fukukawa89/PoseDollLab_Design/Hardware/PoseDoll44/bench/revO15/PROCUREMENT_MANNY.zh-CN.md

# Manny 采购数量

现有小样能复用的标准金属件可扣除。塑料件按整机编号，不混用旧底座。

| 规格 | 净数量 | 可选备件 | 建议总数 |
|---|---:|---:|---:|
| A8不锈钢碟簧：8×4.2×0.4，自由高0.6 mm，弹力待测 | 104 | 11 | 115 |
| Rev C mini传感PCBA：12×10×1 mm，按配套电路文件加工 | 46 | 2 | 48 |
| O15 C1中央采集PCBA：70×60×1.2 mm，四层板，按配套电路文件加工 | 1 | 0 | 1 |
| 6P 0.5mm FFC短尾线，宽3.5、厚0.2、长15 mm；每端补强≥3.5 mm，按图加六根32AWG短引线 | 46 | 4 | 50 |
| 1×7、2.54 mm排针；XIAO与载板间距4.0 mm定位焊接 | 2 | 0 | 2 |
| JST GHR-06V-S壳+SSHL-002T-P0.2端子；26AWG短引线转24AWG，绝缘外径0.76–1.0 mm，6P、1.25 mm；让线束厂压接 | 6 | 0 | 6 |
| JST PHR-2壳+SPH-002T-P0.5S端子，2P、2.0 mm；5V输入 | 1 | 0 | 1 |
| JST PHR-3壳+SPH-002T-P0.5S端子，3P、2.0 mm；降压模块连接 | 1 | 0 | 1 |
| 径向两极磁铁 Φ6×2.5 mm；直径方向充磁，不能买轴向充磁 | 46 | 5 | 51 |
| Nitecore Carbon Battery 6K，5V输出，包络Φ22.8×90.4 mm | 1 | 0 | 1 |
| M1.6普通六角螺母（不要锁紧螺母替代外形） | 36 | 4 | 40 |
| M2普通六角螺母（不要锁紧螺母替代外形） | 182 | 19 | 201 |
| M3普通六角螺母（不要锁紧螺母替代外形） | 130 | 13 | 143 |
| Pololu D24V22F3 固定3.3V降压模块；禁止买F5版本 | 1 | 0 | 1 |
| M1.6×6 内六角圆柱头螺钉；按CAD头径/头高核对 | 36 | 4 | 40 |
| M2×16 内六角圆柱头螺钉；按CAD头径/头高核对 | 4 | 2 | 6 |
| M2×20 内六角圆柱头螺钉；按CAD头径/头高核对 | 48 | 5 | 53 |
| M2×4 内六角圆柱头螺钉；按CAD头径/头高核对 | 24 | 3 | 27 |
| M2×5 内六角圆柱头螺钉；按CAD头径/头高核对 | 68 | 7 | 75 |
| M2×6 内六角圆柱头螺钉；按CAD头径/头高核对 | 6 | 2 | 8 |
| M2×8 内六角圆柱头螺钉；按CAD头径/头高核对 | 32 | 4 | 36 |
| M3×20 内六角圆柱头螺钉；按CAD头径/头高核对 | 32 | 4 | 36 |
| M3×8 内六角圆柱头螺钉；按CAD头径/头高核对 | 46 | 5 | 51 |
| XIAO配套A-02 2.4GHz FPC天线，37.4×17.5 mm，65 mm同轴线 | 2 | 0 | 2 |
| 轴肩螺钉 Φ4×8 / M3×0.5，螺纹长6 mm；头Φ7×3，内六角3 mm | 52 | 6 | 58 |
| 5V USB-C弯头电源线；电池端伸出≤16 mm、外包络8×8 mm，进盒PH2 | 1 | 0 | 1 |
| M3大平垫圈：外径9、厚0.8 mm，实物通孔验证 | 52 | 6 | 58 |
| M4大平垫圈：外径12、厚1 mm，实物能自由套过Φ4光杆 | 104 | 11 | 115 |
| M4普通平垫圈：外径9、厚0.8 mm，实物通孔验证 | 52 | 6 | 58 |
| Seeed XIAO ESP32S3 普通版；人偶BODY和桌面G0各一块 | 2 | 0 | 2 |

另外准备：24AWG电源主线、26AWG的GH插头短线、30AWG信号、32AWG局部引线；长度见harness。工具、绑线带、绝缘、标签、USB数据线和PCBA/线束加工服务见guide.html。没有定制金属加工件。
GH端子必须SSHL-002T-P0.2，不能用SHL系列端子替代；压接端使用26–30AWG、绝缘外径0.76–1.0mm，24AWG只能在插头外转接。
