fukukawa89/PoseDollLab_Design/Hardware/PoseDoll44/cad/revO15/WORK.md

# O15 完整数字样机与统一实物验证包 — 2026-09-30

当前状态：DIGITAL_PROTOTYPE_BATCH_READY_FOR_PHYSICAL_VALIDATION。以下历史段落保留开发过程，不再代表当前待办。用户授权按小样正常可用的条件推进全机；没有把假设改写为实物验收。

本轮已完成全身关节、连接架、头手足、背部控制器/电池盒、46块传感板的布置、6条逻辑链、中央C1与外置G0、固件和UE桥接、采购/打印/线束/装配/集中测试资料。480mm参考、910mm备用、静态采集、允许手托和取消1.2kg硬门槛保持不变；没有定制机加工金属件。

最终入口：tutorials/full-doll-o15/index.html 和 guide.html；bench/revO15 的 Quinn/Manny Prototype.zip 各是一套完整备选，不能相加采购。每套214种打印文件、273件打印件；两型合计242种几何。242个实际通用切片通过；文件给出贴床方向与支撑要求，仍由服务商按实际机器重新切片。

数字证据：两型各416步原始角度路径、最终设备和刚性尾线各689工况检查；自身FFC与端部包封的重叠单独保留见证，未发现未解释的结构干涉。两块板原生ERC/DRC和连通性通过；BODY/G0最终编译通过；桥接64项测试通过；真实UE接收合成PDG15经生产BridgeCore的正常/缺失/CRC/重启反例通过。不是连续运动、强度、完整手工装配或柔性线缆仿真证明。

条件质量预算：Quinn 1.67318kg、Manny 1.65311kg；最大采样重力矩约0.384/0.379Nm。46轴实测标定仍为空，默认设备未配对，禁止将未标定读数作为正式姿势。强度、摩擦保持/起动力、蠕变磨损、带线运动、供电瞬态和电子实测归入同一批实物验证。

最后交付QA：FINAL_EVIDENCE_INDEX的23个报告与114个Python源码哈希全部匹配；两个ZIP各512个文件，510项内容哈希及ZIP CRC通过，214种/273件数量一致。查看器、中文指南、两个ZIP的本地HTTP入口均返回200；中文HTML明确UTF-8。浏览器加载最终Quinn实体完成，控制台0错误/0警告；此前已验证Manny、部位过滤、单件显示、分解动画、中文检索与记录表保存/恢复，不留下模拟实测记录。

Quinn ZIP SHA256: 83981bd77a43e3ca6ae00cf691d2a072229715fc54f09c2cc00b507f0e017b36
Manny ZIP SHA256: e80579b8bd3ac2b2960c1bd5a562b0e81753d15b79569c7e625a4b0cf09d9ebc

本轮未提交commit或push（用户本轮未要求）；先前工作树和历史失败见证保留。服务8769保持运行。

---

以下为开发历史（已被上面的最终状态取代）：

# O15 whole doll design in progress — 2026-09-30
User requests one consolidated full-doll print/purchase/test batch, with conditional O12 usability. No intermediate physical test pauses. No commit requested. No subagents.
Libraries and nominal sampled assembly paths repaired: open washer cups/removable magnet seat, removable keyed PCB cradle, wide ring insertion lead-in, captured hinge nuts/M3x20, twist M3x8 adjuster. Six families assembly paths clear. Raw46 -> semantic41+fixed3 fault checks pass; production acquisition integration not done.
Current source: protract mount [-40,18,0] phase45, elevate[36,11,7]phase175. Torso109 associated checks running session56035. New forearm search found L delta[-4,-4,0] phase60; R[-4,4,-4]phase90, not yet adopted. Axial-only search failed. Current full connected Quinn109 had78 hard findings inherited from endpoint solids; solve layout then regenerate carriers and endforms. No hiding adjacent collisions as pose contacts.
Current carriers_swept both characters generated positively connected; obsolete after protract source edit. Full109 audit required. Endforms Quinn7 generated on old geometry, regenerate. Common.solid_count correctly counts positive material shells; enclosed negative cavity shells are not disconnected parts, independent controls passed.
Active sessions:56035 torso associated audit. Other search processes done. Server8769 running; tutorial stale/in-progress. Preserve prior outputs and sealed O14. No final printpack/slicing, mass/loads, harness/controller/raw46transport, final viewer/testguide or seal yet.
Mechanical assumptions: 480mm reference, qualitative proportion changes permitted but no numeric tolerance approved. Manual support allowed. Masscap and realtime timing not gates. Nonadjacent pose contacts retained, neutral has contacts, assembly arms30/hips8 is clear in old candidate.

Update: latest adopted forearm mounts L[-6,-4,0]phase30, R[-4,4,-4]phase90. Protract[-40,18,0]. Associated attachment endpoint audit218 poses zero. Both new carriers and7 endforms generated. Full finished-body109 endpoint check Quinn0hard; Manny5hard (thigh route vs chest/P_case_minus carried on waist; clavicle routes vs head/P_case_minus carried on chest). Cause: router swept endpoint modules independently, missing inherited whole-frame associations. Fixed swept_obstacles endpoint_associations; rerouting both now sessions1534/6228. Prior candidate saved history_before_frame_association_fix.
Semantic linear interpolations have19 discontinuities up to332degrees; cannot serve as physical paths. raw_paths.py now linearly interpolates actual bounded raw axes,5deg/sample;514 samples/char,152 out-of-semantic-capture-range transits, no mapping error. Do not call those capture-valid. Associated raw path collision check session61962 running Quinn. audit_raw_paths.py exists but not run. Continuous_bank failed results preserved.
New scripts export_print_batch.py and load_budget.py prepared, syntax checked but not executed. No final print package or load report yet. Manufacturer Seeed XIAO files downloaded for exploration only, NOT adopted: references/revO15/seeed_xiao. Official design_v14 URL archive actually Sensev1.5; must not silently treat as matching plain3D model. No new electronics/firmware/wiring/controller architecture adopted or implemented. UE actual project E:/UnrealProjects/DollSimulation; legacy PDS1 accepts6/8boots and100ms scan.

Adopted shoulder F roll +120 degrees; local left Quinn endpoint/path trial passes, full bilateral/both-character audits rerunning. Routing association fix completed both characters before phase change; carriers/endforms now need regeneration. No controller architecture adopted.

2026-09-30 current: endpoint associated audit218 zerohard after shoulder roll120. Independent load finite-difference check92/92 passes after determinant sign correction and adding downstream modules internal bodies. Before-fix log retained. Raw path check switched to per-original-endpoint equivalent union test, Quinn active session43538; query progress active_query_quinn.json. Slow TBB/CSG; do not start multiple heavy processes yet. Manny needs run. Carriers not regenerated sincephase. Controller STEP inspection37validsolids extent22.482x4.46x17.78 includingUSB; manufacturer modelv2 vsdesignarchivev1.5 mismatch retained.

Electronics exploration proposal, NOT BUILT/ADOPTED: one XIAO ESP32-S3 central MCU + external G0 XIAO via ESP-NOW; six daisy regions raw counts6(waist/chest),4(head),10eacharm(clav2+shoulder4+elbow1+forearm1+wrist2),8eachleg(hip4+knee1+ankle2+toe1)=46. 100kHz six register bursts nominal44.16ms. Six logical regions share one physical failure domain/boot; don't claim six physical nodes. PDG15 newraw46 protocol needed; PDS1output44semantic mapped through inverse DeviceProfile calibration, not sent as bare sensor angles. Default diagnostic, real commissioning/calibration required. Existing O5/PD41 unchanged.
Power candidate PololuD24V22F3 fixed3.3 from5V USB; Chinese XIAO+protectedNitecoreCarbonBattery6K5V2A(official90x22.8 or90.4length; mustresolve beforeCAD). Independent central customcarrierPCB, perregionTPS2553-1DBV switchRlim88.7k1%(catalog262.1..342.3mA), buffersperbranch not sharedrail topreventbackfeed whenbranch off: oneSN74LVC125Apoweredbranch3.3 forSCK/MOSI/CS, OEeachbranchpulledtoitsownrail47k and2N7002drain(gatescommonMCUGPIOenable,pulldown100k), oneSN74LVC1G125poweredMCU3.3 forreturnMISO, OEfromthatbranchCS, inputpulldown100kGND(noMCUrailpullupintooff AS). CandidateGPIOCS[2,4,5,6,43,44],SCK7,MISO8,MOSI9,enable1;GPIO3unusedstrap. SensorconnectorGH6pinsGND,VCC,SCK,MOSIforward,MISOreturn,CS. Needrealboard+ERC/DRC+powerderating+cabledesign+firmwarecompile+hostfaulttestsbeforeanyclaim. Mainpower26/24AWG,sensorFFCtailshort15mAtap;6conductorsperdaisylink includingreturnbypass. PrototypefactoryPCBA acceptable; no custom metal. PCBspatial target52x54withXIAOtop/Pololubottom is ONLYtarget untilbuilt. Don't present as tested or finalized.

2026-09-30 continuation: Quinn associated raw paths COMPLETE zero hard (441938 exact queries); no tubes, discrete proof only. Manny running session24569. BODY initial IDF build failed only array-parameter declaration mismatch; fixed plus physical bodyMAC identity binding and BODY_SCAN mask/word validation. Rebuild needed. New protocol files Firmware/PoseDollFullBody/revO15/{raw46.c,h,test_raw46.c,main/main.c,build.ps1}; native1536packet bit flips,192truncations,4400sensor flips first pass, rerun after fixes. Tools/PoseDollHardwareBridge/{pdg15.py,o15_bridge.py} candidate core created, no CLI/tests yet. raw_wiring.py generated46one-to-one logical chains. No actual controller PCB/power layout/harness/case/qualification yet.

Manny associated raw paths COMPLETE, zero hard; both416samples, original attachments only. BothBODY/G0compilefirstpassed; BODYneedsrebuildafteraddederrorclearing. Pythonnewbridge64tests passed, nativebitfaulttestsagainpassed. RealUEtest rerun82335 afterabsolute-scriptfix (firstattemptdidnotrun). ActualPCBnewbuild_controller.py generates150components82nets70x60mmcentralC1 with6branchlatch-offs, 4SN74LVC1G125DBVRperbranch. TIquad125hasnoIoffguarantee inreviewedspec, replacedwith1G125. KiCadERC0 andplacementDRC0,343airwires before routing. route_controller.py creates2innerplanes+explicitDSNpowerclasses. Freerouterfirstprocess21144maybestuckstartup;needs--gui.enabled=false -da --user_data_path localdir. DownloadedverifiedportableJRE25in.local/tools/temurin25,hash4c95451cea98556def2c54f7782933f52a26d4a36bd85e1d59f0364464828b07. No productionrelease. Carrierrouter nowexpanded15degrawtransits, regenabouttostart. Final5degauditmandatory.

Latest03:17: initial C1autoroute completed0unrouted inrouter butKiCad137minwidth+4GNDunconnected; actual projectSaveBoard resetdesiredrules. Manualmidpointgroundviasfailedandhavebeenoverwrittenbyfreshsourcebuild, don'tuse refine_controller.py blindly. Currentbuild162components+82nets, ERC0placementDRC0; added2extradecapsperbranch(each1Gbufferhasassigned0.1u). AllR/Cbackcourtyardpacking, headerXIAOfrontcenter;70x60board4M2holes(11,3),(59,3),(3,57),(67,57). route_controller marksIn1/In2 typepower (signalsouteronly) andexplicitDSNclasses; autoroute session51584 r2currently61unroutedpass3, notdone. finishrestores800/400powerviapadstackanddesired min0.15track0.15clear0.30edge0.15annular afterSaveBoard;needsactualDRC. raw pathreportsboth416,0hard. Quinncarrierwithadded15degtransits session11093active21frames (upperarm_l last), manyrootsfinishedzeroissues, nextlongroute. audit_raw_paths rewrittenefficientreuseoflockedpriororiginal-attachmentreport whiletestingallnewframes+same-bodypairs, NOTRUN. endformsnotregenerated. RealUEraw46bridge integration actualsuccesssavedue_bridge_result.json normal1capture/missingCRCboot0. FirmwareBODY/G0bothfinalcompilespass reportfirmware_builds.json. raw_wiring regeneratedadditionalerrorclearbursts worst58.88ms(notphysicaltime). Nohousing,harness,fulltools,actualprint/slicing/BOMfinalyet. No final/commit.
