fukukawa89/PoseDollLab_Design/Hardware/PoseDoll44/docs/REVIEW_REQUEST_REVO15.zh-CN.md

# O15 完整数字样机与统一实物批次审查

用户要求：按现有试用件正常可用的条件继续整机设计；不在每个硬件测试点停下；最后一次交付全部采购/打印资料。仍不把条件假设记成实测通过。480mm参考，910mm备用不变；静态采集；无1.2kg硬门槛；允许手托；优先家用FDM+现成金属小件。

入口：cad/revO15/WORK.md、generated/revO15/runs/o15_20260929_r1/FINAL_BATCH_SUMMARY.json、bench/revO15/guide.html、tutorials/full-doll-o15/。本轮尚未额外提交commit；请以随后提交的工作树内容审查。

本轮包括全身关节/实体连接架/头手足/背部控制盒和电池盒、46个编码器、6条静态采集链、一块中央BODY载板+外置G0、固件与生产桥接器、打印与电子加工资料。每个体型273件打印件，214种文件；两型合计242种几何。

实际检查：局部装配/PCB保持几何；原始关联附件与最终连接架416步原始角度路径；新增设备和全部刚性FFC尾线各689个离散工况；原生KiCad ERC/DRC及连通性；BODY/G0构建；64项桥接测试；真实UE接收合成PDG15经生产桥接的正常/缺失/CRC/boot反例；242个STL真实通用切片、支撑底层凸包与逐层挤出重心检查。范围和哈希在对应报告中，不能据此宣称连续扫掠/强度/疲劳已证明。

请重点审查：
1. 多轴与全身手工装配路径、工具可达性、打印层方向和最薄受力截面。局部几何连通不能代替完整结构强度；最终控制盒盖加大螺母柱上段、GH插头按原厂8.75mm宽度修正。
2. 原因明确的FFC让位槽：Quinn最大切除约0.58%；Manny前臂的两个亚层厚度碎屑移除并记录，不是删掉受力零件。尾线与自身绝缘转换包封的2.45mm³重叠是同一实物两个包络，所有31694条原始见证保留并明确归类，没有忽略两个独立硬件的碰撞。
3. 柔性导线仍无力学/疲劳/连续碰撞证明。长度由689个端点跨度+服务环余量计算；24AWG电源连续分支、26AWG短引线转GH，30AWG信号，32AWG局部尾线。实际绕法、夹线和手感留同批实测。
4. 中央C1原生ERC/DRC为0，但尚无供电瞬态、热、SPI、ESD/RF实测。最远端条件预算仅约42mV余量；电阻和电流是假设边界，实际不能越过3.0V最低供电。
5. 保持力/回差/材料蠕变/疲劳均未测。质量约1.65–1.67kg是逐件+线束预算，用户允许手托；不得靠加大预紧掩盖承压问题。
6. 46原始量合成41测量语义+3固定骨盆，6链同一个物理BODY失效域；静态窗口保留数据完整性与新鲜度，不是恢复旧60Hz指标。MAC默认未配对，标定表为空；缺失/故障不允许保存。
7. UE语义端点与真实外形不同。参考末端最大偏差约16mm，轴心最大偏差约53mm；没有用户批准的数值容差，不得宣称骨架位置完全一致。

制造验收和完整实物功能仍未放行。现在交付的是完整数字样机和统一试制/验证批次，不是已经做好的实体人偶。
