fukukawa89/PoseDollLab_Design/Hardware/PoseDoll44/bench/revO22/a1mini_supports/PACKAGE_README.zh-CN.md

# O22 A1 mini PLA 支撑工程包

请先阅读 [打印与拆除说明](README.zh-CN.md)，先试印 S00。主盘 A01–A10 共 186 件（185 件整机零件 + 1 件量规）；S00 七件试印件和 T01 两件可选小样单独计算。

| 打印盘 | 内容 | 件数 | 预计用时 | 切片估算耗材 | 工程 |
|---|---|---:|---:|---:|---|
| S00 | 先试印：支撑拆除与小孔配合 | 7 | 2时26分 | 33.7 g | [S00_support_trial_PLA_supports.3mf](projects/S00_support_trial_PLA_supports.3mf) |
| A01 | 头颈与背盒盖 | 20 | 4时23分 | 66.6 g | [A01_head_PLA_supports.3mf](projects/A01_head_PLA_supports.3mf) |
| A02 | 躯干 1/2 | 13 | 10时37分 | 206.3 g | [A02_torso_1_PLA_supports.3mf](projects/A02_torso_1_PLA_supports.3mf) |
| A03 | 躯干 2/2 | 15 | 3时11分 | 44.9 g | [A03_torso_2_PLA_supports.3mf](projects/A03_torso_2_PLA_supports.3mf) |
| A04 | 左臂 1/2 | 11 | 4时52分 | 74.2 g | [A04_left_arm_1_PLA_supports.3mf](projects/A04_left_arm_1_PLA_supports.3mf) |
| A05 | 左臂 2/2 | 26 | 5时15分 | 83.7 g | [A05_left_arm_2_PLA_supports.3mf](projects/A05_left_arm_2_PLA_supports.3mf) |
| A06 | 右臂 1/2 | 14 | 6时51分 | 112.9 g | [A06_right_arm_1_PLA_supports.3mf](projects/A06_right_arm_1_PLA_supports.3mf) |
| A07 | 右臂 2/2 | 23 | 2时46分 | 41.1 g | [A07_right_arm_2_PLA_supports.3mf](projects/A07_right_arm_2_PLA_supports.3mf) |
| A08 | 左大腿与左腿关节小件 | 27 | 4时41分 | 67.5 g | [A08_left_leg_PLA_supports.3mf](projects/A08_left_leg_PLA_supports.3mf) |
| A09 | 右大腿与右腿关节小件 | 27 | 4时35分 | 64.4 g | [A09_right_leg_PLA_supports.3mf](projects/A09_right_leg_PLA_supports.3mf) |
| A10 | 双侧小腿与脚掌骨架 | 10 | 7时44分 | 123.4 g | [A10_lower_legs_PLA_supports.3mf](projects/A10_lower_legs_PLA_supports.3mf) |
| T01 | 可选：O22 传感器安装小样 | 2 | 1时01分 | 7.1 g | [T01_sensor_coupon_PLA_supports.3mf](projects/T01_sensor_coupon_PLA_supports.3mf) |

时间和耗材为切片估算，未做实物打印。所有工程包含原生打印配置和实际切片，可直接在 Bambu Studio 中预览。

包内不附大体积的网页路径二进制。原工作区的本地交互预览入口：[http://127.0.0.1:8770/bench/revO22/a1mini_supports/index.html](http://127.0.0.1:8770/bench/revO22/a1mini_supports/index.html)。本地服务运行时可访问；这个地址不是公网网站。离线打开 .3mf 工程仍可在 Bambu Studio 内看全部支撑与路径。manifest.json 中 preview 字段供完整本地工作区使用。

verification/ 保存原生往返、实际路径与孔槽保护核心检查；design/ 包含保护区域定义。检查范围仅限声明的保护核心，不证明实物一定易拆。
