fukukawa89/PoseDollLab_Design/Hardware/PoseDoll44/bench/revO12/reference_images/A8_disc_spring.png

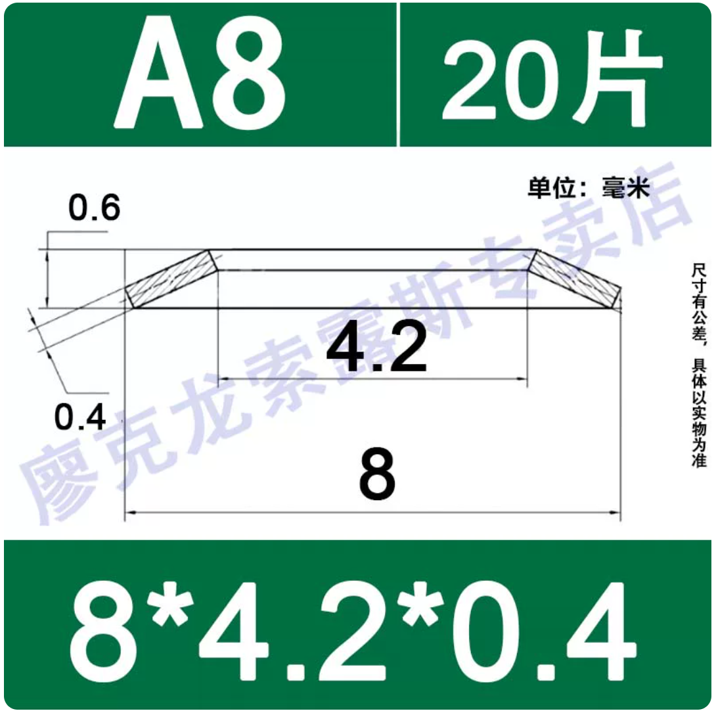
Hardware/PoseDoll44/bench/revO12/reference_images/A8_disc_spring.png
