fukukawa89/PoseDollLab_Design/Hardware/PoseDoll44/bench/revO12/reference_images/M3_hex_nut.png

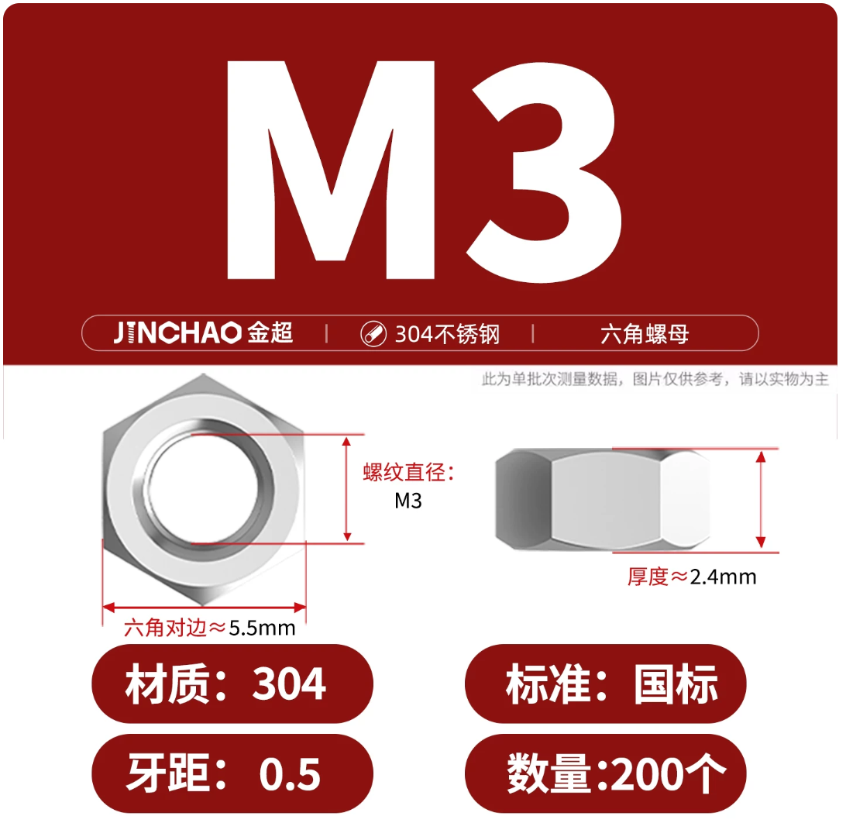
Hardware/PoseDoll44/bench/revO12/reference_images/M3_hex_nut.png
