fukukawa89/PoseDollLab_Design/Hardware/PoseDoll44/bench/revO12/reference_images/M3x35_socket_head_screw.png

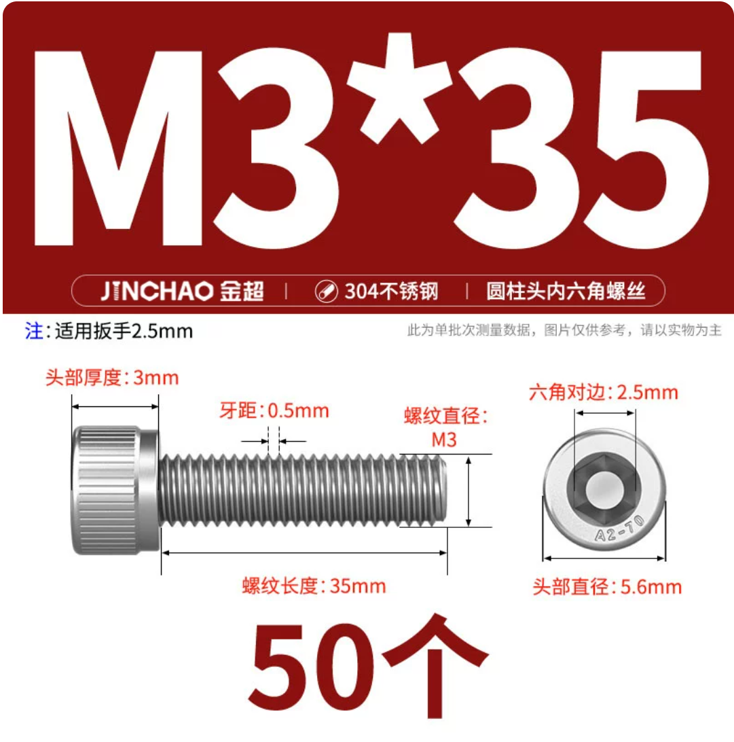
Hardware/PoseDoll44/bench/revO12/reference_images/M3x35_socket_head_screw.png
