fukukawa89/PoseDollLab_Design/Hardware/PoseDoll44/bench/revO12/reference_images/M4_wide_washer.png

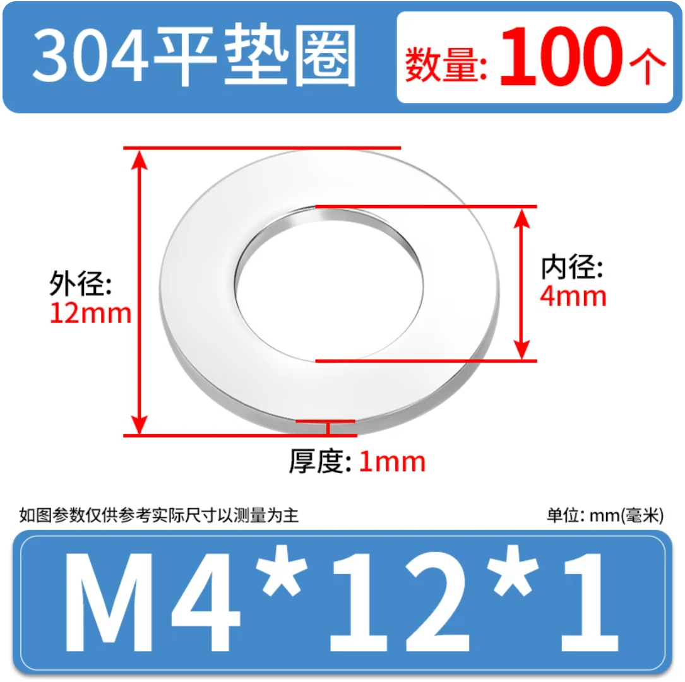
Hardware/PoseDoll44/bench/revO12/reference_images/M4_wide_washer.png
