fukukawa89/PoseDollLab_Design/Hardware/PoseDoll44/bench/revO12/reference_images/shoulder_screw.png

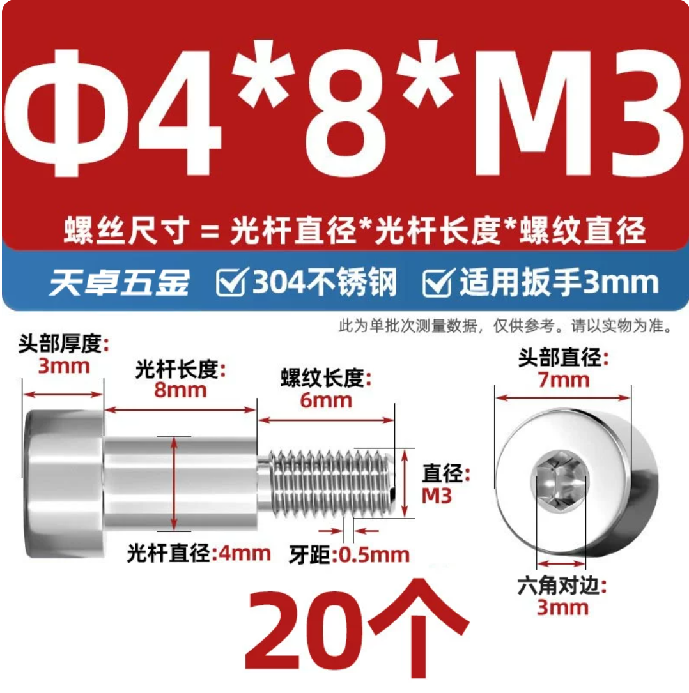
Hardware/PoseDoll44/bench/revO12/reference_images/shoulder_screw.png
