fukukawa89/PoseDollLab_Design/Hardware/PoseDoll44/bench/revO21/mechanical_reference_O20.png

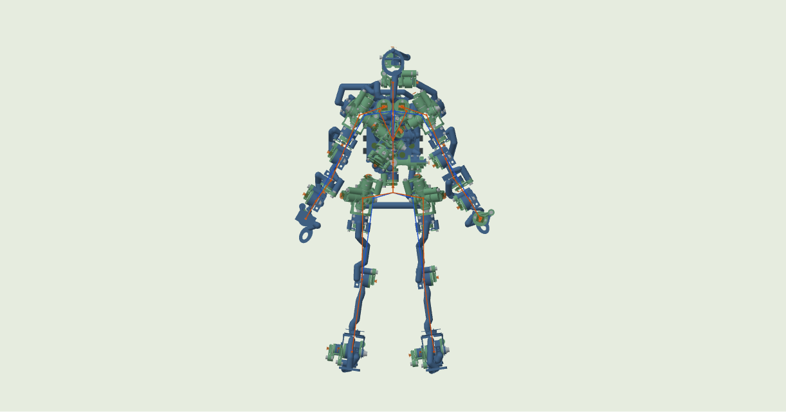
Hardware/PoseDoll44/bench/revO21/mechanical_reference_O20.png
