fukukawa89/PoseDollLab_Design/Hardware/PoseDoll44/bench/revO22/a1mini/previews/A10.png

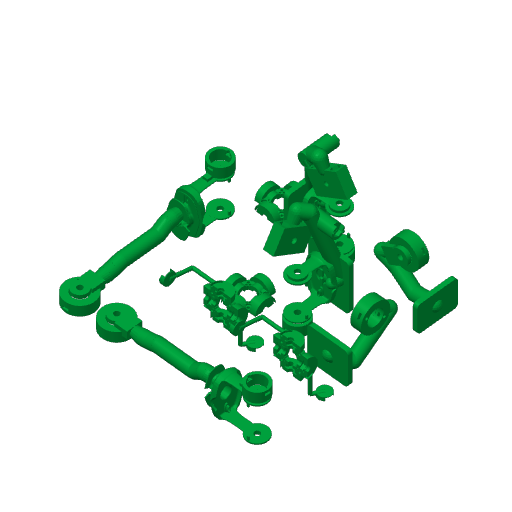
Hardware/PoseDoll44/bench/revO22/a1mini/previews/A10.png
