fukukawa89/PoseDollLab_Design/Hardware/PoseDoll44/electronics/sensor_revO5CN/preview/back.png

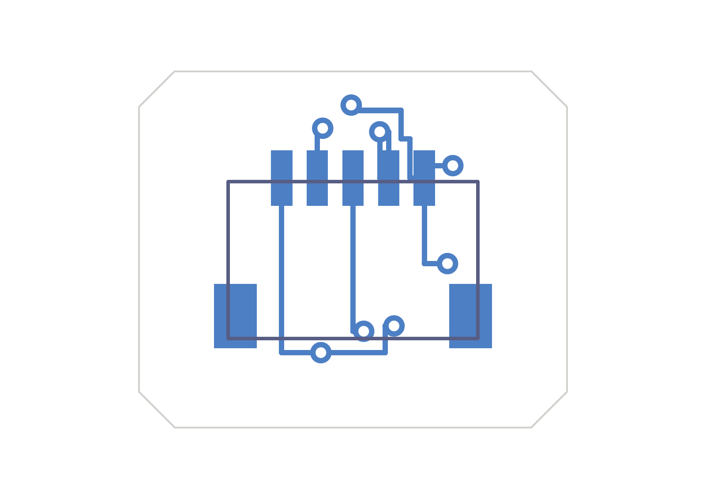
Hardware/PoseDoll44/electronics/sensor_revO5CN/preview/back.png
