fukukawa89/PoseDollLab_Design/Hardware/PoseDoll44/generated/revO8/runs/o8_20260925_r1/core_preview.png

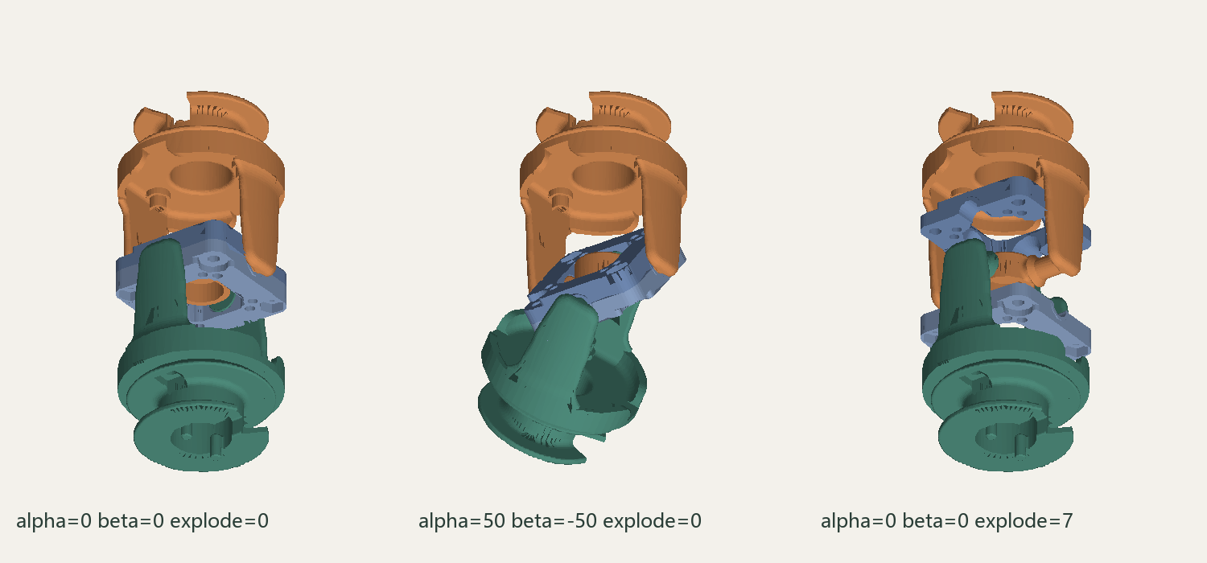
Hardware/PoseDoll44/generated/revO8/runs/o8_20260925_r1/core_preview.png
