fukukawa89/PoseDollLab_Design/Hardware/PoseDoll44/references/revO15/pololu_d24v22fx_dimensions.png

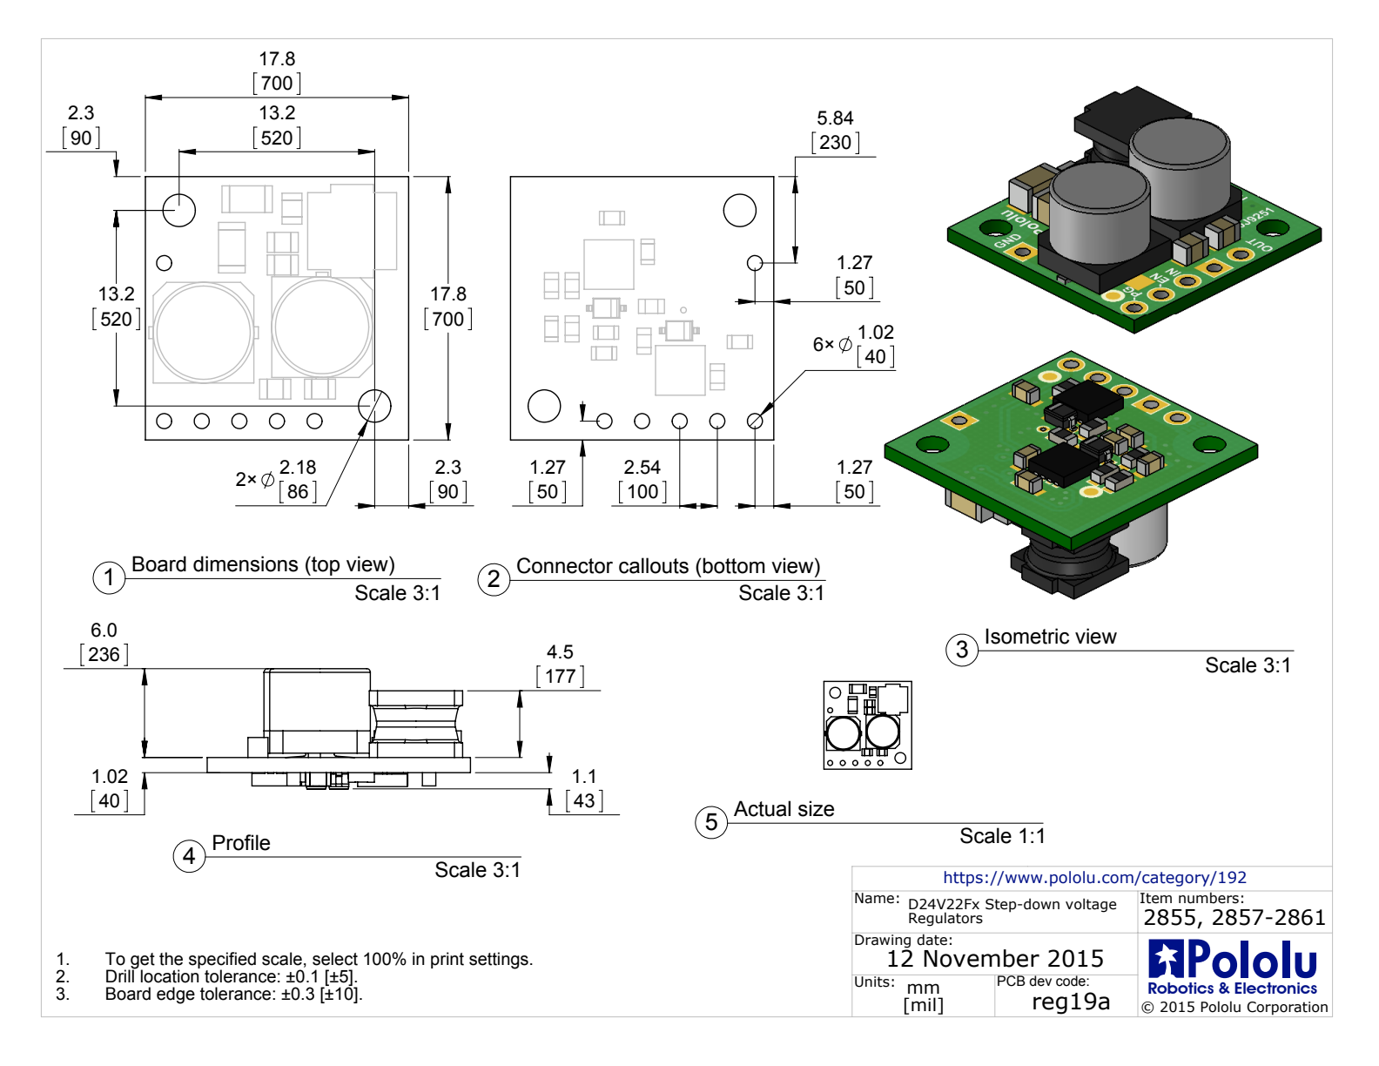
Hardware/PoseDoll44/references/revO15/pololu_d24v22fx_dimensions.png
