fukukawa89/PoseDollLab_Design/Hardware/PoseDoll44/references/revO15/seeed_fpc_antenna_A02.png

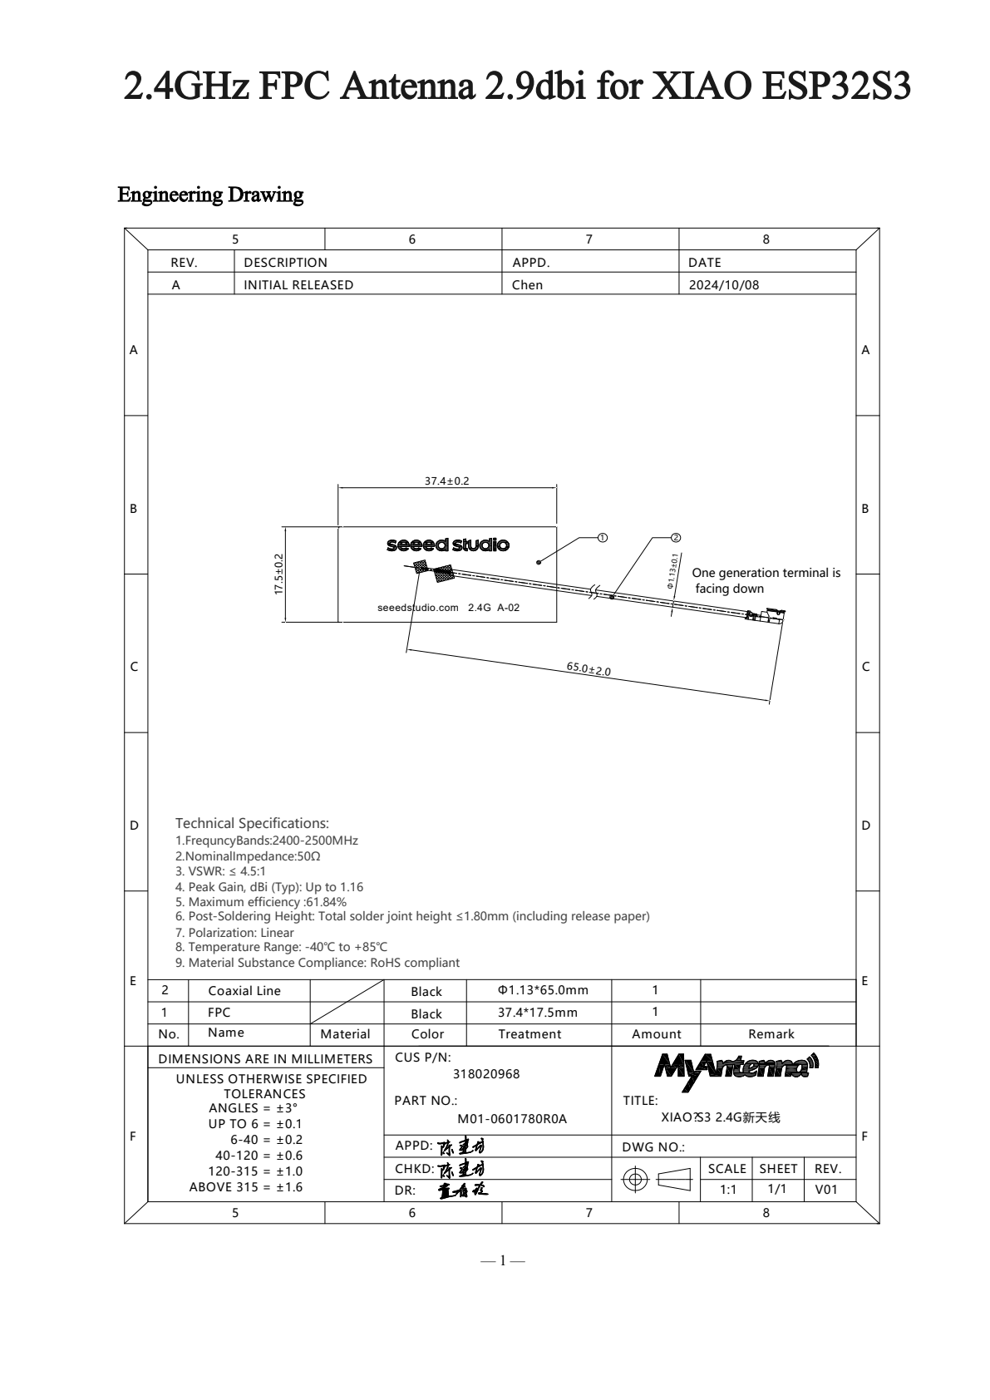
Hardware/PoseDoll44/references/revO15/seeed_fpc_antenna_A02.png
