fukukawa89/PoseDollLab_Design/Hardware/PoseDoll44/tutorials/tut-prototype/verification/mobile-design.png

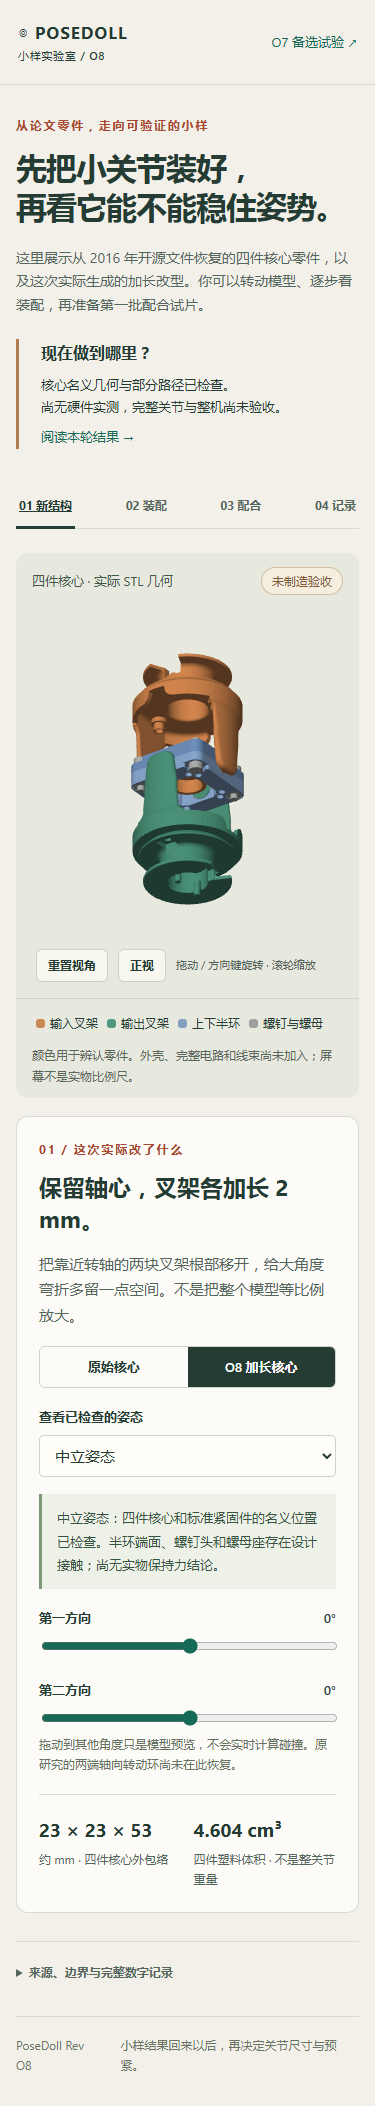
Hardware/PoseDoll44/tutorials/tut-prototype/verification/mobile-design.png
