fukukawa89/PoseDollLab_Design/Hardware/PoseDoll44/bench/revO10/GETTING_PARTS.zh-CN.md

# O10 零件获取指南（补充修订）

更新：2026-09-26。适用于独立摩擦小样。本页纠正旧指南中“有 STL 就要打印”的歧义，并补充零件来源；下面的尺寸仍是 O10 名义设计值，不是已确认可下单的完整采购清单。

**以下说明当前金属基准小样的获取方式，不代表底座必须用金属。** 底座主体可以研究改为打印件，详见[打印材料替代评估](MATERIAL_OPTIONS.zh-CN.md)。在尚未完成替代设计之前，原方案的铝底座仍按铝料机加工，钢片和垫圈仍按金属件准备；不能仅更换 STL 的打印耗材就沿用原方案结论。 旧指南“打印排版时需要落到平台”的说明只应适用于塑料长臂。STL 表示外形网格，不指定材料；STEP 也只是几何文件，材料、公差和表面要求需要另行说明。

## 各零件怎样获得

尺寸统一按“外径 × 内径 × 厚度”列出，单位 mm。

| 零件 | 数量参考 | 制作或购买方式 | 当前落实程度 |
|---|---:|---|---|
| 铝底座 | 1 | 交给 CNC 机加工服务商，用 6061 铝料铣削、钻孔。可向嘉立创 CNC 评估 6061-T6 方案；不是铝粉打印 | 已有 STEP；30×30×8、3 个 Ø4.4 通孔。表面、公差及夹具方案仍需补齐后确认加工 |
| PA12 长臂 | 3 | 外包 PA12 打印，当前候选是嘉立创 MJF PA12；材料、方向和后处理须与之后关节的试验方案一致 | 已有 STEP/STL；不能用 PLA、PETG、光敏树脂或 PA12-CF 的测量结果代替这一材料组合 |
| 钢接触片 | 2，可备重复件 | 先匹配成品精密垫片；没有匹配件时，交给精密金属薄片厂按图切割、去毛刺，并控制平整度和表面 | 12×4.24×0.5 是自定义设计尺寸。目前未落实成品型号，也未冻结钢材牌号、粗糙度和加工图 |
| 前承压垫圈 | 1 | 购买符合要求的钢制精密薄垫片；无匹配型号时定制。不能用塑料打印件代替 | 9×4.3×0.3 是名义尺寸，尚无已核实商品。0.3 厚不能当作普通 M4 平垫圈厚度 |
| 后承压垫圈 | 1 | 优先买钢制 M4 标准平垫圈，再核对尺寸和材质 | 9×4.3×0.8 在嘉立创 FA 标准平垫圈目录中有对应尺寸；具体材质、完整型号、硬度及供货仍待核对 |
| A8 碟簧 | 6 | 购买锐尔立等弹簧厂的成品碟簧，不能用普通平垫片或塑料件替代 | O10 候选为 8×4.2×0.4，两片反向一组；以厂家供货规格为准，目录力不是实测力 |
| M4×20 螺钉、M4 螺母 | 各 1 | 从紧固件供应商购买标准成品 | 需核对头型、强度等级和实际尺寸；改变垫片厚度时，先重新核对螺钉长度和堆叠 |
| 固定支架、底座安装螺栓、挂线与测量工具 | 按夹具配置 | 优先使用或购买合适的现成夹具、紧固件和测量工具 | 固定支架的具体实现尚未形成完整采购项；不能让底座自由晃动，也不能夹住移动长臂 |

钢接触片是夹着塑料长臂、参与摩擦的圆环；承压垫圈则分布在螺钉头和螺母附近，传递夹紧力。它们外观相似，用途和尺寸不同。外径 9 mm 的普通垫圈不能直接取代外径 12 mm 的摩擦接触片。

## 文件具体交给谁

- [铝底座 STEP](aluminium_base.step)：给机加工方核对几何。现有 aluminium_base.stl 仅作外形参考；即使用塑料打印出外形，也不等于得到了本试验所需的铝底座。
- [PA12 长臂 STL](PA12_lever.stl) / [STEP](PA12_lever.step)：给 PA12 打印服务商。零件当前位于装配坐标，打印时应单独安排方向、落到打印平台；方向与表面处理要记录。
- 钢接触片和前薄垫圈：目前没有完整采购型号或带材料、公差、表面要求的加工图。不能只拿动画截图去下单，也不能把商家自行挑选的钢片视为同一种试验材料。
- [旧版装配与测量步骤](README.zh-CN.md)：继续用于理解装配及加载；其中材料获取、STL 用途以本页的修订说明为准。

## 为什么不在家打印铝

普通家用 FDM 打印机通过喷嘴挤出热塑性材料，常见光固化打印机处理树脂。工业金属增材设备可以打印铝合金，但它使用专门设备和工艺，不是给普通家用机换一卷“铝耗材”。本底座是简单的带孔铝块，当前选择机加工。[工艺说明](https://jlc3dp.com/hk/capabilities/3d-printing-service)、[EOS 铝合金金属打印](https://www.eos.info/metal-solutions/metal-materials/aluminium)

常见带金属粉的装饰性 PLA/PETG 仍是复合塑料，不能按铝件或钢件的机械性能使用。特殊需脱脂、烧结的金属料体系也不属于本次家用打印方案。[Prusa 材料说明](https://help.prusa3d.com/article/composite-materials-with-metal-or-wood-particles_166863)

## 已核对的中国供应渠道

这些链接证明服务或目录存在，不代表本零件已经询价、可制造性确认或验收通过；本轮未联系供应商、未上传模型、未下单。

- [嘉立创 CNC](https://www.jlc-cnc.com/home)：列有 6061-T6、铣削与车削服务，作为铝底座机加工渠道。
- [嘉立创 MJF PA12](https://www.jlc-3dp.cn/materialDetail/efe4966ee81f4ddb92039f46689e7596.html)：当前塑料小样的候选打印渠道；不是所有名为“尼龙”的商品都可互换。
- [嘉立创精密金属薄片](https://cut.jlc-gw.com/)：列有 304 薄片、按图激光切割及去毛刺服务。可以作为钢接触片的候选定制渠道，但 0.5 mm 厚度、钢材、平整度及摩擦表面仍须确认；本页没有将钢材自动改定为 304。
- [嘉立创 FA 平垫圈目录](https://static.jlcfa.com/Serial/E06/EPDA/542502462063341570.pdf)：第 1 页标准型 M4 行为内径 4.3、外径 9、厚 0.8。该行只对应后垫圈的名义几何，不证明前方 0.3 mm 薄垫圈也可买到。
- [锐尔立碟簧](https://www.raleigh-spring.cn/discspring/list_84_2/)：成品弹簧渠道。具体交货等级、批次和尺寸需跟供货规格对应。

**上一版完成了数字模型和试验方法，但交付给新手的采购准备仍不完整。** 钢片的牌号和表面、前薄垫圈的可购型号或定制图、以及夹具的具体配置，是设计侧需要继续补齐的事项，不应让使用者自行猜测。确认真实供货尺寸后，还须核对堆叠与弹簧工作位置；本页没有悄悄改变 O10 几何，也没有新增实物合格结论。
