fukukawa89/PoseDollLab_Design/Hardware/PoseDoll44/bench/revO10/MATERIAL_OPTIONS.zh-CN.md

# O10 材料选择澄清：哪些可以改成打印件

2026-09-26。结论：金属是当前基准小样的选材，不是人偶所有相关零件的硬性要求。尤其是铝底座，尚未证明它必须用铝。本页为替代路线评估，没有改动已验证的 O10 几何，也没有将材料候选判为实物合格。

## 为什么上一版用了金属

铝底座用于提供较稳定的试验支撑；薄钢片用于形成可记录的摩擦接触面、承接局部压力；垫圈、螺钉和碟簧分别负责传力、紧固和提供弹力。它们解决的问题不同，不能统一成“金属才够强”。

对打印材料要分别看：

- 强度：会不会断裂或压坏。
- 刚度：受力后会弯曲、压缩多少，是否改变测量位置。
- 蠕变与松弛：持续夹紧时，尺寸和夹紧力是否随时间改变。
- 摩擦与磨损：摆动阻力、起动阻力、停留漂移是否稳定。

拉伸强度或耐热温度较高，并不证明薄垫片能长期保持夹紧力。厂家也将刚度和蠕变作为不同的选材指标。[Formlabs 机械性能说明](https://formlabs.com/blog/choosing-prototyping-material-mechanical-properties/)

静态采集放宽了通信时序，却没有消除关节承重与夹紧要求。姿势需要保持一段时间，反而必须检查随时间发生的变化。保留金属片也不会消除现有 PA12 长臂或叉架自身的蠕变。

## 当前载荷的量级

从 plan.json 取目录点 210 N，约相当于 21.4 kg 重物的重力。它是局部夹紧力的参考值，不是人偶重量，也不是实测预紧力；两片相同碟簧反向串联不会将它翻倍。

小样 PA12 接触环外半径 6 mm、孔半径 2.15 mm，面积约 98.58 mm²。仅按均布载荷计算，210 N / 面积约为 2.13 MPa。9×4.3 垫圈的完整环面积约 49.10 mm²，类似平均值约为 4.28 MPa。真实弹簧边缘和螺钉头的接触面积更小，不能把这些平均值当作峰值应力，也不能直接与材料拉伸强度比较后宣布通过。

这些数值不证明“塑料承受不了”；它们说明需要确认局部支承、实际打印方向、变形及长期夹紧表现。

## 各零件的替代判断

| 对象 | 能否研究打印替代 | 合理的下一步 |
|---|---|---|
| 试验底座主体、固定夹具 | 可以，优先研究 | 改为加厚、带加强筋的打印结构，用标准金属承压件分散局部载荷；必要时重新安排夹紧力传递路径。尚未完成新几何与变形检查，不是原 STL 任意换料即合格 |
| 人偶外壳、线夹、板架 | 可以优先使用打印件 | 按实际紧固、刚度及电子器件空间设计；材料不需要一律升级到最高等级 |
| 关节叉架、承力环等主体 | 可以研究，但比台架底座更受空间限制 | 叉架已经以 PA12 为候选。将金属环改成塑料时，要增加截面或改变螺纹/轴的支承；必须重查动作避让，不能把台架可放大的结论直接套到肩部 |
| 0.5 mm 钢接触片 | 塑料摩擦副在原理上可行，但不宜原厚度直接代换 | 重新设计厚度、承压和材料配对，再测保持力、起动阻力、磨损与漂移。这是另一种摩擦方案，不能继承 PA12—钢的试验结果 |
| 0.3 / 0.8 mm 承压垫圈 | 当前优先保留成品金属件 | 若希望避免定制 0.3 mm 薄片，更合理的优先项是为可购标准钢垫圈调整堆叠，不是打印同厚度的塑料垫圈 |
| A8 碟簧、M4 螺钉和螺母 | 当前保留金属标准件 | 打印柔性弹簧或螺纹需要重新设计尺寸、力—位移和长期可靠性；没有理由将现有金属件的额定值转给同形塑料件 |

打印底座后，仍需单独记录其挠曲或松动，不能把夹具变化全记成关节摩擦面滑移。如果打印主体需要金属承压嵌件，它仍然是混合结构；目标是减少定制加工，不是声称全塑料已经可行。

## 可打印材料候选

| 候选 | 拟研究的用途 | 主要限制 |
|---|---|---|
| MJF PA12 | 现有长臂、叉架，以及加厚后的夹具主体 | 已有中国打印服务渠道；局部承压、刚度和蠕变仍要检查。不能与别的尼龙工艺混为同一批试验 |
| Polymaker Fiberon PET-CF17 | FDM 打印的底座主体、支架和刚性夹具 | 碳纤维增强 PET，厂家列出打印试样性能及夹具用途；需要耐磨喷嘴、适合的打印温度，并处理退火/尺寸变化。不是 PETG-CF；试样数据不等于本零件的验收 |
| 拓竹 PAHT-CF | FDM 打印的承力支架、夹具候选 | 碳纤维增强尼龙，厂家要求封闭打印机、干燥和合适喷嘴；层间方向与吸湿状态不能忽略。未确认用户打印机兼容性 |
| SLS 玻璃填充 PA12，例如 EOS PA 3200 GF | 外包打印的刚性主体候选 | 厂家列出较高刚度及耐磨用途；仍不能仅凭“填充增强”就批准代替薄钢垫圈 |

资料：[嘉立创 MJF PA12](https://www.jlc-3dp.cn/materialDetail/efe4966ee81f4ddb92039f46689e7596.html)、[Polymaker PET-CF17](https://fiberon.polymaker.com/product/pet-cf17/)、[拓竹 PAHT-CF](https://uk.store.bambulab.com/collections/carbon-fiber/products/paht-cf)、[EOS PA 3200 GF](https://www.eos.info/polymer-solutions/polymer-materials/data-sheets/mds-pa-3200-gf)。本轮没有采购或实物测量。

PLA、PETG 可用于不承受该夹紧载荷的外形样件、走线辅助件等；本轮没有证明它们能直接替代原底座。更高等级的树脂或 PEEK 也不因名称或价格自动合格。

“耐磨”也不等于“能保持姿势”。例如 igus 打印材料有针对低摩擦、自润滑滑动件的产品，它们值得用于轴套等位置，但不应直接当作高保持力摩擦片。[igus 官方材料说明](https://www.igus.com/3d-printing/fdm-filament)

## 设计取向

优先评估“打印主体＋可购金属紧固件/承压件”，减少铝底座和特殊薄片的定制需求。为了沿用材料试验，第一步可保留原摩擦接触材料，只改夹具主体；若连摩擦材料也更换，必须另立试验组合并标识结果。打印夹具本身的变形仍需分辨。

目前能确认的是这些材料具有值得评估的用途，不能确认它们已经满足本项目全部保持力、漂移和寿命要求。后续合格判断应基于具体几何、工艺和试验，而不是“金属一定要用”或“高级塑料一定能替代”。
