fukukawa89/PoseDollLab_Design/Hardware/PoseDoll44/bench/revO20/electronics/central_c1/ORDER_NOTES.zh-CN.md

# C1-U 装配变体

O17使用原C1裸板铜层，但D1不装。BOM与坐标表已删除D1。原ERC/DRC仅属于裸板历史证据，不构成双电源上电验收。

USB只供主控；J7独立5V只供传感器降压电路；正电源分开、GND共地。旧板先拆D1，禁止一边保留D1一边同时接电脑和外部5V。详细接线及检查见根目录POWER_AND_USB.zh-CN.md。

不得写传感器OTP。只做小样，待实物上电、反灌、温升、压降和通信测试通过再决定批量。
