fukukawa89/PoseDollLab_Design/Hardware/PoseDoll44/research/tangible_2014_2016/tbt2014_components.png

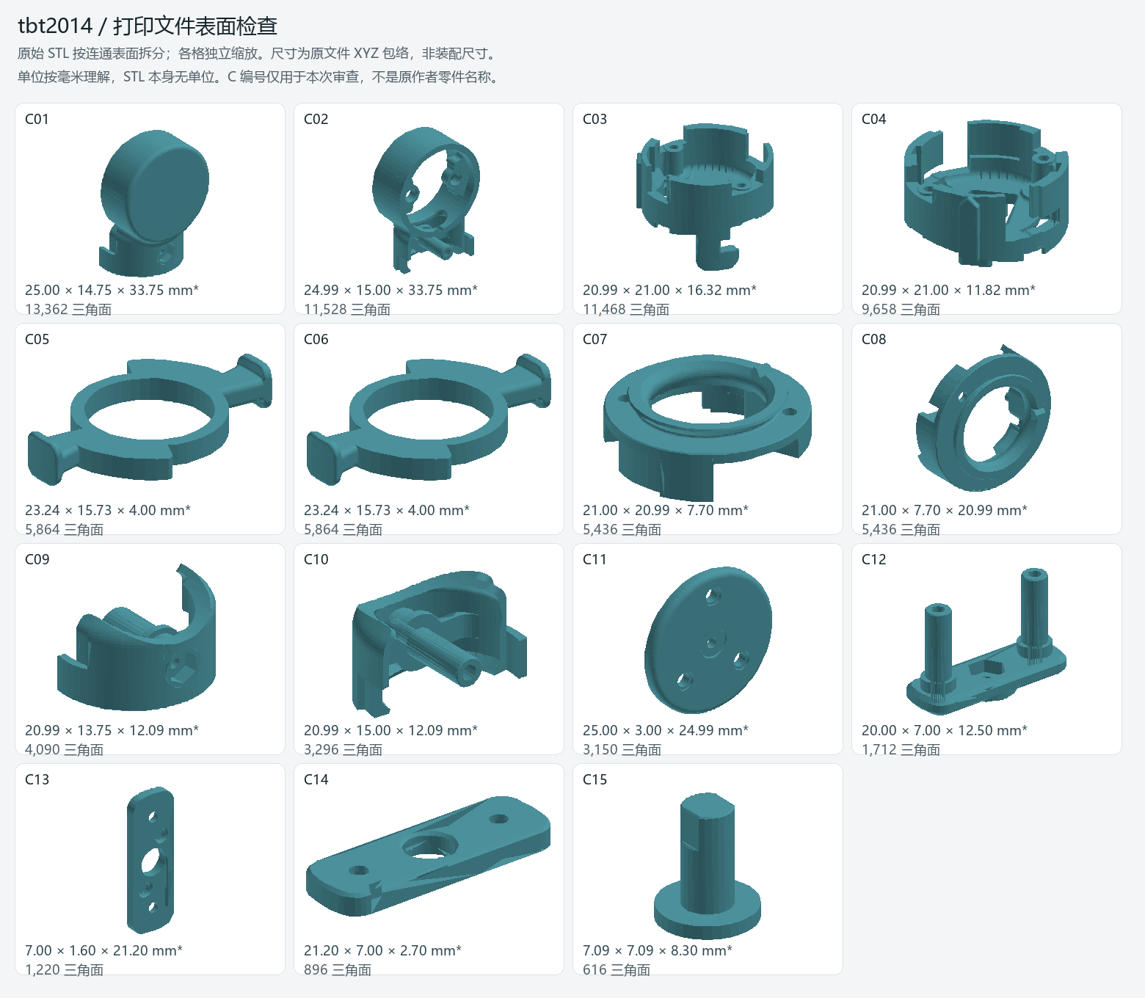
Hardware/PoseDoll44/research/tangible_2014_2016/tbt2014_components.png
