fukukawa89/PoseDollLab_Design/Hardware/PoseDoll44/tutorials/design-lab/parts-guide-desktop.png

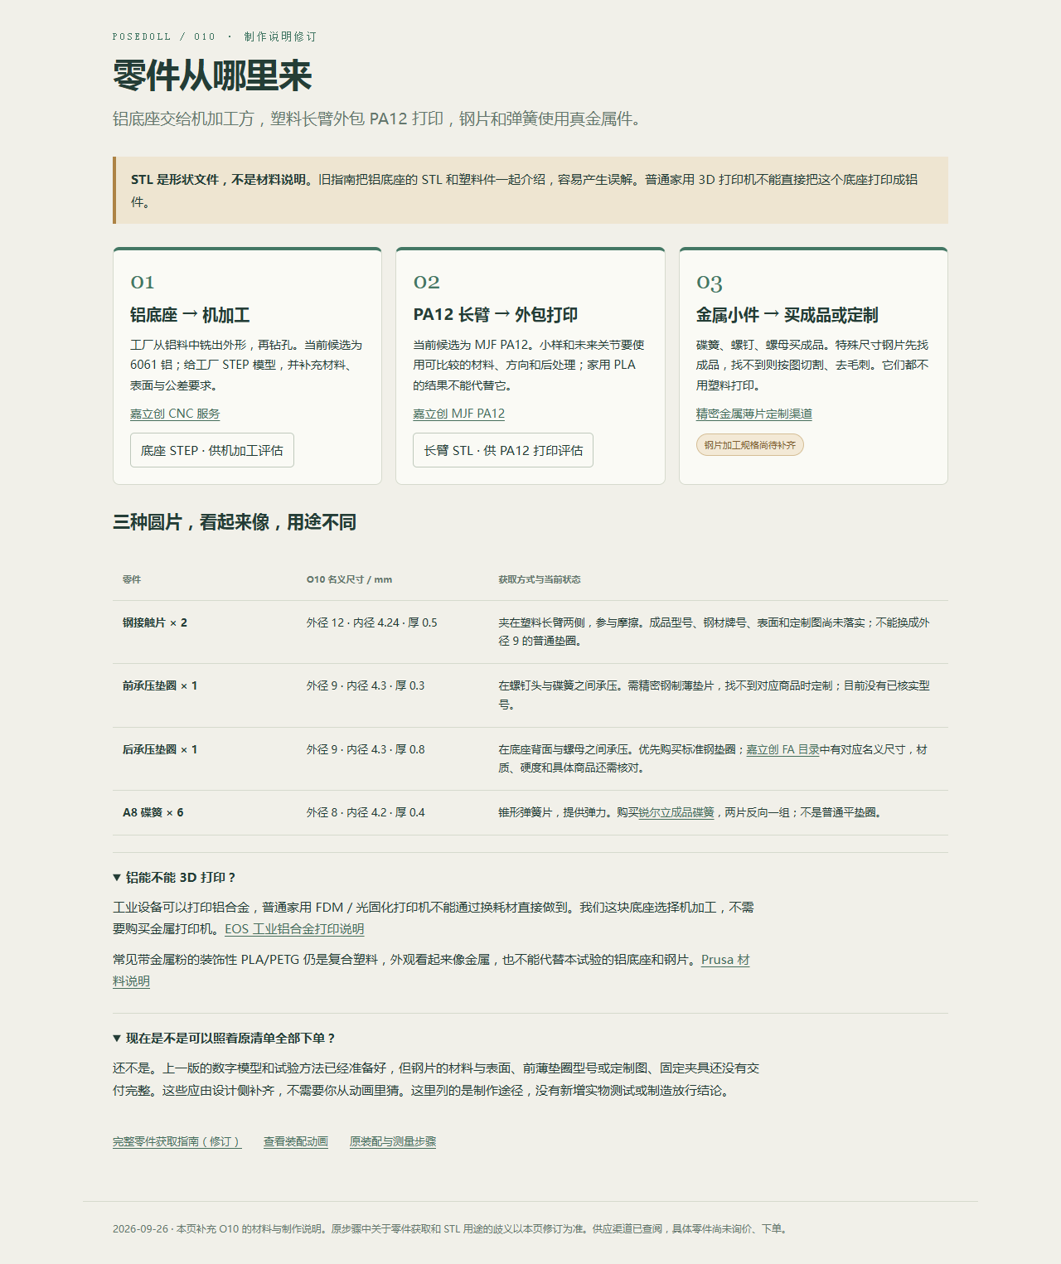
Hardware/PoseDoll44/tutorials/design-lab/parts-guide-desktop.png
