fukukawa89/PoseDollLab_Design/Hardware/PoseDoll44/tutorials/design-lab/parts-guide-mobile.png

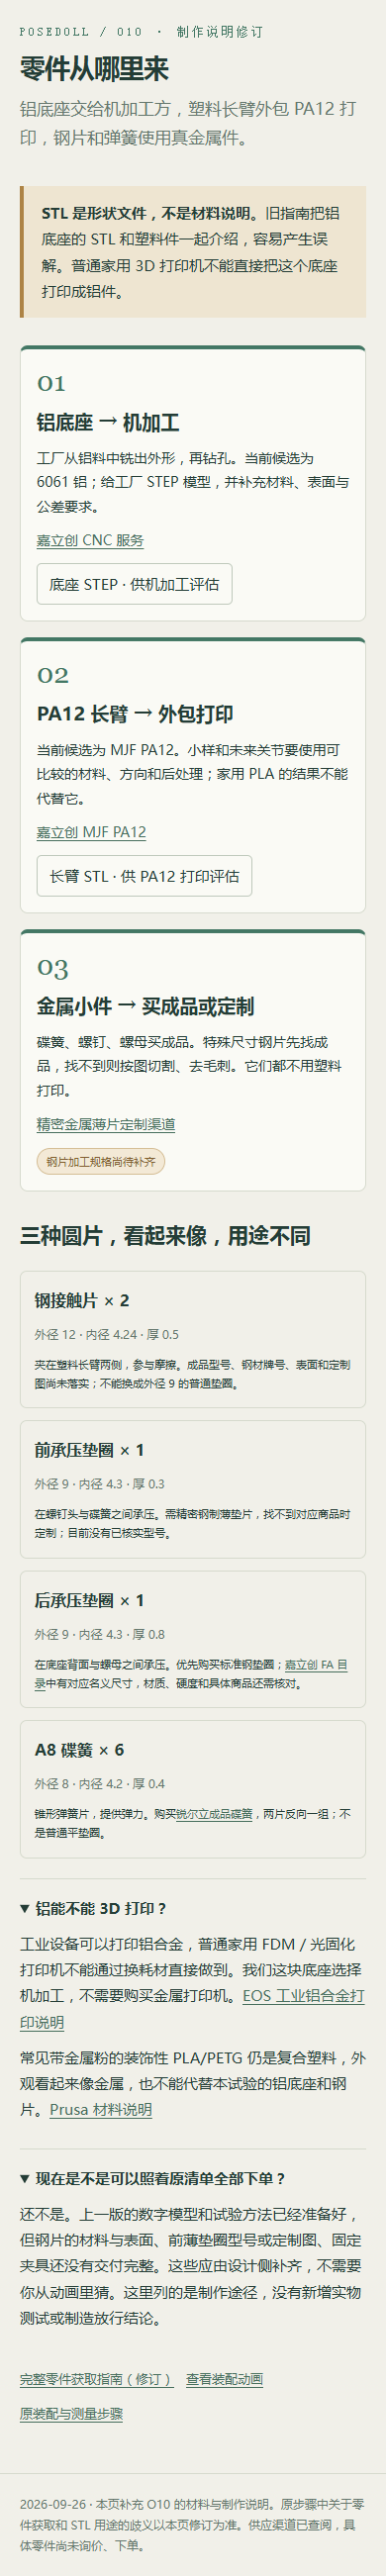
Hardware/PoseDoll44/tutorials/design-lab/parts-guide-mobile.png
