fukukawa89/PoseDollLab_Design/Hardware/PoseDoll44/tutorials/first-bench/verification/desktop-parts.png

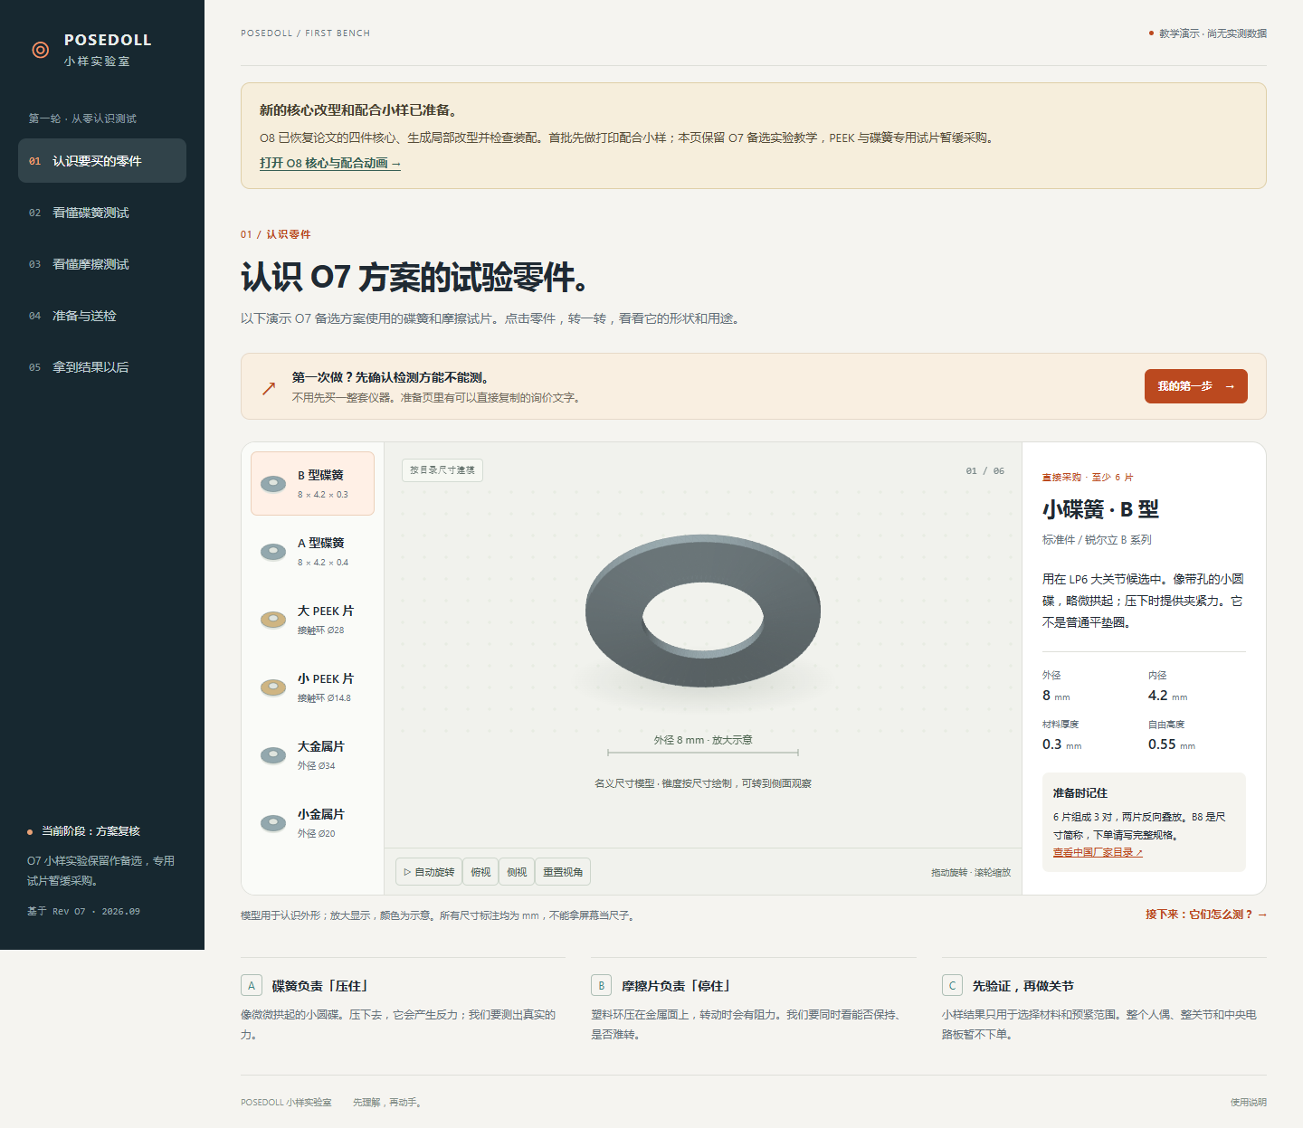
Hardware/PoseDoll44/tutorials/first-bench/verification/desktop-parts.png
