fukukawa89/PoseDollLab_Design/Hardware/PoseDoll44/bench/revO22/a1mini_supports/projects/S00_support_trial_PLA_supports.3mf

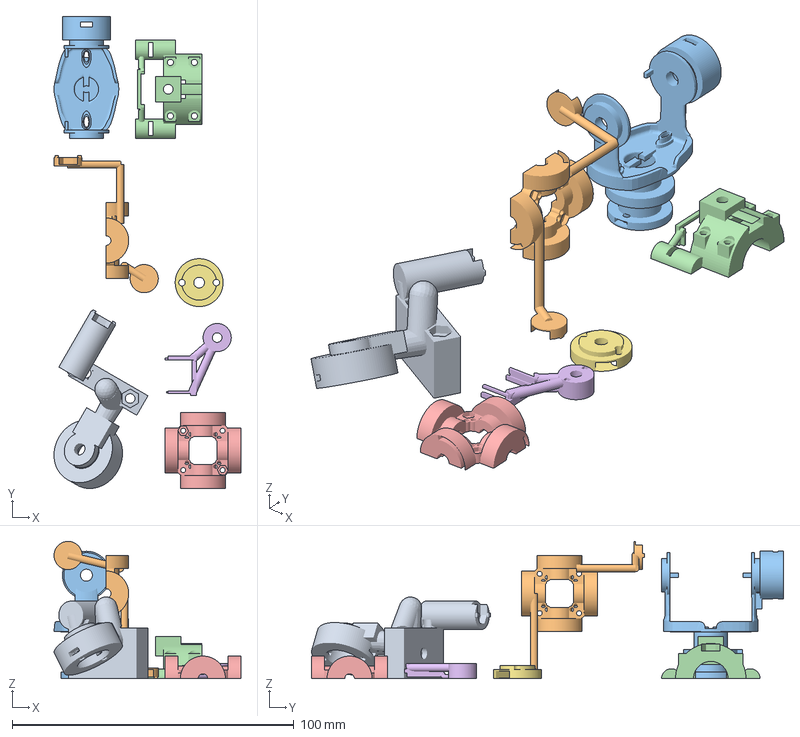
[picture p49: CAD file, 2026-10-04]
Hardware/PoseDoll44/bench/revO22/a1mini_supports/projects/S00_support_trial_PLA_supports.3mf
66.3 x 167.5 x 48.7 mm
S00-01 H004 frame/elbow_l
S00-02 P130 foot_l/C14
S00-03 P033 head/C01
S00-04 X045 head/P_case_plus
S00-05 P036 head/C15
S00-06 X005 head/C01_sensor_cassette
S00-07 N003 head/C01_magnet_cartridge
