fukukawa89/PoseDollLab_Design/Hardware/PoseDoll44/bench/revO22/mechanical/section/R2.stl

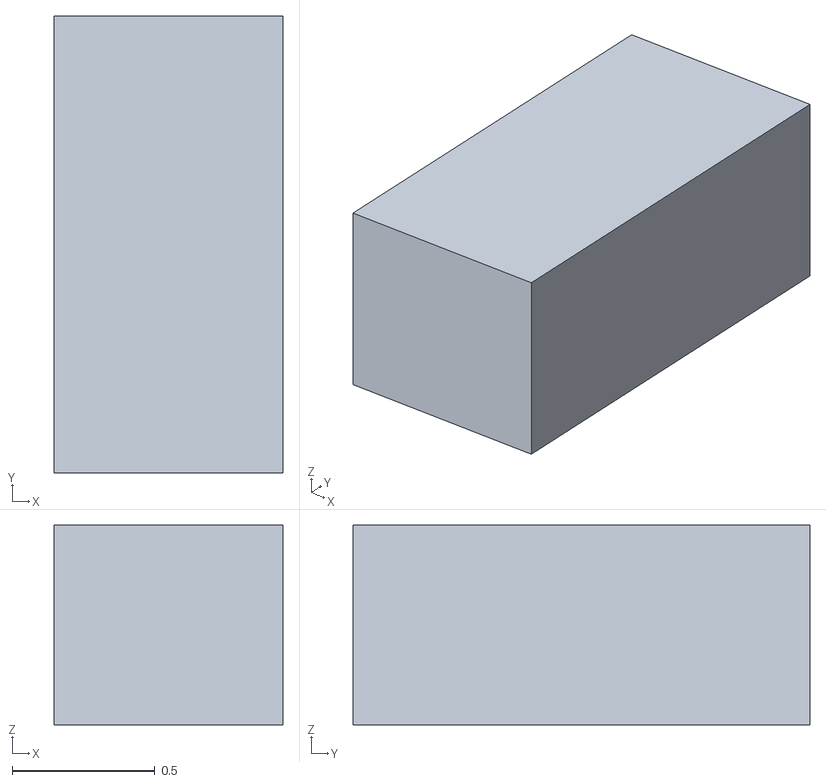
[picture p50: CAD file, 2026-10-01]
Hardware/PoseDoll44/bench/revO22/mechanical/section/R2.stl
0.8 x 1.60 x 0.7
