fukukawa89/PoseDollLab_Design/Hardware/PoseDoll44/bench/revO22/mechanical/stl/frame__head.stl

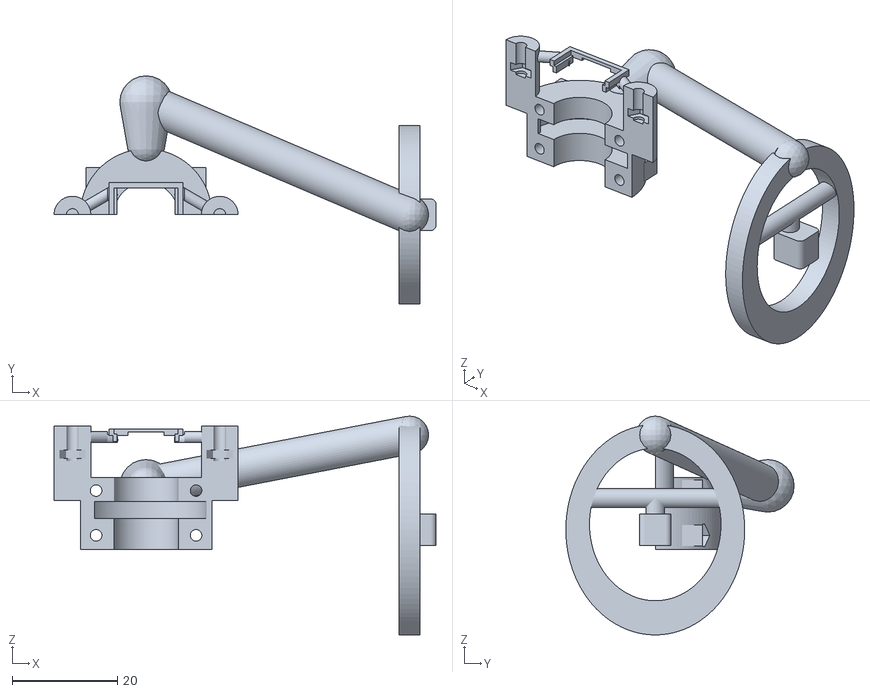
[picture p51: CAD file, 2026-10-01]
Hardware/PoseDoll44/bench/revO22/mechanical/stl/frame__head.stl
72.6 x 43.4 x 41.6
