fukukawa89/PoseDollLab_Design/Hardware/PoseDoll44/bench/revO22/physical_tests/sensor_coupon/sensor_bridge.3mf

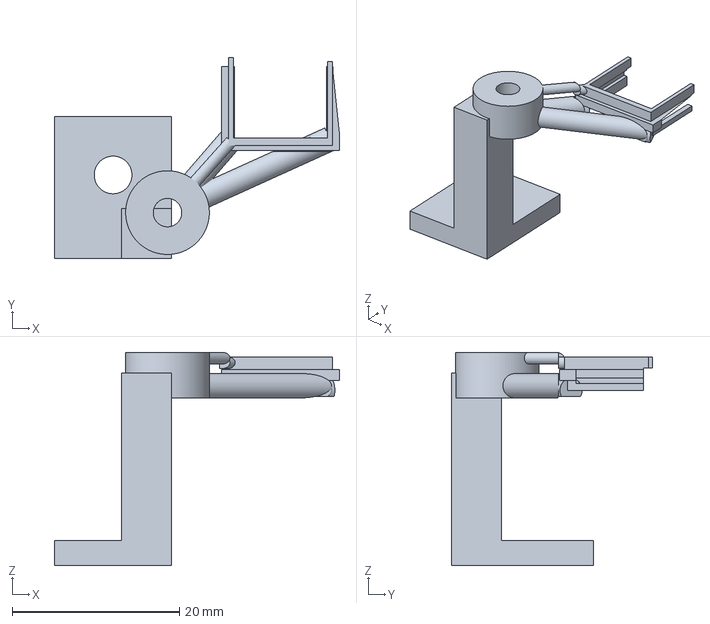
[picture p52: CAD file, 2026-10-01]
Hardware/PoseDoll44/bench/revO22/physical_tests/sensor_coupon/sensor_bridge.3mf
34.0 x 24.0 x 25.5 mm
