fukukawa89/PoseDollLab_Design/Hardware/PoseDoll44/bench/revO7/coupons/M4_PEEK_coupon.step

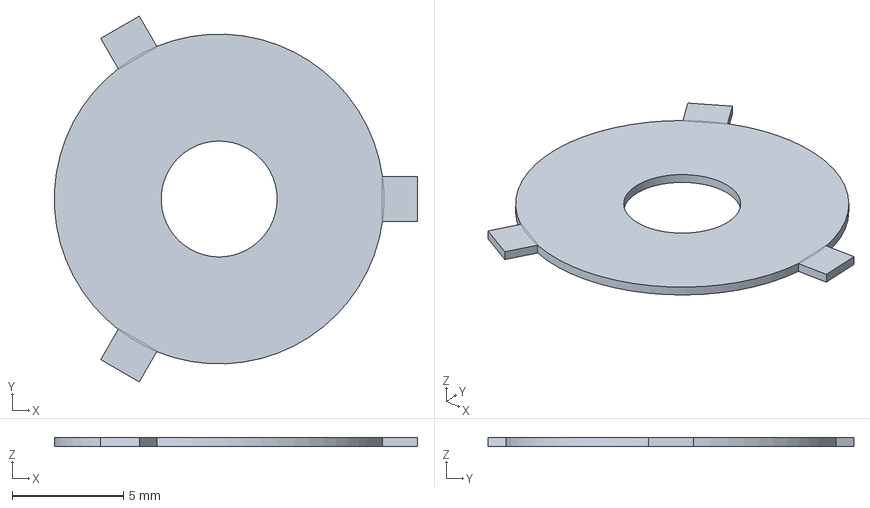
[picture p54: CAD file, 2026-09-30]
Hardware/PoseDoll44/bench/revO7/coupons/M4_PEEK_coupon.step
16.3 x 16.4 x 0.4 mm
