fukukawa89/PoseDollLab_Design/Hardware/PoseDoll44/bench/revO8/fit_gauges/hole_gauge_Y.step

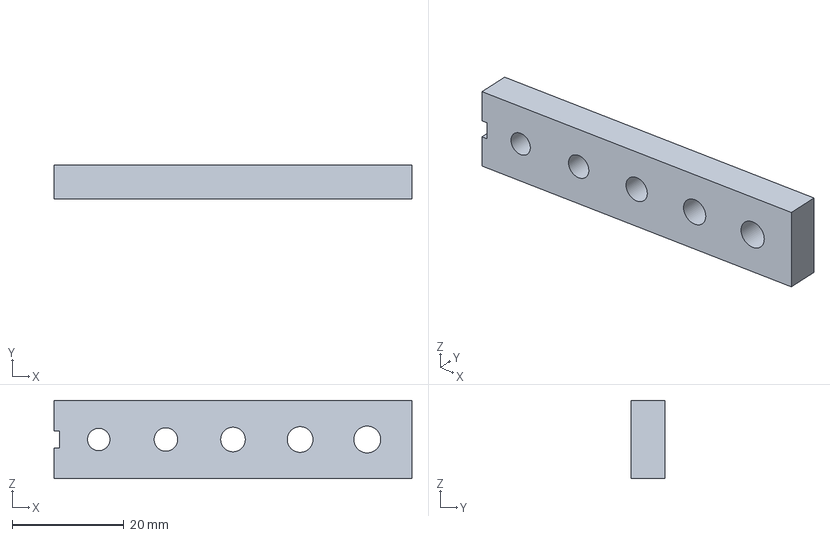
[picture p55: CAD file, 2026-09-30]
Hardware/PoseDoll44/bench/revO8/fit_gauges/hole_gauge_Y.step
64.0 x 6.00 x 14.0 mm
