fukukawa89/PoseDollLab_Design/Hardware/PoseDoll44/bench/service_requests/o12_20260926/models/O12_taobao_bench.3mf

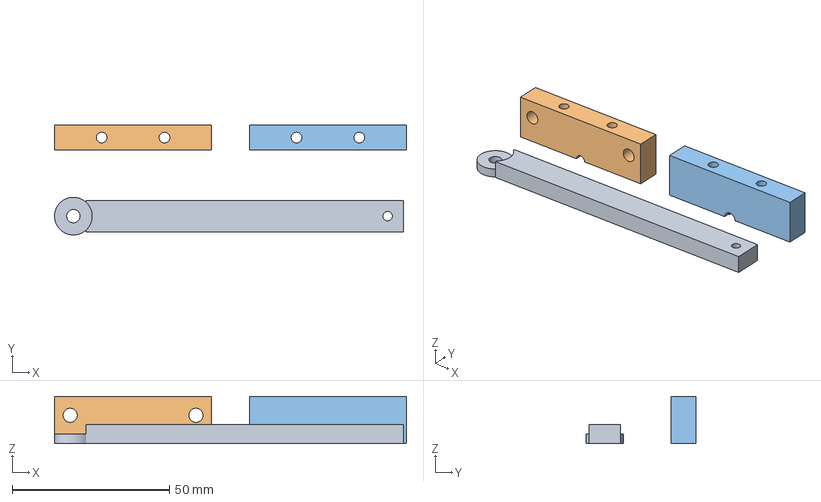
[picture p56: CAD file, 2026-09-30]
Hardware/PoseDoll44/bench/service_requests/o12_20260926/models/O12_taobao_bench.3mf
112.0 x 35.0 x 15.0 mm
printed_lever
printed_base_minus
printed_base_plus
