fukukawa89/PoseDollLab_Design/Hardware/PoseDoll44/generated/revO10/runs/o10_20260926_r1/face_brake/C14.stl

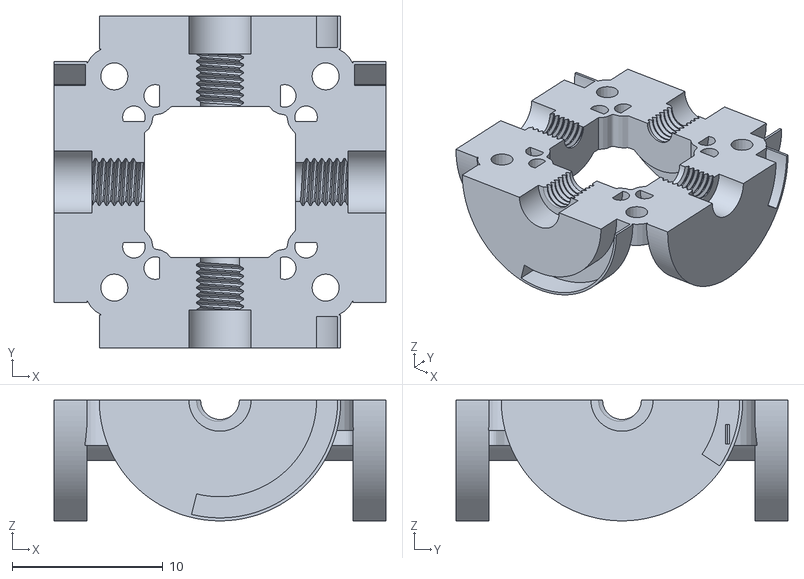
[picture p57: CAD file, 2026-09-30]
Hardware/PoseDoll44/generated/revO10/runs/o10_20260926_r1/face_brake/C14.stl
22.0 x 22.0 x 8.00
