fukukawa89/PoseDollLab_Design/Hardware/PoseDoll44/generated/revO10/runs/o10_20260926_r1/finite_twist/proximal_example_nut1.stl

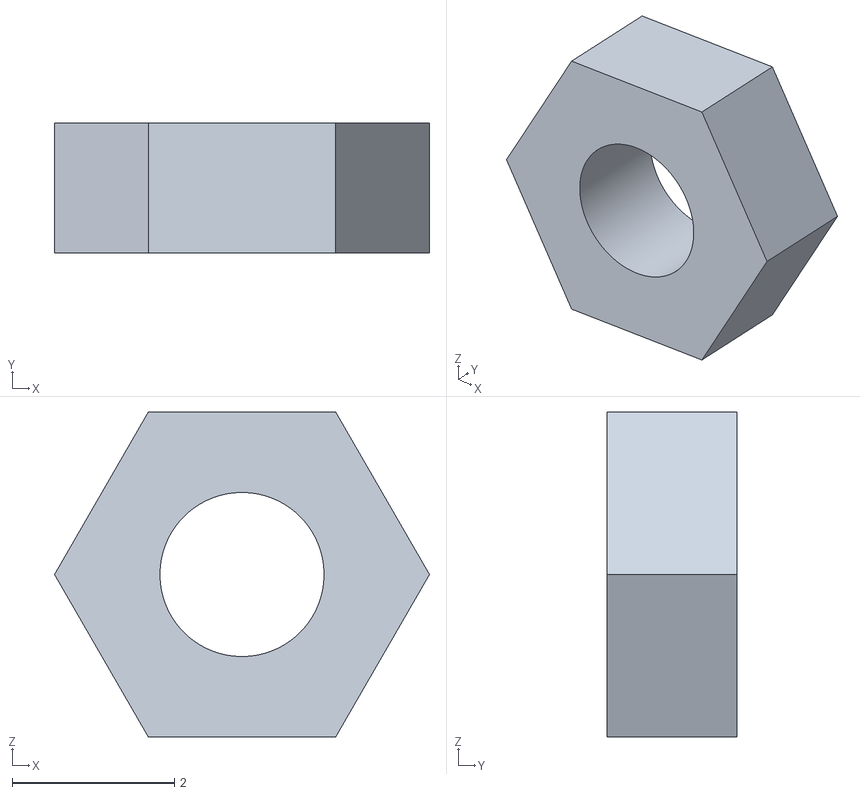
[picture p58: CAD file, 2026-09-30]
Hardware/PoseDoll44/generated/revO10/runs/o10_20260926_r1/finite_twist/proximal_example_nut1.stl
4.62 x 1.60 x 4.00
