fukukawa89/PoseDollLab_Design/Hardware/PoseDoll44/generated/revO10/runs/o10_20260926_r1/internal_stops/C02.stl

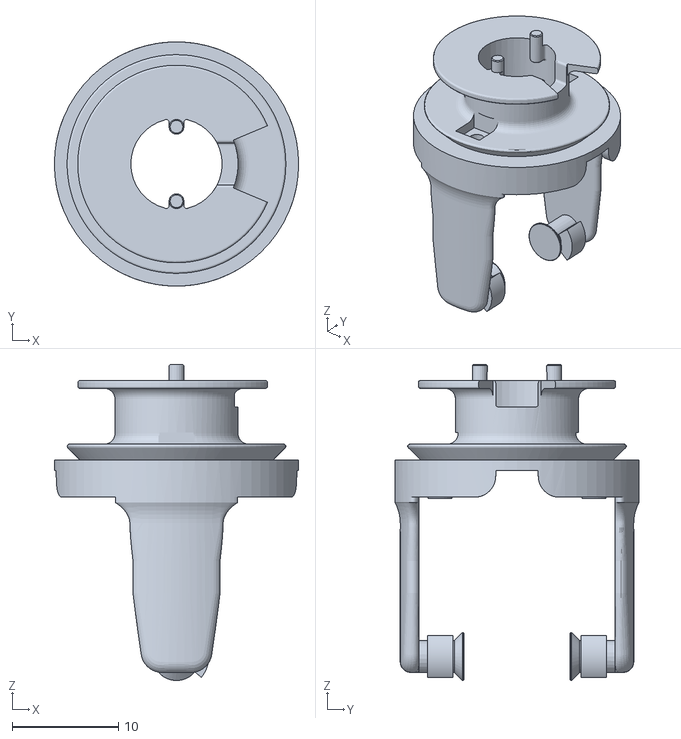
[picture p59: CAD file, 2026-09-30]
Hardware/PoseDoll44/generated/revO10/runs/o10_20260926_r1/internal_stops/C02.stl
23.0 x 23.0 x 29.8
