fukukawa89/PoseDollLab_Design/Hardware/PoseDoll44/generated/revO10/runs/o10_20260926_r1/slipring/catalogue_barrel.stl

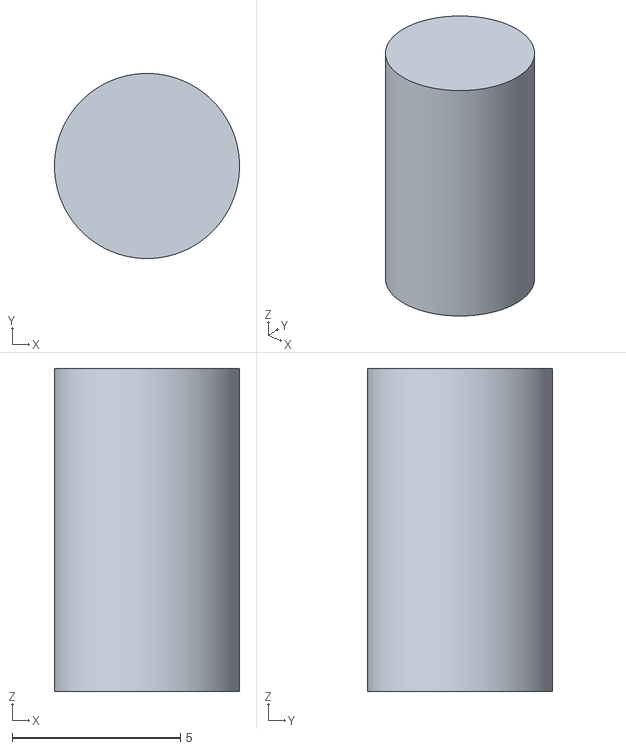
[picture p60: CAD file, 2026-09-30]
Hardware/PoseDoll44/generated/revO10/runs/o10_20260926_r1/slipring/catalogue_barrel.stl
5.50 x 5.50 x 9.60
