fukukawa89/PoseDollLab_Design/Hardware/PoseDoll44/generated/revO5CN/runs/cn_20260924_r1/sensor_installation_trial.step

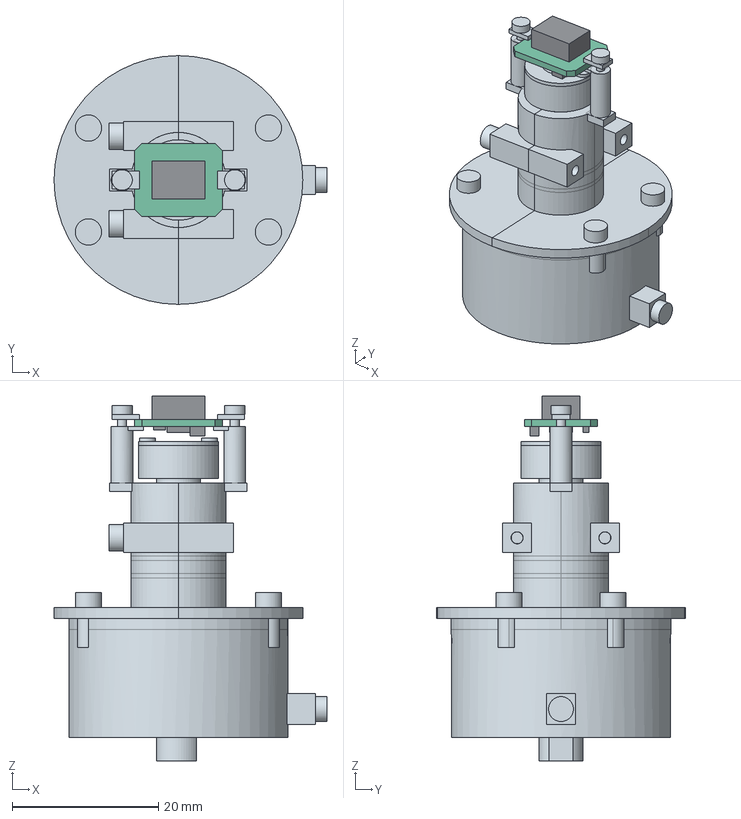
[picture p61: CAD file, 2026-09-30]
Hardware/PoseDoll44/generated/revO5CN/runs/cn_20260924_r1/sensor_installation_trial.step
37.3 x 34.0 x 49.9 mm
one_piece_brake_cup
housing_L
housing_R
cup_mount_0
cup_mount_1
cup_mount_2
cup_mount_3
rear_bush_L
rear_bush_R
front_bush_L
front_bush_R
thrust_rear_L
thrust_rear_R
thrust_front_L
thrust_front_R
measurement_shaft
floating_brake_disc
front_lining_backing
rear_lining_backing
front_friction_lining
rear_friction_lining
keyed_pressure_plate
spring_front_washer
disc_spring_1
disc_spring_2
disc_spring_3
disc_spring_4
spring_rear_washer
threaded_adjuster_cap
cap_lock_dog_screw
bearing_clamp_-6
bearing_clamp_6
diametric_magnet
magnet_keeper
keeper_screw_-4.25
keeper_screw_4.25
pcb_edge_clamp_-7.7
pcb_clamp_screw_-7.7
pcb_edge_clamp_7.7
pcb_clamp_screw_7.7
PCB_CN1_1mm
MT6701QT_max_body
CJT_header_max_body
C1_body
C2_body
R1_body
R2_body
