fukukawa89/PoseDollLab_Design/Hardware/PoseDoll44/generated/revO6/runs/o6_20260924_r1/joint_L6_validated/rear_friction_lining.step

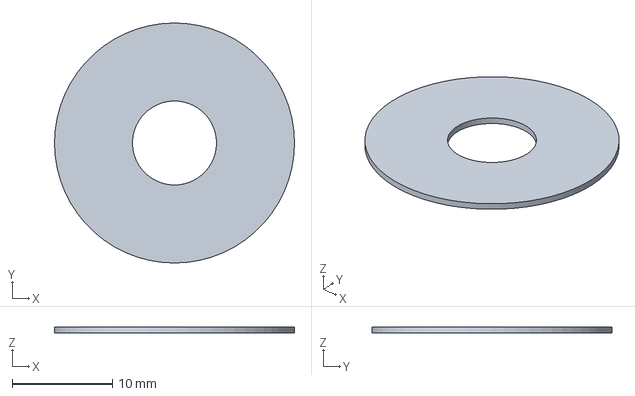
[picture p62: CAD file, 2026-09-30]
Hardware/PoseDoll44/generated/revO6/runs/o6_20260924_r1/joint_L6_validated/rear_friction_lining.step
24.0 x 24.0 x 0.6 mm
