fukukawa89/PoseDollLab_Design/Hardware/PoseDoll44/generated/revO7/runs/o7_20260924_r1/LP6_current/pcb_edge_clamp_-7.7.step

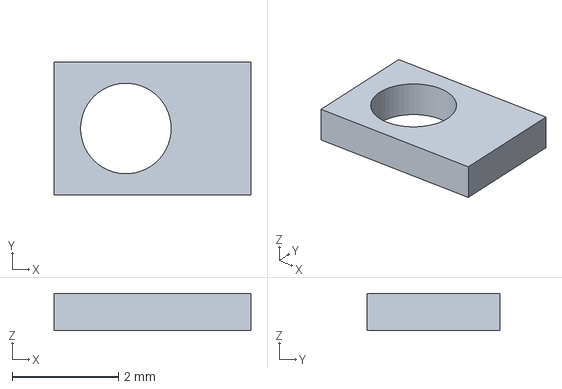
[picture p63: CAD file, 2026-09-30]
Hardware/PoseDoll44/generated/revO7/runs/o7_20260924_r1/LP6_current/pcb_edge_clamp_-7.7.step
3.70 x 2.50 x 0.7 mm
