fukukawa89/PoseDollLab_Design/Hardware/PoseDoll44/generated/revO8/runs/o8_20260925_r1/fork_extension_0mm/C14.stl

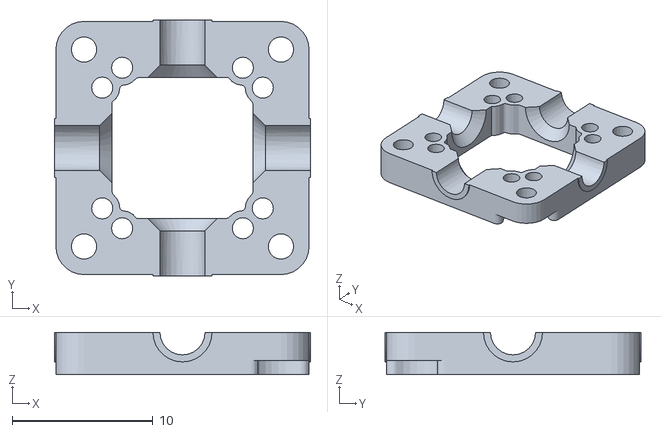
[picture p64: CAD file, 2026-09-30]
Hardware/PoseDoll44/generated/revO8/runs/o8_20260925_r1/fork_extension_0mm/C14.stl
18.2 x 18.2 x 3.00
