fukukawa89/PoseDollLab_Design/Hardware/PoseDoll44/generated/revO9/runs/o9_20260926_r1/cup_relief_L2_R0p35/C02.stl

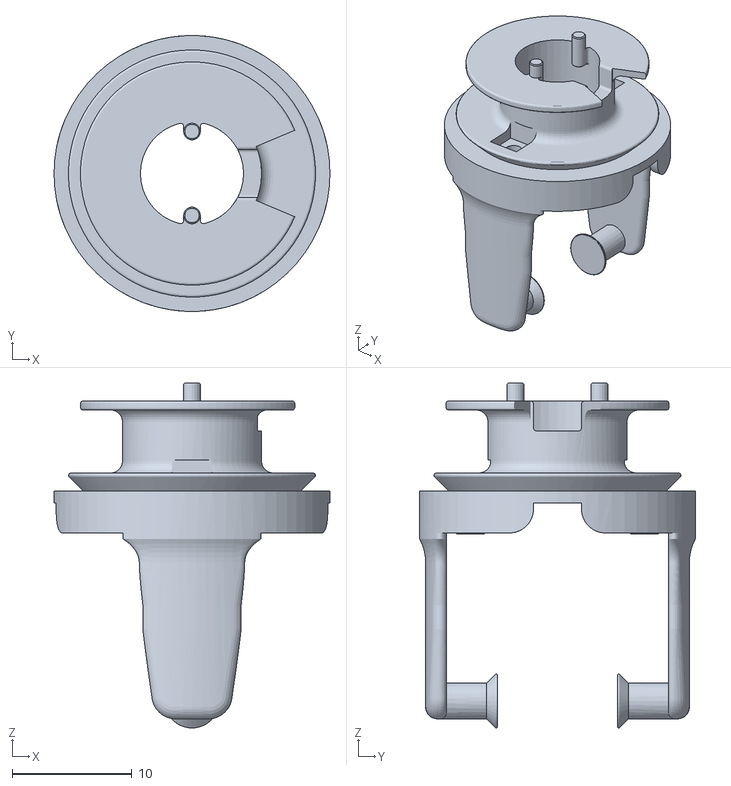
[picture p66: CAD file, 2026-09-30]
Hardware/PoseDoll44/generated/revO9/runs/o9_20260926_r1/cup_relief_L2_R0p35/C02.stl
23.0 x 23.0 x 28.8
