fukukawa89/PoseDollLab_Design/Hardware/PoseDoll44/references/revO15/seeed_xiao/dimensions_v11.dxf

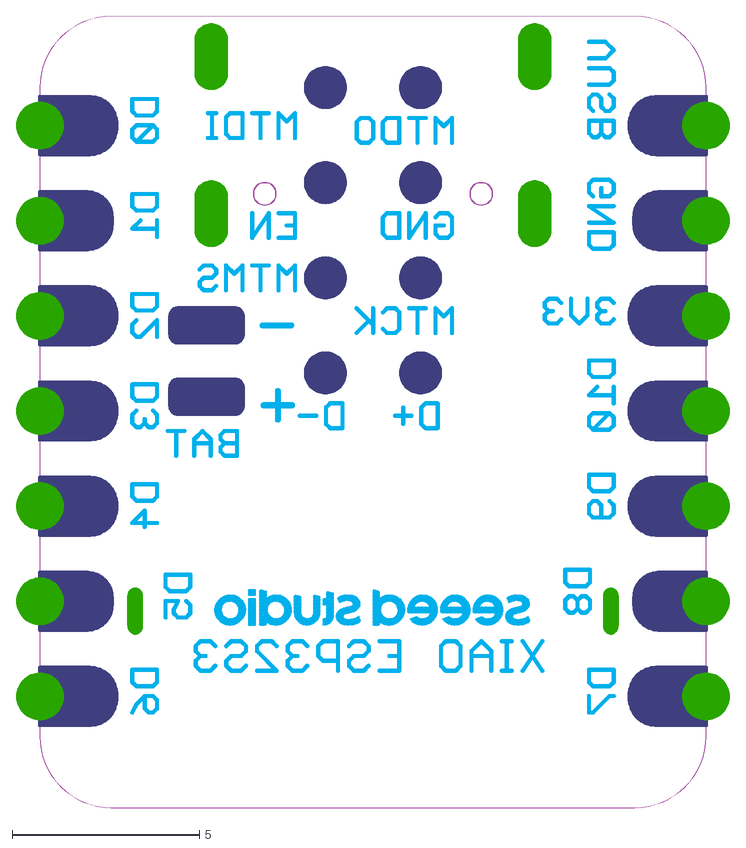
[picture p67: CAD file, 2026-09-30]
Hardware/PoseDoll44/references/revO15/seeed_xiao/dimensions_v11.dxf
19.0 x 21.1
