fukukawa89/PoseDollLab_Design/Hardware/PoseDoll44/tutorials/tut-prototype/assets/o8-fit-handoff/B_core_reference/C01.stl

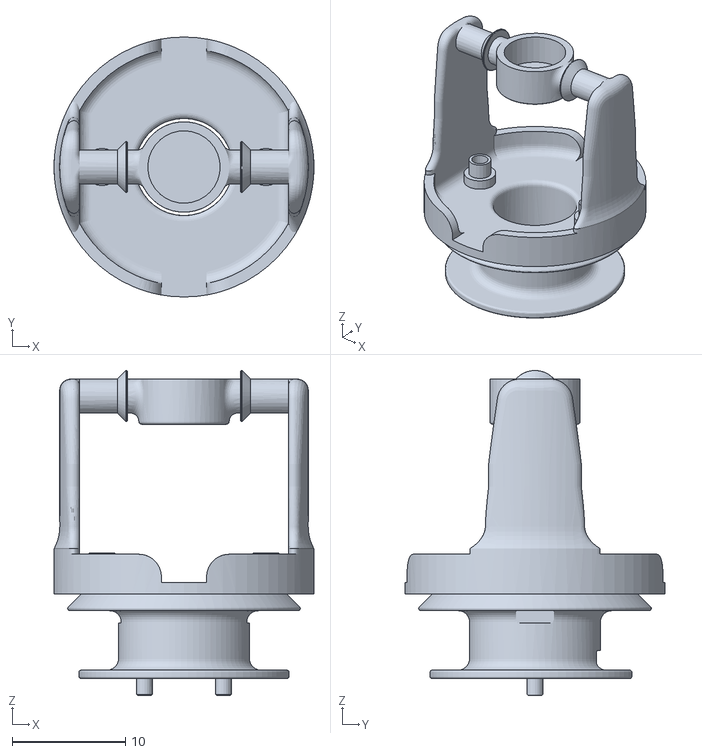
[picture p68: CAD file, 2026-09-30]
Hardware/PoseDoll44/tutorials/tut-prototype/assets/o8-fit-handoff/B_core_reference/C01.stl
23.0 x 23.0 x 28.8
