fukukawa89/PoseDollLab_Design/Hardware/PoseDoll44/verification/revO6/runs/o6_20260924_r1/arm_candidate/manny_left_nine_axis_positioned.step

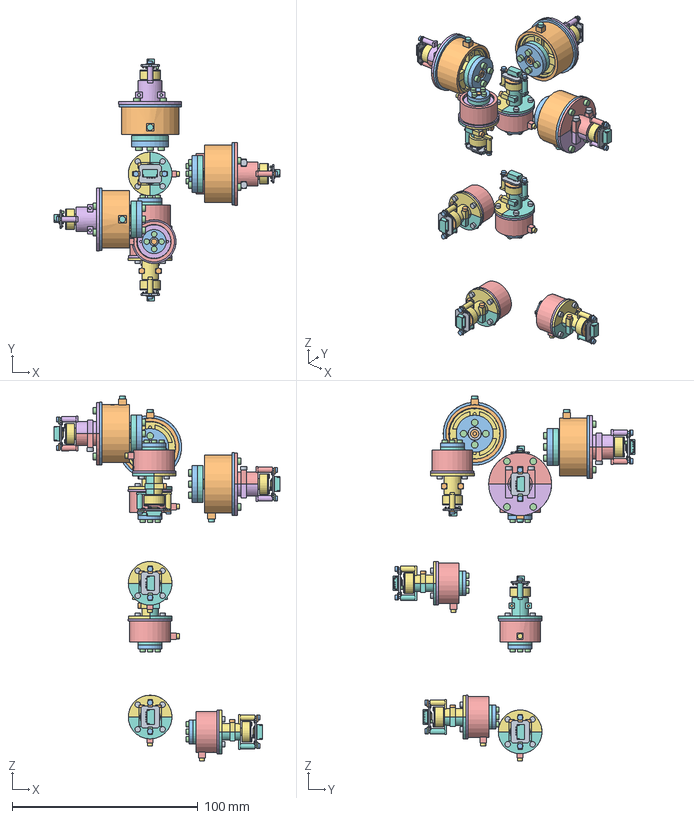
[picture p69: CAD file, 2026-09-30]
Hardware/PoseDoll44/verification/revO6/runs/o6_20260924_r1/arm_candidate/manny_left_nine_axis_positioned.step
121.5 x 130.3 x 196.6 mm
