fukukawa89/PoseDollLab_Design/Hardware/PoseDoll44/verification/revO6/runs/o6_20260924_r1/service/M4_hollow_pin_spanner.step

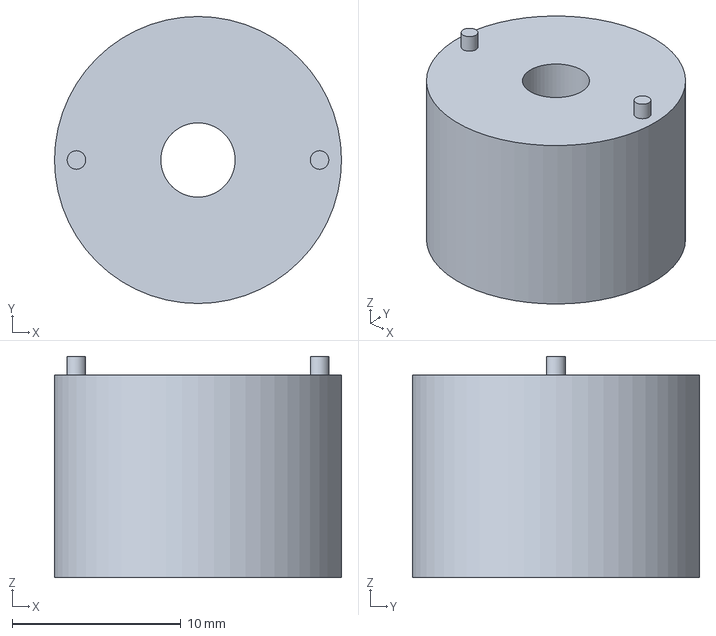
[picture p71: CAD file, 2026-09-30]
Hardware/PoseDoll44/verification/revO6/runs/o6_20260924_r1/service/M4_hollow_pin_spanner.step
17.0 x 17.0 x 13.1 mm
