fukukawa89/PoseDollLab_Design/Hardware/PoseDoll44/bench/revO11/printed_base_plus.stl

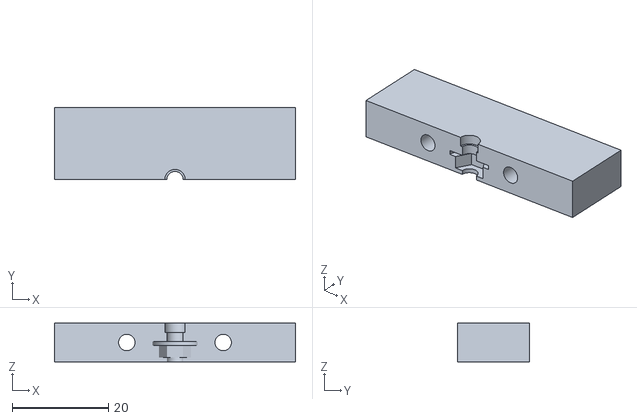
[picture p72: CAD file, 2026-09-30]
Hardware/PoseDoll44/bench/revO11/printed_base_plus.stl
50.0 x 15.0 x 8.00
