fukukawa89/PoseDollLab_Design/Hardware/PoseDoll44/bench/revO13/print_beds/C01_on_bed.stl

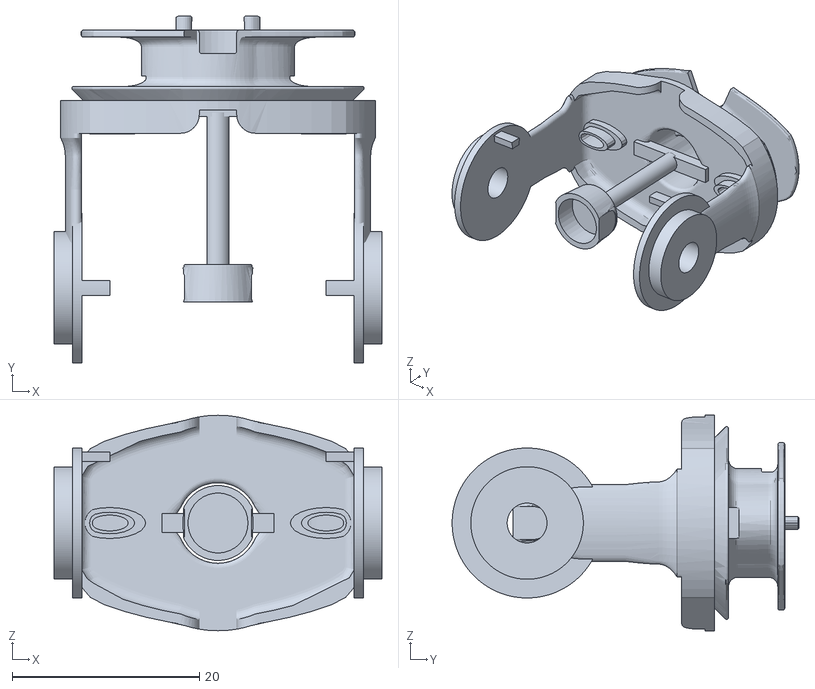
[picture p73: CAD file, 2026-09-30]
Hardware/PoseDoll44/bench/revO13/print_beds/C01_on_bed.stl
35.0 x 37.0 x 23.0
