fukukawa89/PoseDollLab_Design/Hardware/PoseDoll44/bench/revO14/print_beds/C02_flat_face.stl

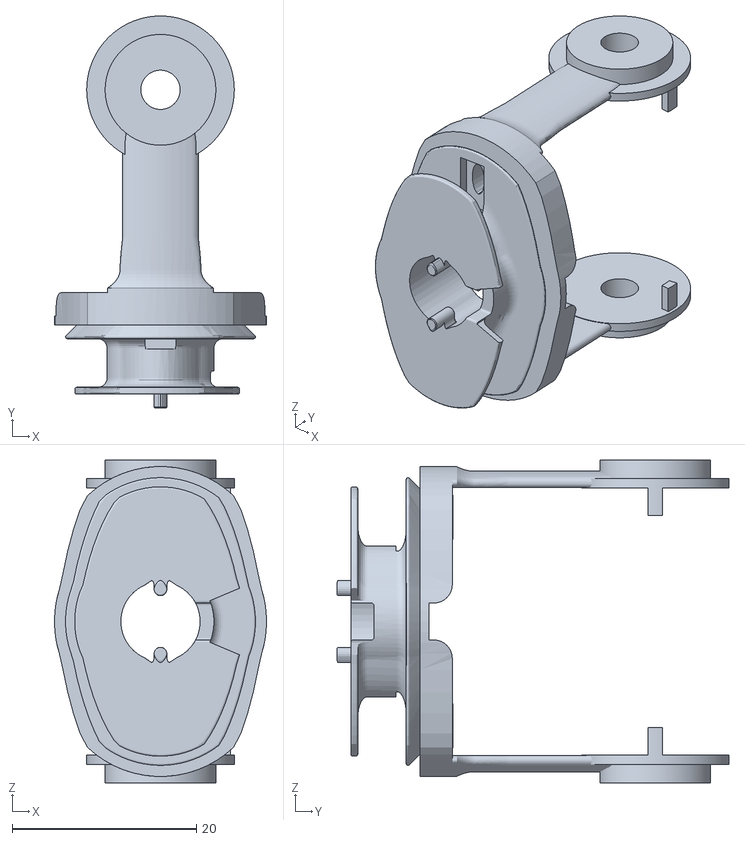
[picture p74: CAD file, 2026-09-30]
Hardware/PoseDoll44/bench/revO14/print_beds/C02_flat_face.stl
23.0 x 42.5 x 35.0
