fukukawa89/PoseDollLab_Design/Hardware/PoseDoll44/bench/revO15/print_batch/P219.3mf

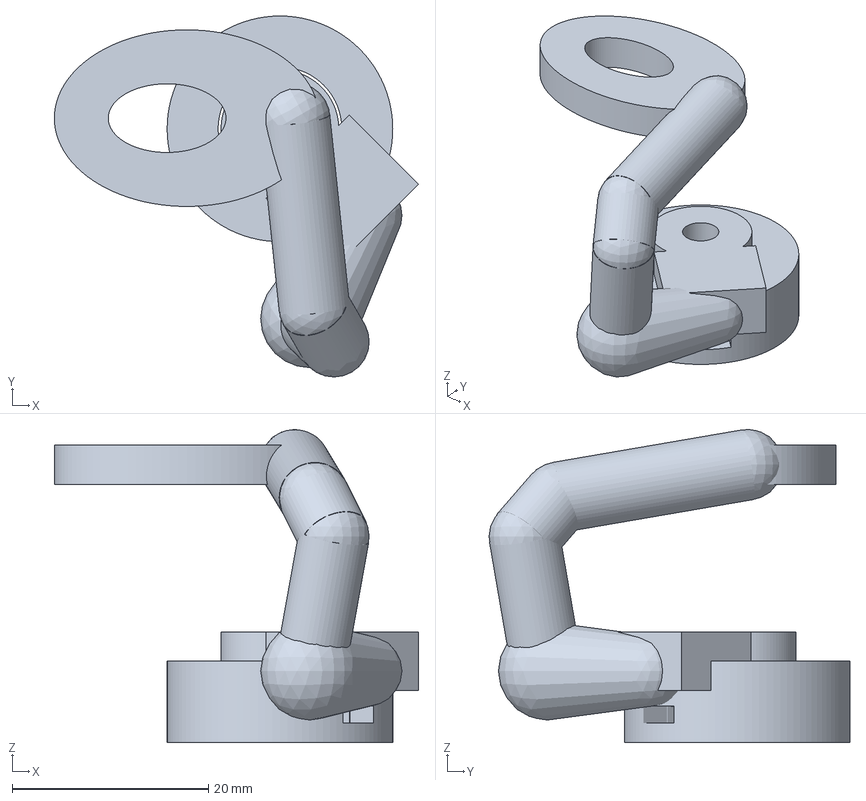
[picture p75: CAD file, 2026-09-30]
Hardware/PoseDoll44/bench/revO15/print_batch/P219.3mf
37.1 x 36.8 x 31.9 mm
