fukukawa89/PoseDollLab_Design/Hardware/PoseDoll44/bench/revO16/print_batch/P165.3mf

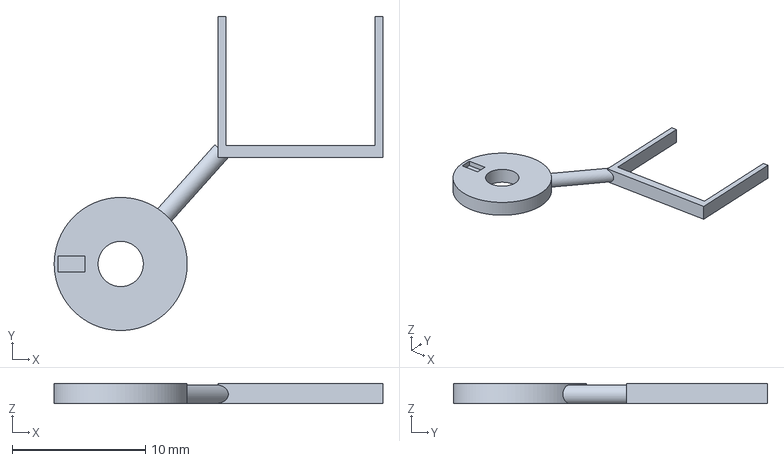
[picture p76: CAD file, 2026-09-30]
Hardware/PoseDoll44/bench/revO16/print_batch/P165.3mf
24.7 x 23.6 x 1.50 mm
