fukukawa89/PoseDollLab_Design/Hardware/PoseDoll44/bench/revO17/print_batch/P142.3mf

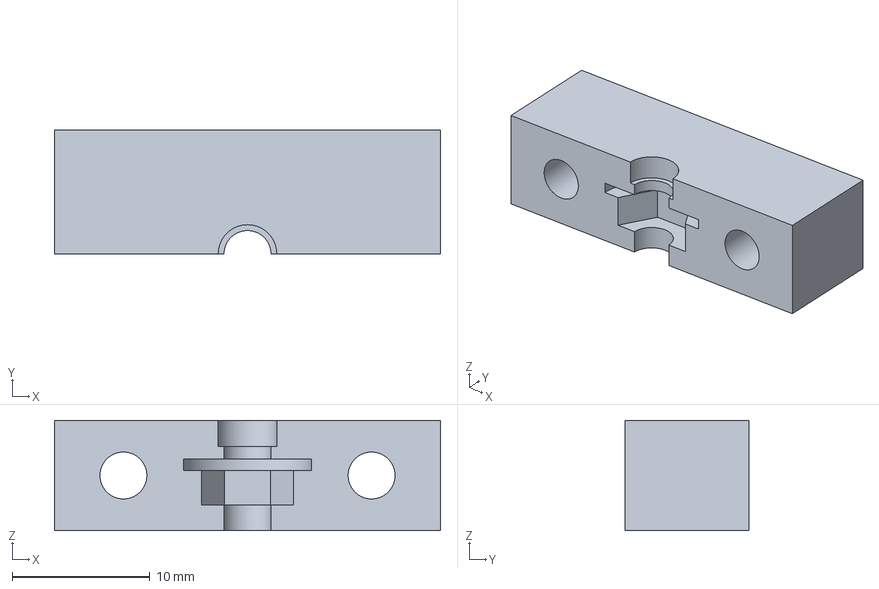
[picture p77: CAD file, 2026-09-30]
Hardware/PoseDoll44/bench/revO17/print_batch/P142.3mf
28.0 x 9.00 x 8.00 mm
