fukukawa89/PoseDollLab_Design/Hardware/PoseDoll44/bench/revO18/coupon/Q001.3mf

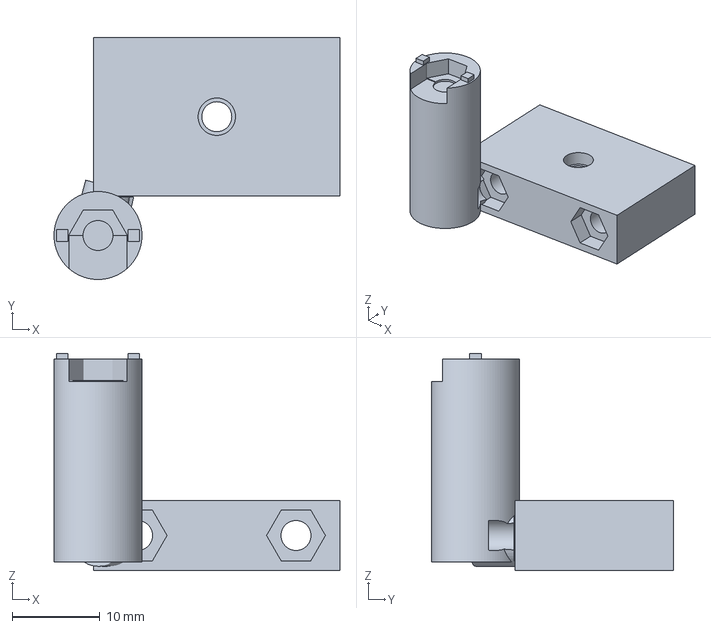
[picture p78: CAD file, 2026-09-30]
Hardware/PoseDoll44/bench/revO18/coupon/Q001.3mf
32.5 x 27.5 x 24.7 mm
