fukukawa89/PoseDollLab_Design/Hardware/PoseDoll44/bench/revO18/print_batch/H013.3mf

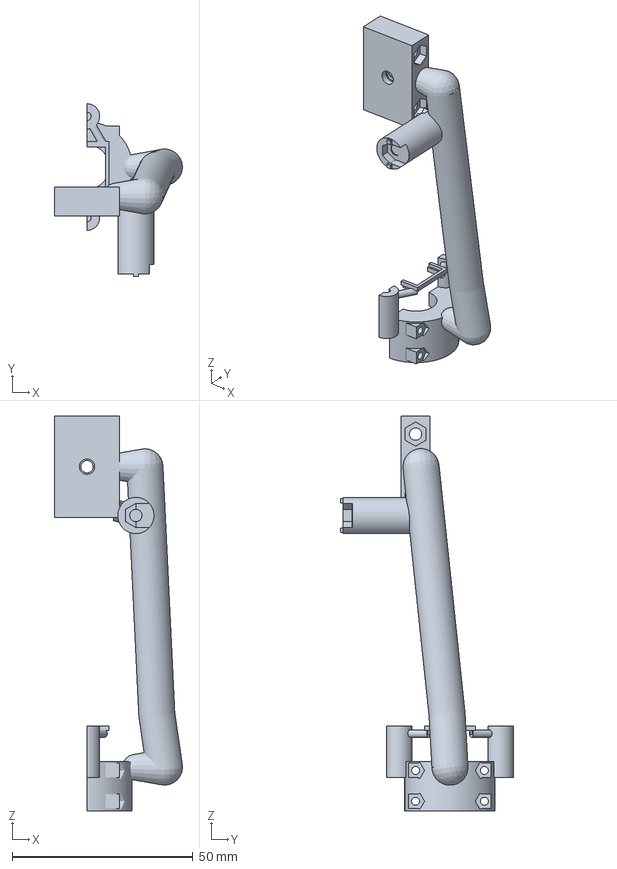
[picture p79: CAD file, 2026-09-30]
Hardware/PoseDoll44/bench/revO18/print_batch/H013.3mf
35.4 x 47.7 x 109.2 mm
