fukukawa89/PoseDollLab_Design/Hardware/PoseDoll44/bench/revO20/print_batch/W015.3mf

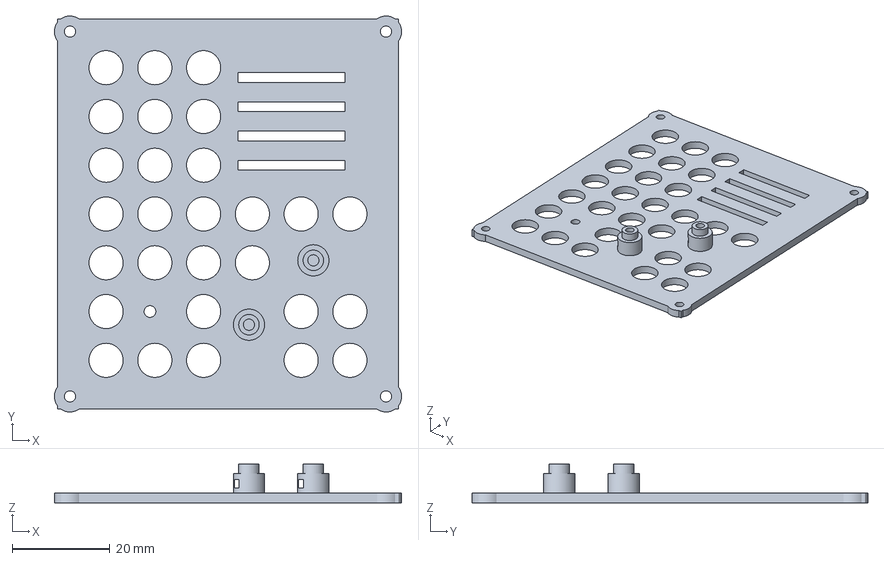
[picture p80: CAD file, 2026-09-30]
Hardware/PoseDoll44/bench/revO20/print_batch/W015.3mf
71.2 x 81.2 x 7.98 mm
