fukukawa89/PoseDollLab_Design/Hardware/PoseDoll44/bench/revO22/a1mini/plates/A09_right_leg.3mf

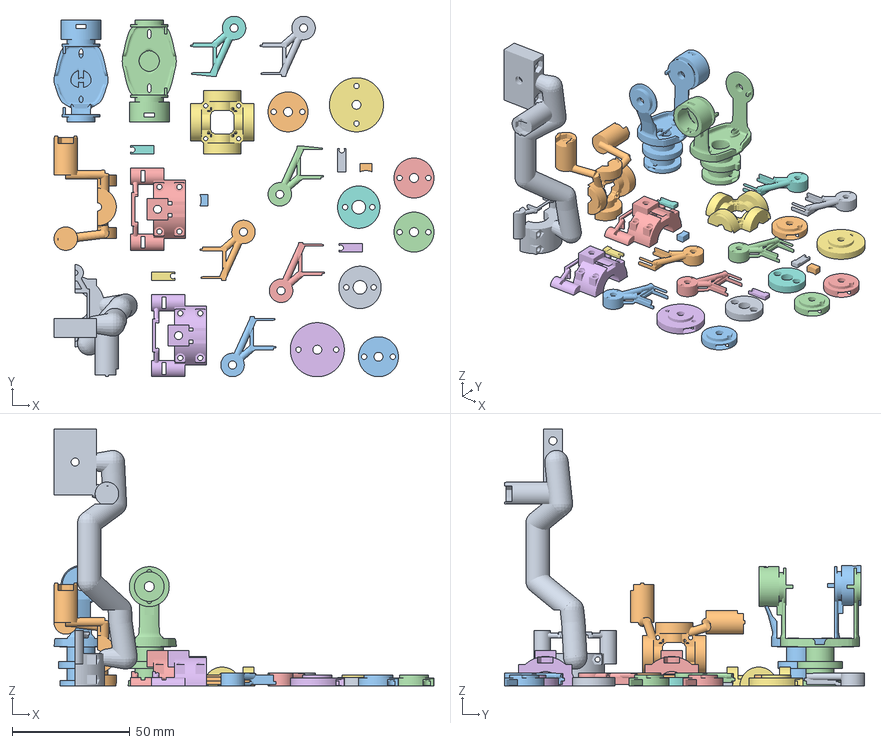
[picture p81: CAD file, 2026-10-01]
Hardware/PoseDoll44/bench/revO22/a1mini/plates/A09_right_leg.3mf
161.6 x 153.3 x 109.2 mm
A09-01 X080 frame/thigh_r
A09-02 P117 thigh_r/C14
A09-03 P115 thigh_r/C01
A09-04 P116 thigh_r/C02
A09-05 X076 thigh_r/P_case_plus
A09-06 X079 thigh_r/D_case_plus
A09-07 P118 thigh_r/C15
A09-08 X013 thigh_r/C01_sensor_cassette
A09-09 X014 thigh_r/C02_sensor_cassette
A09-10 X017 foot_r/C01_sensor_cassette
A09-11 X018 foot_r/C02_sensor_cassette
A09-12 X033 calf_r.flex/sensor_cassette
A09-13 X034 ball_r.flex/sensor_cassette
A09-14 N004 calf_r.flex/magnet_cartridge
A09-15 N004 ball_r.flex/magnet_cartridge
A09-16 P013 thigh_r/P_magnet_cap
A09-17 P126 thigh_r/D_magnet_cap
A09-18 N003 thigh_r/C01_magnet_cartridge
A09-19 N003 thigh_r/C02_magnet_cartridge
A09-20 N003 foot_r/C01_magnet_cartridge
A09-21 N003 foot_r/C02_magnet_cartridge
A09-22 X074 thigh_r/P_pcb_clip_-14
A09-23 X075 thigh_r/P_pcb_clip_+14
A09-24 X077 thigh_r/D_pcb_clip_-14
A09-25 X078 thigh_r/D_pcb_clip_+14
A09-26 P012 thigh_r/P_radial_pad
A09-27 P125 thigh_r/D_radial_pad
