fukukawa89/PoseDollLab_Design/Hardware/PoseDoll44/bench/revO22/mechanical/section/SOP8_max.stl

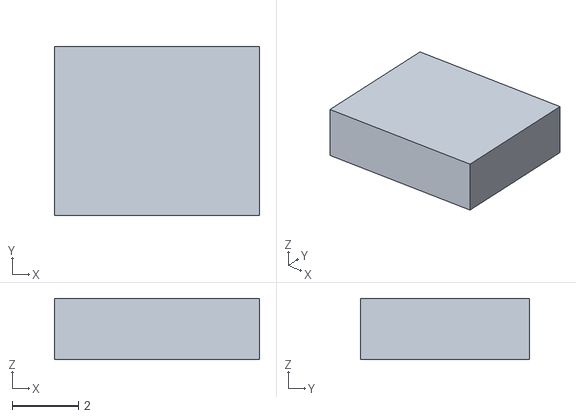
[picture p82: CAD file, 2026-10-01]
Hardware/PoseDoll44/bench/revO22/mechanical/section/SOP8_max.stl
6.20 x 5.10 x 1.85
