fukukawa89/PoseDollLab_Design/Hardware/PoseDoll44/bench/revO22/mechanical/stl/upperarm_r__D_case_plus.stl

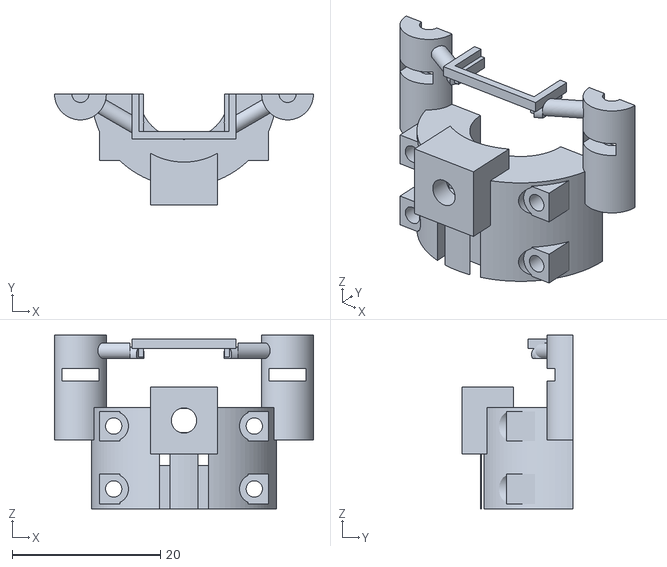
[picture p83: CAD file, 2026-10-01]
Hardware/PoseDoll44/bench/revO22/mechanical/stl/upperarm_r__D_case_plus.stl
35.0 x 15.0 x 23.5
