fukukawa89/PoseDollLab_Design/Hardware/PoseDoll44/bench/revO22/physical_tests/sensor_coupon/magnet_bridge.3mf

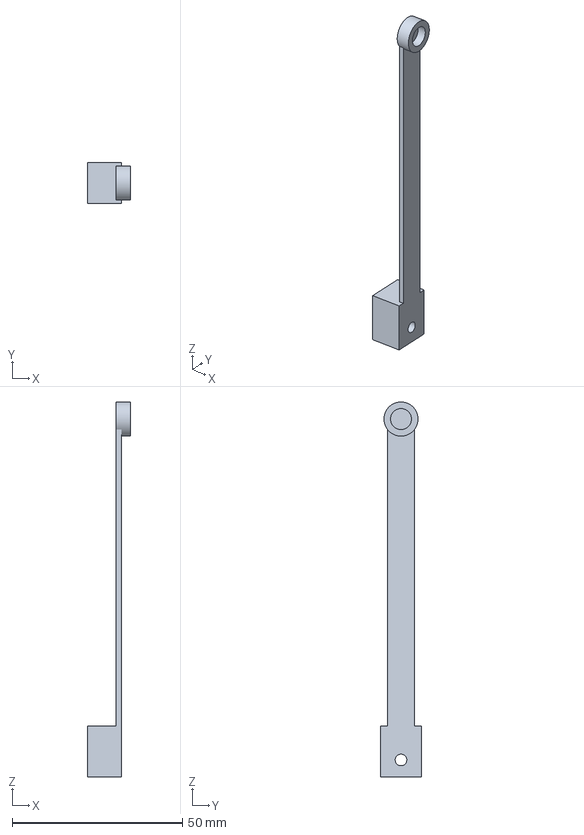
[picture p84: CAD file, 2026-10-01]
Hardware/PoseDoll44/bench/revO22/physical_tests/sensor_coupon/magnet_bridge.3mf
12.6 x 12.0 x 110.0 mm
