fukukawa89/PoseDollLab_Design/Hardware/PoseDoll44/bench/revO7/coupons/LP6_PEEK_coupon.step

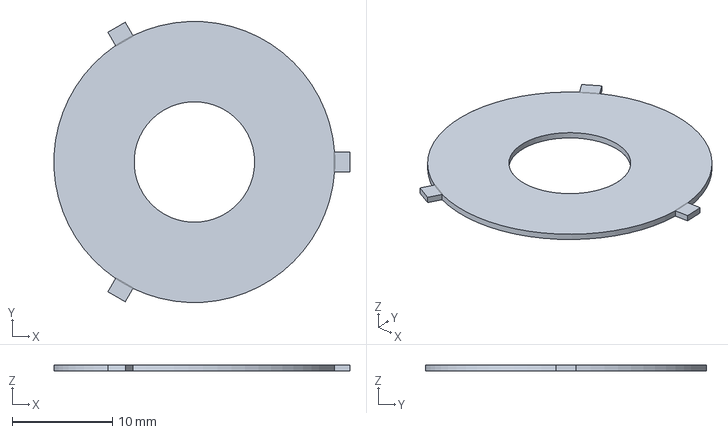
[picture p86: CAD file, 2026-09-30]
Hardware/PoseDoll44/bench/revO7/coupons/LP6_PEEK_coupon.step
29.5 x 28.0 x 0.6 mm
