fukukawa89/PoseDollLab_Design/Hardware/PoseDoll44/bench/revO8/fit_gauges/pin_D4.step

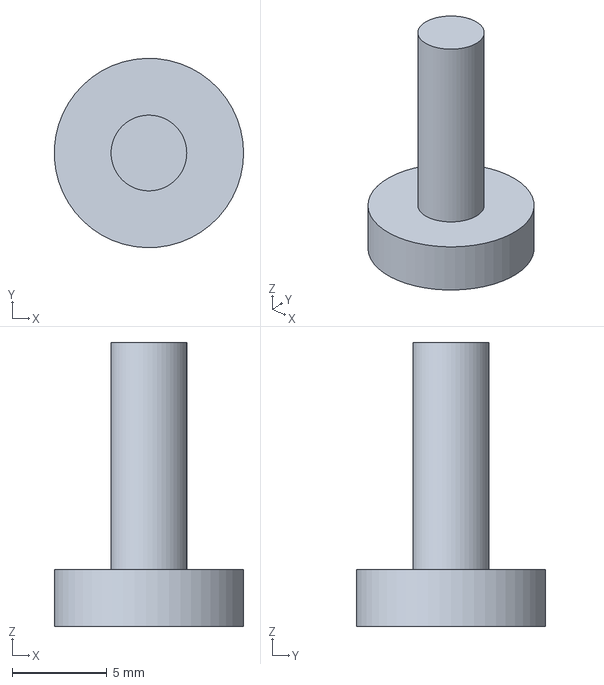
[picture p87: CAD file, 2026-09-30]
Hardware/PoseDoll44/bench/revO8/fit_gauges/pin_D4.step
9.99 x 10.00 x 15.0 mm
