fukukawa89/PoseDollLab_Design/Hardware/PoseDoll44/generated/revO10/runs/o10_20260926_r1/face_brake/C02_+1_shoulder_axle.stl

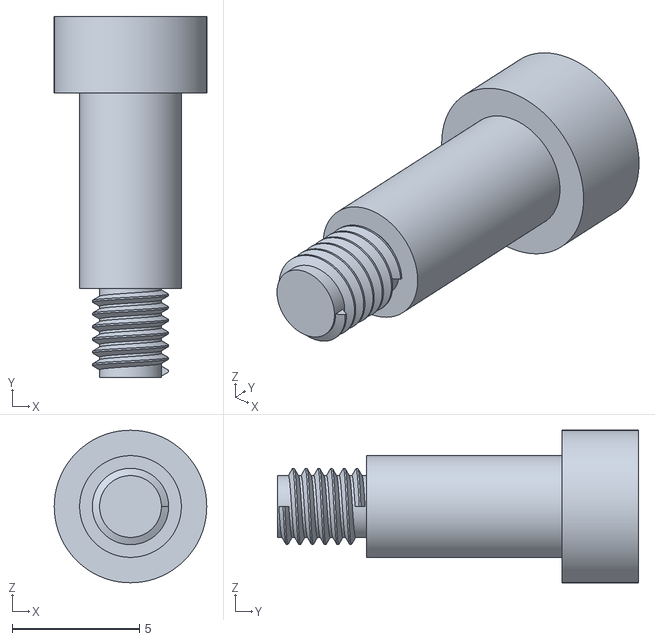
[picture p88: CAD file, 2026-09-30]
Hardware/PoseDoll44/generated/revO10/runs/o10_20260926_r1/face_brake/C02_+1_shoulder_axle.stl
6.00 x 14.2 x 6.00
