fukukawa89/PoseDollLab_Design/Hardware/PoseDoll44/generated/revO10/runs/o10_20260926_r1/internal_stops/C01.stl

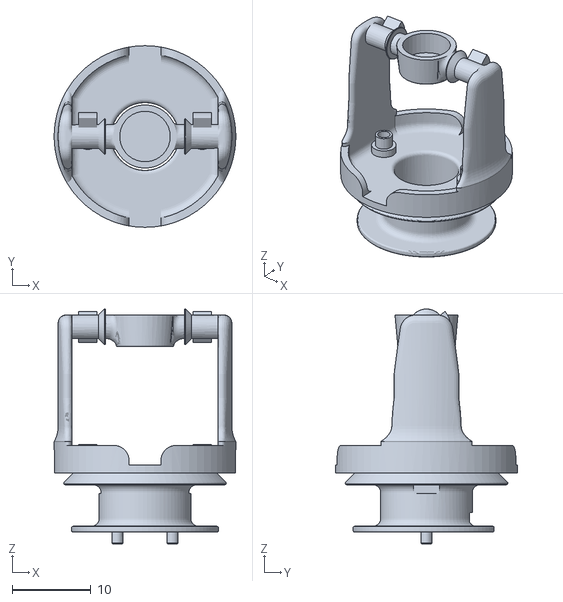
[picture p89: CAD file, 2026-09-30]
Hardware/PoseDoll44/generated/revO10/runs/o10_20260926_r1/internal_stops/C01.stl
23.0 x 23.0 x 29.8
