fukukawa89/PoseDollLab_Design/Hardware/PoseDoll44/generated/revO10/runs/o10_20260926_r1/slipring/existing_rotor.stl

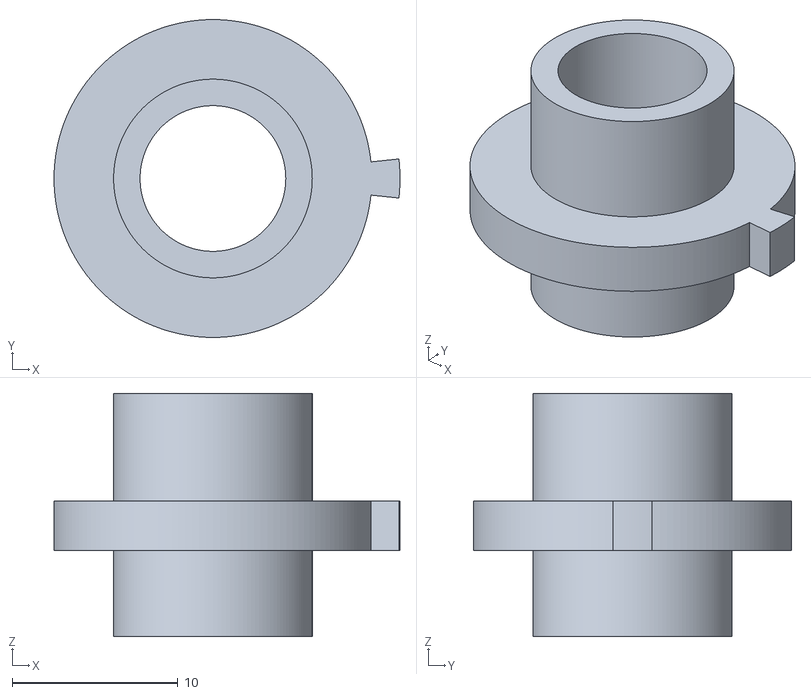
[picture p90: CAD file, 2026-09-30]
Hardware/PoseDoll44/generated/revO10/runs/o10_20260926_r1/slipring/existing_rotor.stl
20.9 x 19.2 x 14.7
