fukukawa89/PoseDollLab_Design/Hardware/PoseDoll44/generated/revO5CN/runs/cn_20260924_r1/C2_body.step

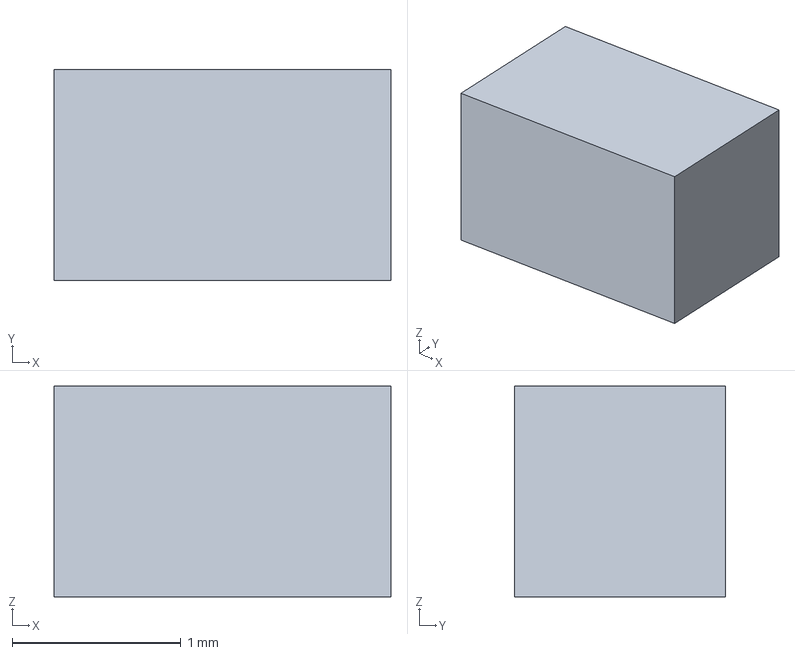
[picture p91: CAD file, 2026-09-30]
Hardware/PoseDoll44/generated/revO5CN/runs/cn_20260924_r1/C2_body.step
2.00 x 1.25 x 1.25 mm
