fukukawa89/PoseDollLab_Design/Hardware/PoseDoll44/generated/revO6/runs/o6_20260924_r1/joint_L6_validated/thrust_front_R.step

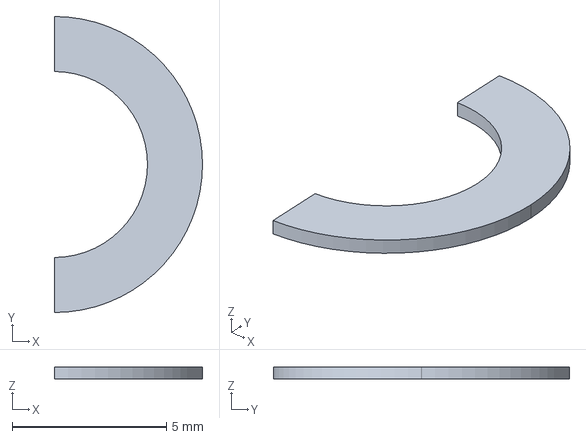
[picture p92: CAD file, 2026-09-30]
Hardware/PoseDoll44/generated/revO6/runs/o6_20260924_r1/joint_L6_validated/thrust_front_R.step
4.80 x 9.60 x 0.4 mm
