fukukawa89/PoseDollLab_Design/Hardware/PoseDoll44/generated/revO7/runs/o7_20260924_r1/LP6_current/guide_sleeve_1.step

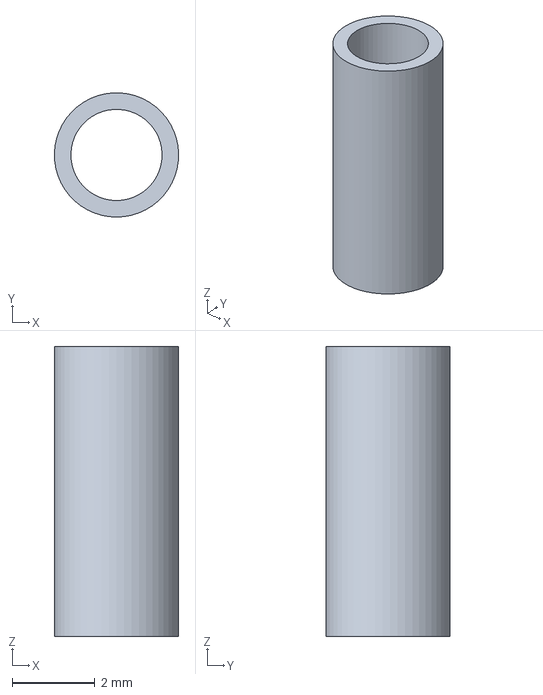
[picture p93: CAD file, 2026-09-30]
Hardware/PoseDoll44/generated/revO7/runs/o7_20260924_r1/LP6_current/guide_sleeve_1.step
3.00 x 3.00 x 7.00 mm
