fukukawa89/PoseDollLab_Design/Hardware/PoseDoll44/generated/revO8/runs/o8_20260925_r1/fork_extension_4mm/C02.stl

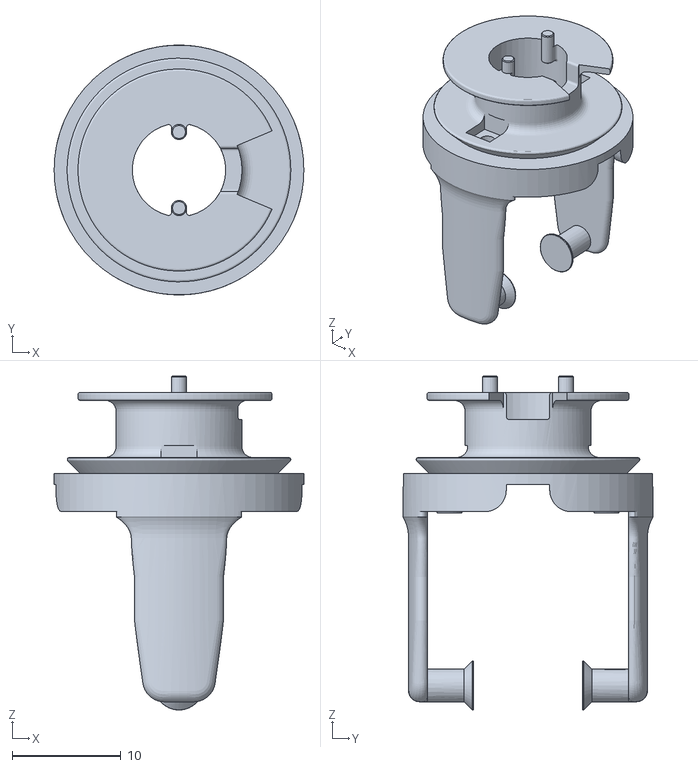
[picture p96: CAD file, 2026-09-30]
Hardware/PoseDoll44/generated/revO8/runs/o8_20260925_r1/fork_extension_4mm/C02.stl
23.0 x 23.0 x 30.8
