fukukawa89/PoseDollLab_Design/Hardware/PoseDoll44/verification/revO6/runs/o6_20260924_r1/service/L6_hollow_pin_spanner.step

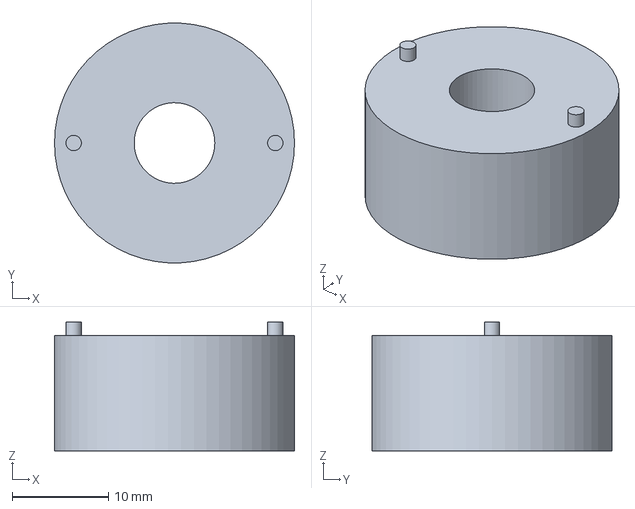
[picture p98: CAD file, 2026-09-30]
Hardware/PoseDoll44/verification/revO6/runs/o6_20260924_r1/service/L6_hollow_pin_spanner.step
25.0 x 25.0 x 13.4 mm
