fukukawa89/PoseDollLab_Design/Hardware/PoseDoll44/bench/revO15/print_batch/P214.3mf

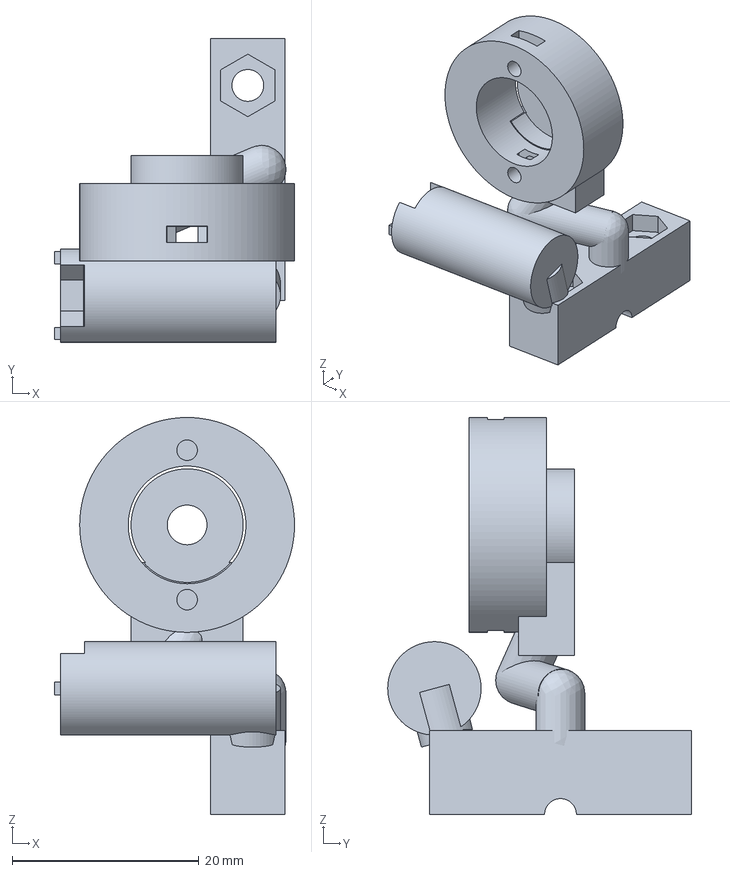
[picture p100: CAD file, 2026-09-30]
Hardware/PoseDoll44/bench/revO15/print_batch/P214.3mf
25.7 x 32.5 x 42.5 mm
