fukukawa89/PoseDollLab_Design/Hardware/PoseDoll44/bench/revO16/print_batch/P007.3mf

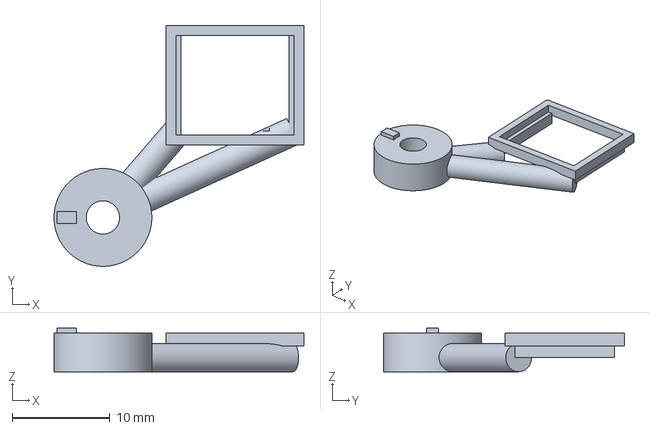
[picture p101: CAD file, 2026-09-30]
Hardware/PoseDoll44/bench/revO16/print_batch/P007.3mf
25.5 x 24.6 x 4.45 mm
