fukukawa89/PoseDollLab_Design/Hardware/PoseDoll44/bench/revO19/print_batch/L002.3mf

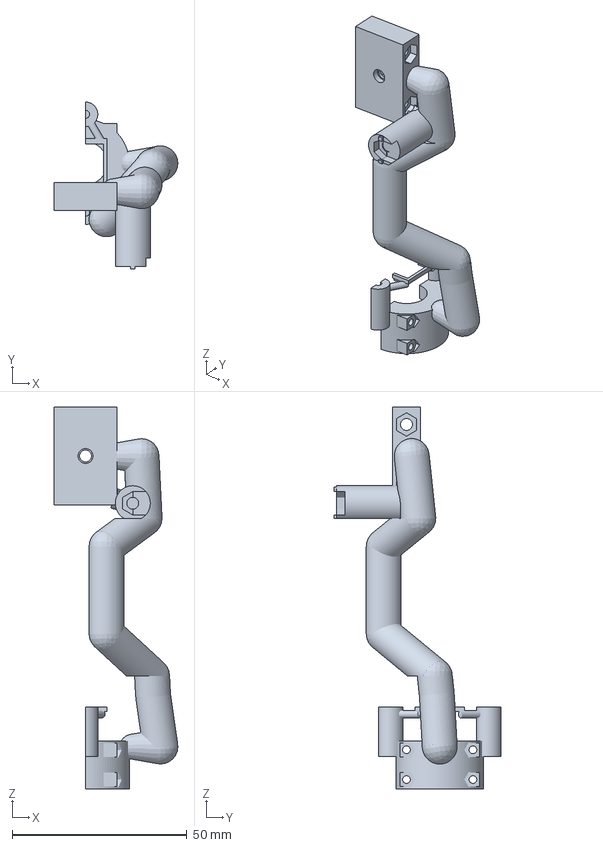
[picture p102: CAD file, 2026-09-30]
Hardware/PoseDoll44/bench/revO19/print_batch/L002.3mf
35.4 x 47.7 x 109.2 mm
