fukukawa89/PoseDollLab_Design/Hardware/PoseDoll44/bench/revO20/print_batch/W012.3mf

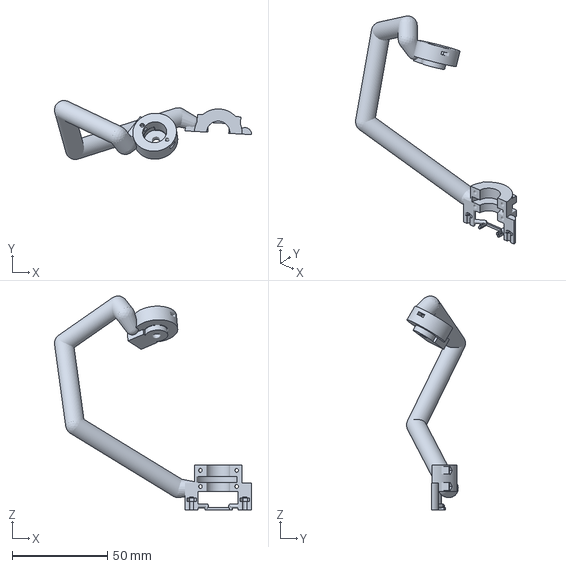
[picture p103: CAD file, 2026-09-30]
Hardware/PoseDoll44/bench/revO20/print_batch/W012.3mf
103.3 x 30.9 x 112.2 mm
