fukukawa89/PoseDollLab_Design/Hardware/PoseDoll44/bench/revO22/a1mini/plates/A04_left_arm_1.3mf

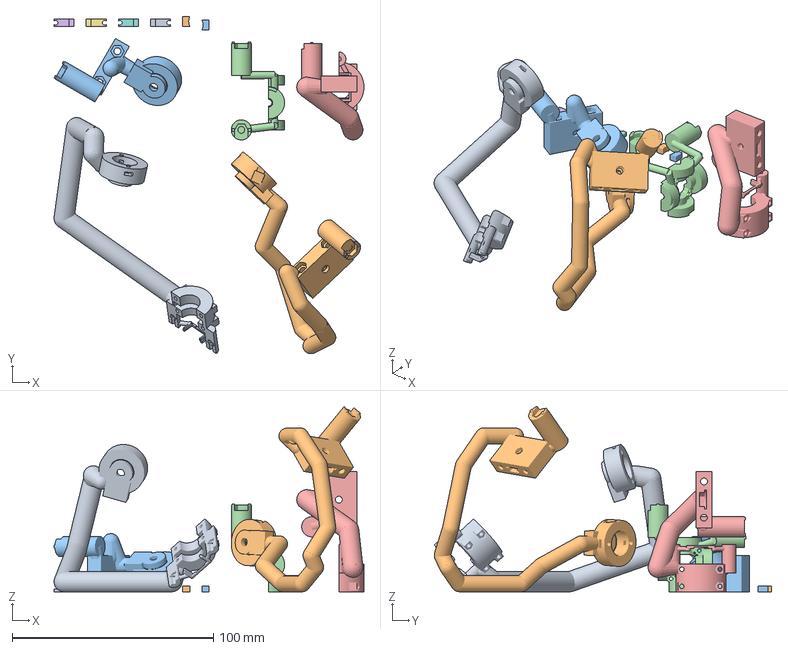
[picture p104: CAD file, 2026-10-01]
Hardware/PoseDoll44/bench/revO22/a1mini/plates/A04_left_arm_1.3mf
154.1 x 167.8 x 92.3 mm
A04-01 X054 frame/clavicle_l
A04-02 W005 frame/clavicle_l.protract_frame
A04-03 H004 frame/elbow_l
A04-04 P051 upperarm_l/C14
A04-05 X058 frame/upperarm_l
A04-06 X051 upperarm_l/P_pcb_clip_-14
A04-07 X056 upperarm_l/D_pcb_clip_+14
A04-08 X055 upperarm_l/D_pcb_clip_-14
A04-09 X052 upperarm_l/P_pcb_clip_+14
A04-10 P061 upperarm_l/P_radial_pad
A04-11 P066 upperarm_l/D_radial_pad
