fukukawa89/PoseDollLab_Design/Hardware/PoseDoll44/bench/revO22/a1mini_supports/projects/A10_lower_legs_PLA_supports.3mf

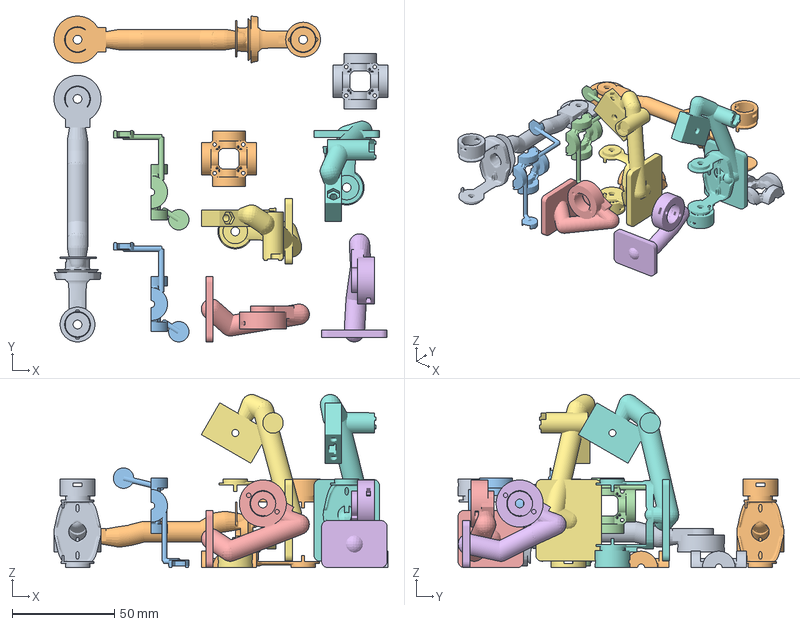
[picture p105: CAD file, 2026-10-04]
Hardware/PoseDoll44/bench/revO22/a1mini_supports/projects/A10_lower_legs_PLA_supports.3mf
163.3 x 159.3 x 84.6 mm
A10-01 W006 frame/calf_r
A10-02 W007 frame/calf_l
A10-03 P130 foot_l/C14
A10-04 P130 foot_r/C14
A10-05 W003 frame/ball_l
A10-06 W001 frame/ball_r
A10-07 W016 frame/foot_l
A10-08 W017 frame/foot_r
A10-09 P131 foot_l/C15
A10-10 P131 foot_r/C15
