fukukawa89/PoseDollLab_Design/Hardware/PoseDoll44/bench/revO22/mechanical/section/pcb.stl

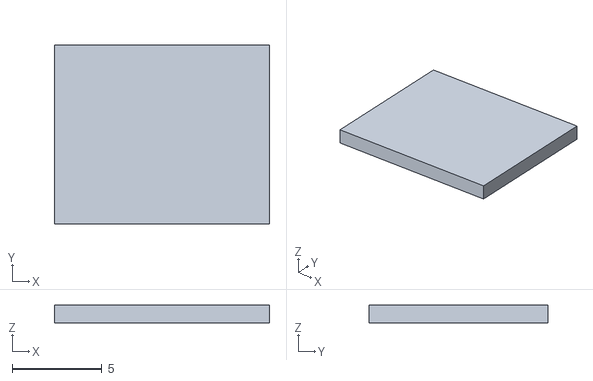
[picture p106: CAD file, 2026-10-01]
Hardware/PoseDoll44/bench/revO22/mechanical/section/pcb.stl
12.0 x 10.0 x 1.00
