fukukawa89/PoseDollLab_Design/Hardware/PoseDoll44/bench/revO22/print_batch/X021.3mf

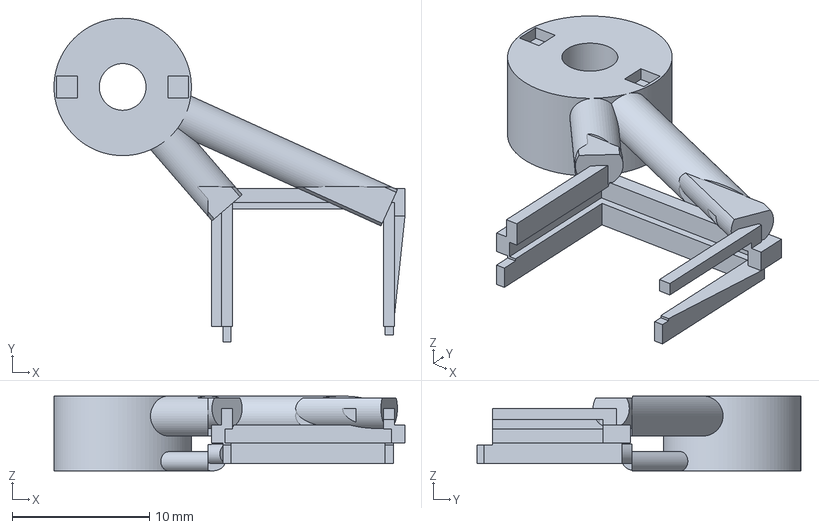
[picture p107: CAD file, 2026-10-01]
Hardware/PoseDoll44/bench/revO22/print_batch/X021.3mf
25.6 x 23.6 x 5.45 mm
