fukukawa89/PoseDollLab_Design/Hardware/PoseDoll44/bench/revO7/coupons/LP6_metal_counterface.step

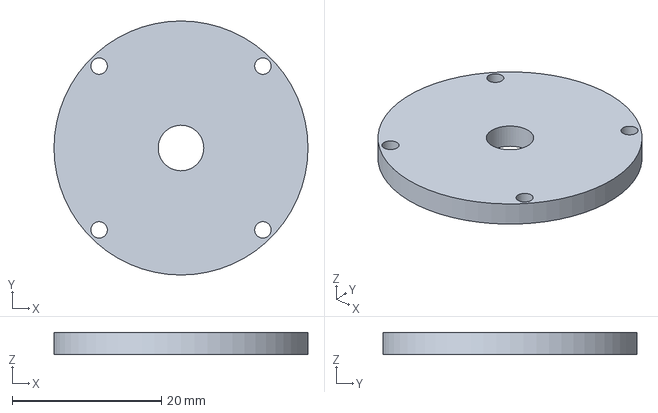
[picture p108: CAD file, 2026-09-30]
Hardware/PoseDoll44/bench/revO7/coupons/LP6_metal_counterface.step
34.0 x 34.0 x 3.00 mm
