fukukawa89/PoseDollLab_Design/Hardware/PoseDoll44/bench/revO8/fit_gauges/fastener_gauge.step

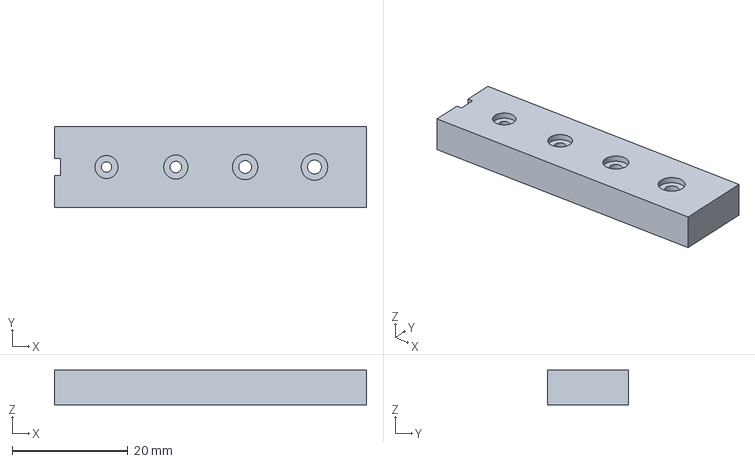
[picture p109: CAD file, 2026-09-30]
Hardware/PoseDoll44/bench/revO8/fit_gauges/fastener_gauge.step
54.0 x 14.0 x 6.00 mm
