fukukawa89/PoseDollLab_Design/Hardware/PoseDoll44/generated/revO10/runs/o10_20260926_r1/face_brake/C02_+1_spring1.stl

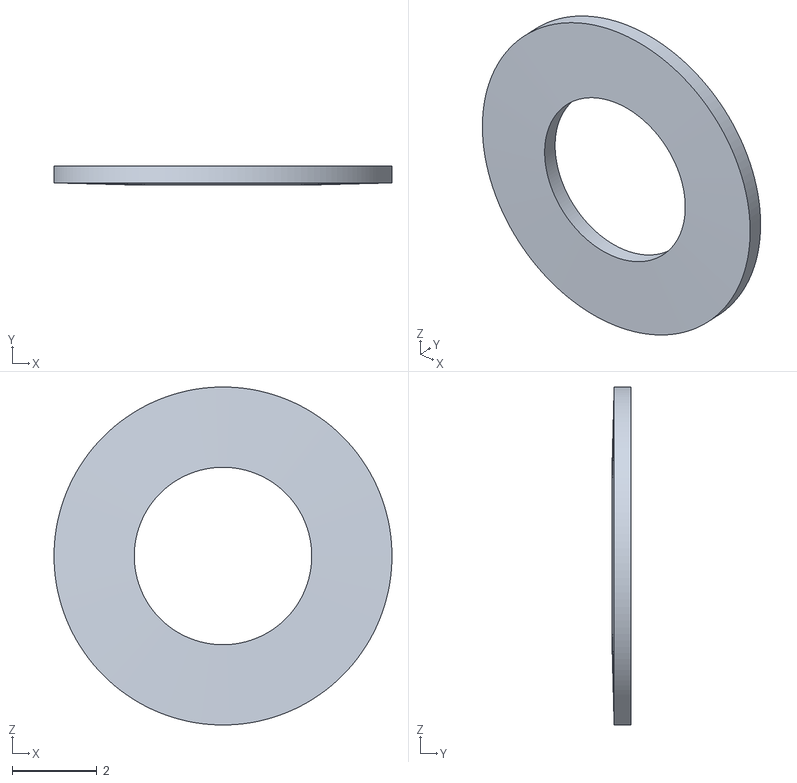
[picture p110: CAD file, 2026-09-30]
Hardware/PoseDoll44/generated/revO10/runs/o10_20260926_r1/face_brake/C02_+1_spring1.stl
8.00 x 0.45 x 8.00
