fukukawa89/PoseDollLab_Design/Hardware/PoseDoll44/generated/revO10/runs/o10_20260926_r1/internal_stops/C15.stl

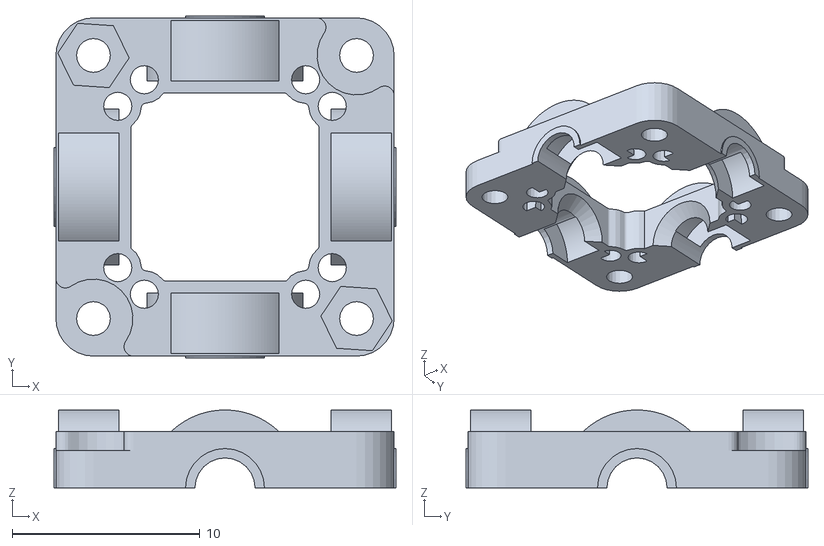
[picture p111: CAD file, 2026-09-30]
Hardware/PoseDoll44/generated/revO10/runs/o10_20260926_r1/internal_stops/C15.stl
18.2 x 18.2 x 4.15
