fukukawa89/PoseDollLab_Design/Hardware/PoseDoll44/generated/revO10/runs/o10_20260926_r1/slipring/proposed_sleeve.stl

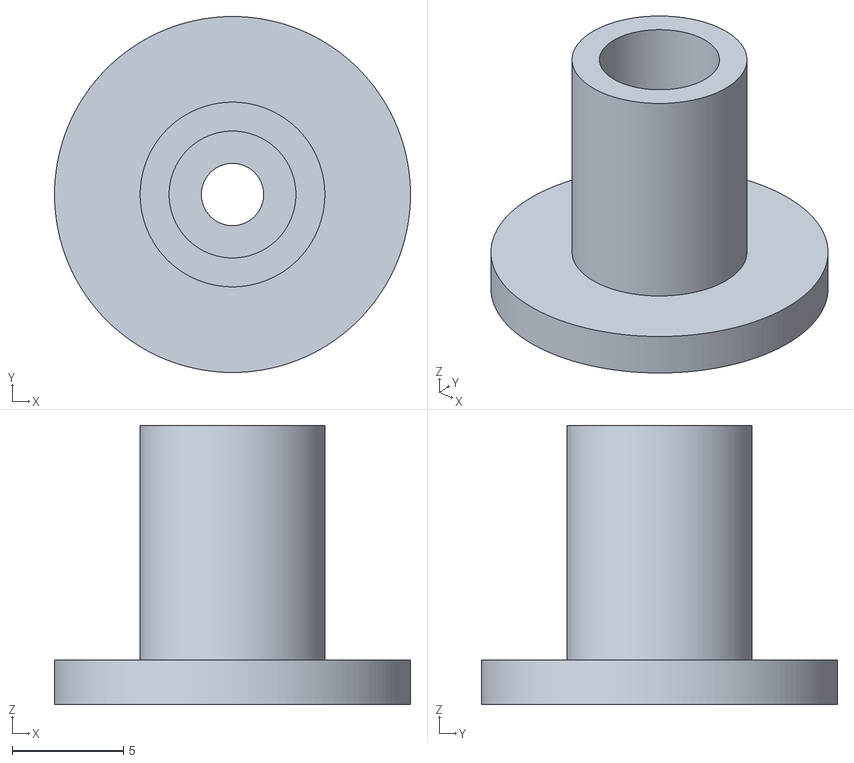
[picture p112: CAD file, 2026-09-30]
Hardware/PoseDoll44/generated/revO10/runs/o10_20260926_r1/slipring/proposed_sleeve.stl
16.0 x 16.0 x 12.5
