fukukawa89/PoseDollLab_Design/Hardware/PoseDoll44/generated/revO6/runs/o6_20260924_r1/joint_L6_validated/taper_output_hub.step

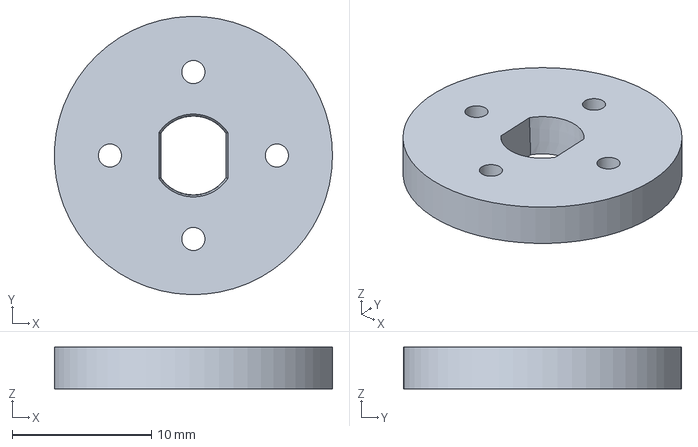
[picture p113: CAD file, 2026-09-30]
Hardware/PoseDoll44/generated/revO6/runs/o6_20260924_r1/joint_L6_validated/taper_output_hub.step
20.0 x 20.0 x 3.00 mm
