fukukawa89/PoseDollLab_Design/Hardware/PoseDoll44/generated/revO6/runs/o6_20260924_r1/joint_M4_validated/thrust_front_L.step

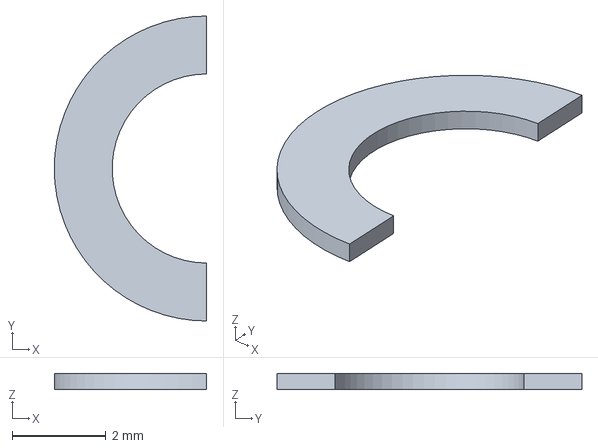
[picture p114: CAD file, 2026-09-30]
Hardware/PoseDoll44/generated/revO6/runs/o6_20260924_r1/joint_M4_validated/thrust_front_L.step
3.25 x 6.50 x 0.35 mm
