fukukawa89/PoseDollLab_Design/Hardware/PoseDoll44/generated/revO7/runs/o7_20260924_r1/LP6_current/spring_upper_seat_0.step

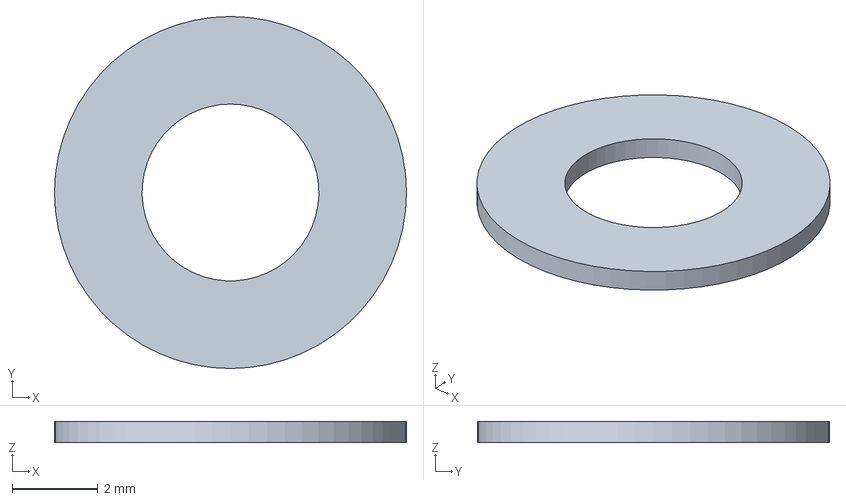
[picture p115: CAD file, 2026-09-30]
Hardware/PoseDoll44/generated/revO7/runs/o7_20260924_r1/LP6_current/spring_upper_seat_0.step
8.20 x 8.20 x 0.5 mm
