fukukawa89/PoseDollLab_Design/Hardware/PoseDoll44/bench/revO15/print_batch/P213.3mf

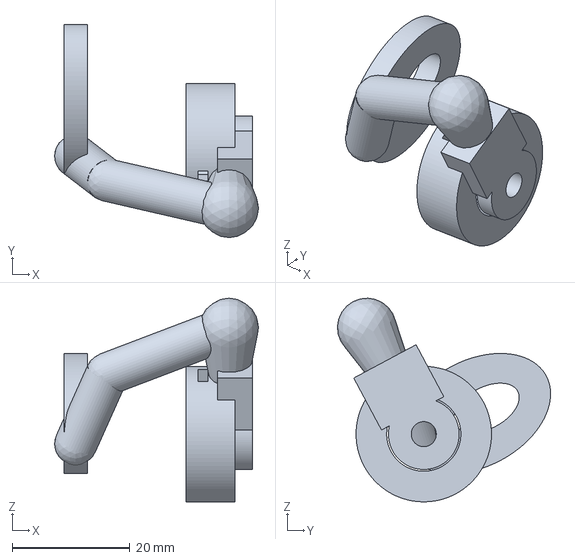
[picture p118: CAD file, 2026-09-30]
Hardware/PoseDoll44/bench/revO15/print_batch/P213.3mf
34.6 x 36.2 x 34.6 mm
