fukukawa89/PoseDollLab_Design/Hardware/PoseDoll44/bench/revO16/print_batch/P034.stl

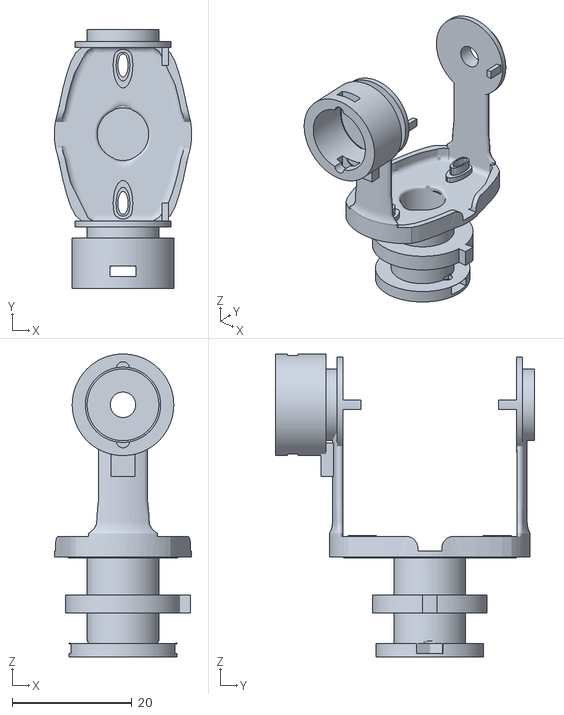
[picture p119: CAD file, 2026-09-30]
Hardware/PoseDoll44/bench/revO16/print_batch/P034.stl
23.0 x 43.3 x 50.7
