fukukawa89/PoseDollLab_Design/Hardware/PoseDoll44/bench/revO17/print_batch/P189.3mf

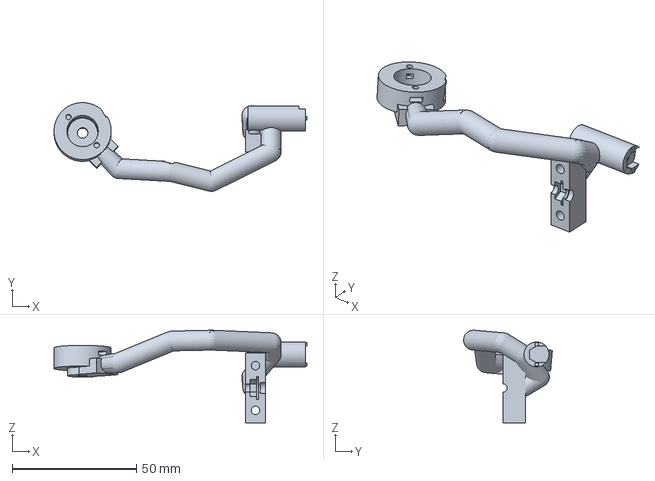
[picture p120: CAD file, 2026-09-30]
Hardware/PoseDoll44/bench/revO17/print_batch/P189.3mf
101.7 x 35.7 x 37.2 mm
