fukukawa89/PoseDollLab_Design/Hardware/PoseDoll44/bench/revO19/print_batch/L001.3mf

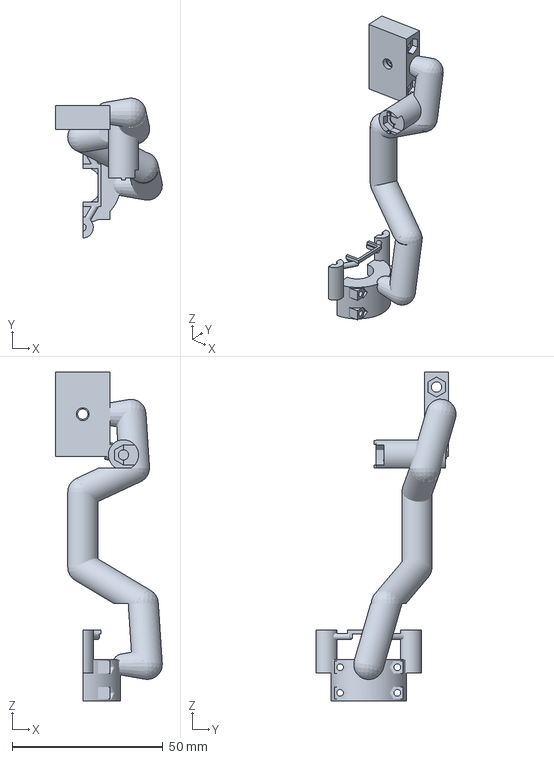
[picture p121: CAD file, 2026-09-30]
Hardware/PoseDoll44/bench/revO19/print_batch/L001.3mf
35.4 x 46.5 x 109.2 mm
