fukukawa89/PoseDollLab_Design/Hardware/PoseDoll44/bench/revO20/print_batch/W014.3mf

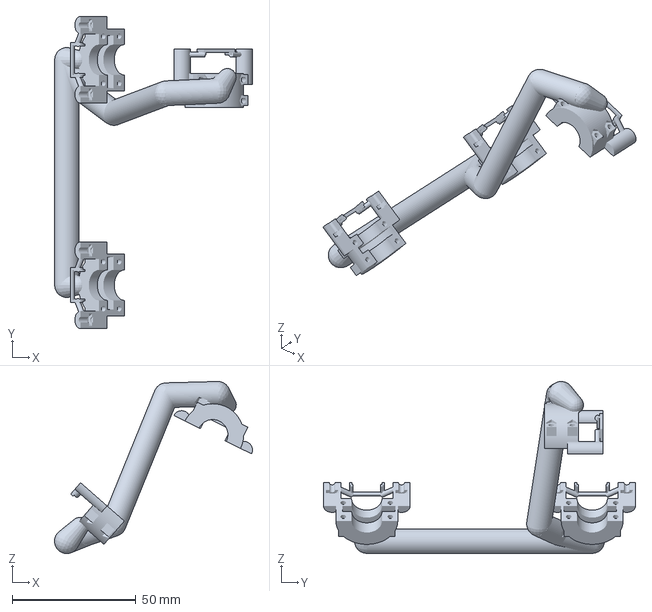
[picture p122: CAD file, 2026-09-30]
Hardware/PoseDoll44/bench/revO20/print_batch/W014.3mf
79.9 x 126.0 x 69.5 mm
