fukukawa89/PoseDollLab_Design/Hardware/PoseDoll44/bench/revO22/mechanical/section/C2.stl

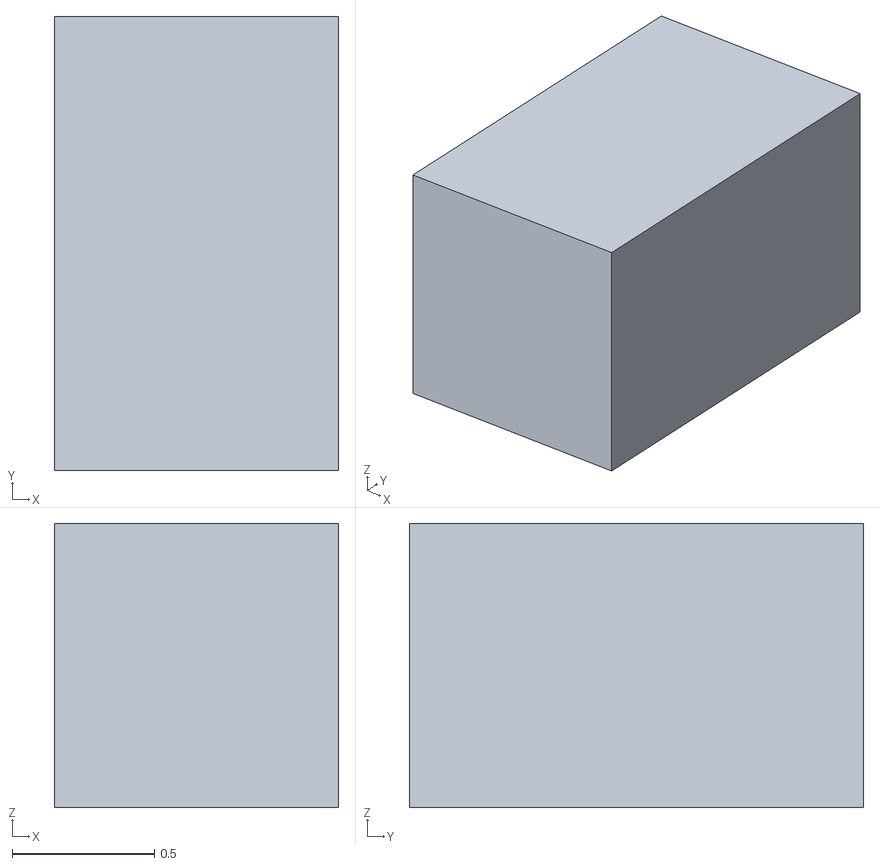
[picture p123: CAD file, 2026-10-01]
Hardware/PoseDoll44/bench/revO22/mechanical/section/C2.stl
1.00 x 1.60 x 1.00
