fukukawa89/PoseDollLab_Design/Hardware/PoseDoll44/bench/revO22/mechanical/stl/frame__pelvis.stl

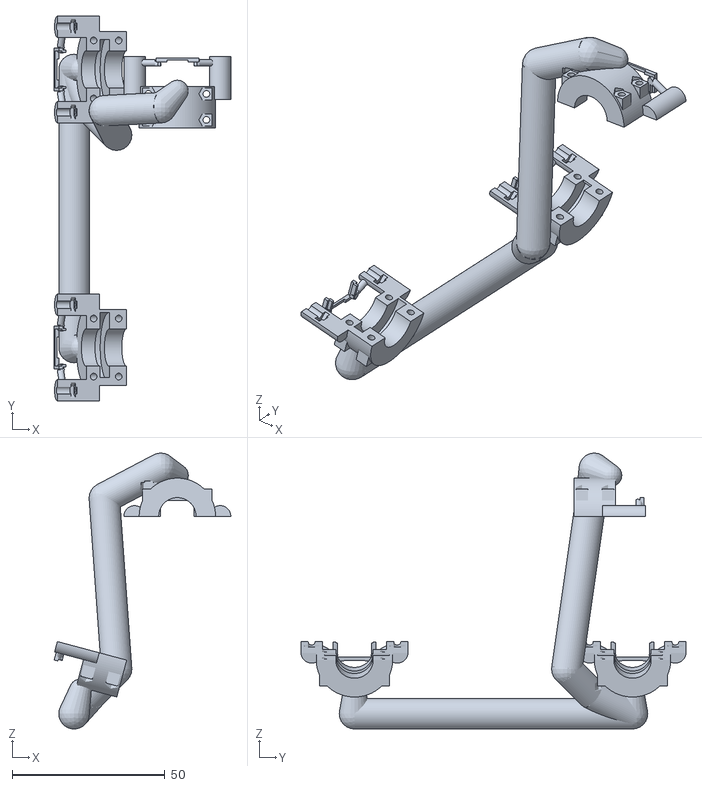
[picture p124: CAD file, 2026-10-01]
Hardware/PoseDoll44/bench/revO22/mechanical/stl/frame__pelvis.stl
57.8 x 126.0 x 90.3
