fukukawa89/PoseDollLab_Design/Hardware/PoseDoll44/bench/revO22/print_batch/X078.3mf

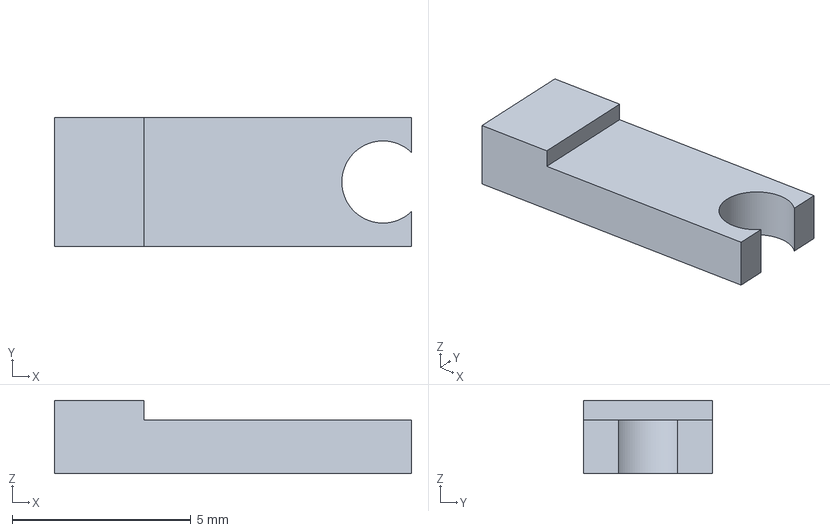
[picture p125: CAD file, 2026-10-01]
Hardware/PoseDoll44/bench/revO22/print_batch/X078.3mf
10.0 x 3.60 x 2.05 mm
