fukukawa89/PoseDollLab_Design/Hardware/PoseDoll44/bench/revO7/coupons/M4_metal_counterface.step

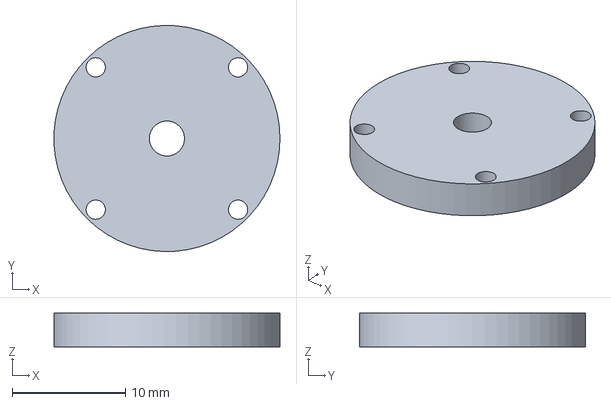
[picture p126: CAD file, 2026-09-30]
Hardware/PoseDoll44/bench/revO7/coupons/M4_metal_counterface.step
20.0 x 20.0 x 3.00 mm
