fukukawa89/PoseDollLab_Design/Hardware/PoseDoll44/generated/revO10/runs/o10_20260926_r1/face_brake/C01_+1_outer_plate.stl

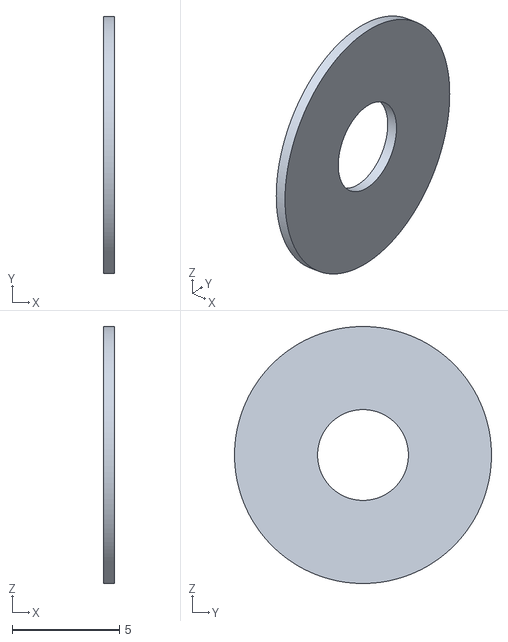
[picture p127: CAD file, 2026-09-30]
Hardware/PoseDoll44/generated/revO10/runs/o10_20260926_r1/face_brake/C01_+1_outer_plate.stl
0.5 x 12.0 x 12.0
