fukukawa89/PoseDollLab_Design/Hardware/PoseDoll44/generated/revO10/runs/o10_20260926_r1/slipring/catalogue_rotor_tip.stl

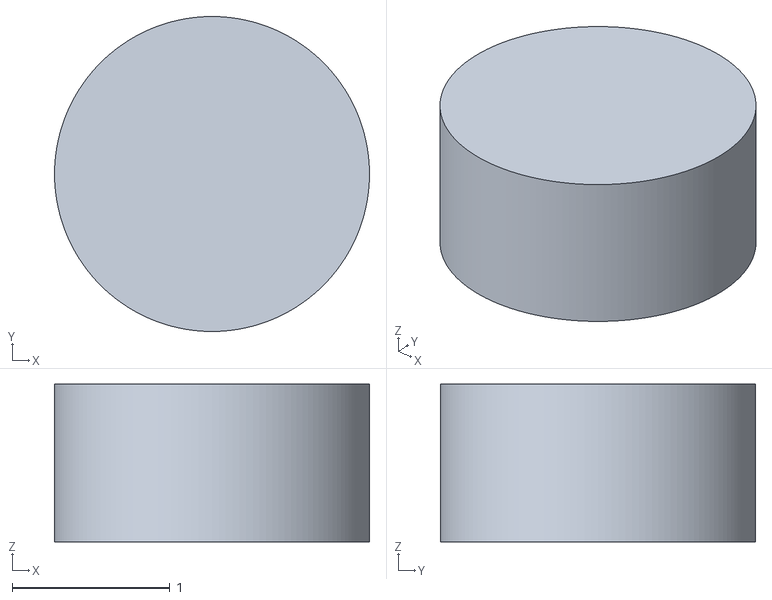
[picture p128: CAD file, 2026-09-30]
Hardware/PoseDoll44/generated/revO10/runs/o10_20260926_r1/slipring/catalogue_rotor_tip.stl
2.00 x 2.00 x 1.00
