fukukawa89/PoseDollLab_Design/Hardware/PoseDoll44/bench/revO15/PRINT_MANNY.zh-CN.md

# Manny 打印数量

只打印本表列出的编号；单位mm，数量为净数量。

| 编号 | 数量 | 需要支撑 | 对应部位 |
|---|---:|---|---|
| P001 | 1 | 是 | waist/C01 |
| P002 | 1 | 是 | waist/C14 |
| P003 | 1 | 是 | waist/C15 |
| P004 | 3 | 是 | waist/C01_magnet_seat、head/C01_magnet_seat、thigh_r/C01_magnet_seat |
| P005 | 3 | 是 | waist/C01_magnet_cap、head/C01_magnet_cap、thigh_r/C01_magnet_cap |
| P006 | 2 | 是 | waist/C01_pcb_clip、head/C01_pcb_clip |
| P007 | 2 | 是 | waist/C01_sensor_cradle、head/C01_sensor_cradle |
| P008 | 1 | 是 | waist/C02_magnet_seat |
| P009 | 1 | 是 | waist/C02_magnet_cap |
| P010 | 2 | 是 | waist/C02_pcb_clip、head/C02_pcb_clip |
| P011 | 2 | 是 | waist/C02_sensor_cradle、head/C02_sensor_cradle |
| P012 | 2 | 按实际切片复核 | waist/P_radial_pad、thigh_r/P_radial_pad |
| P013 | 2 | 是 | waist/P_magnet_cap、thigh_r/P_magnet_cap |
| P014 | 2 | 按实际切片复核 | waist/P_pcb_clip_-14、thigh_r/P_pcb_clip_-14 |
| P015 | 2 | 按实际切片复核 | waist/P_pcb_clip_+14、thigh_r/P_pcb_clip_+14 |
| P016 | 2 | 是 | waist/P_case_plus、thigh_r/P_case_plus |
| P017 | 1 | 是 | chest/C01 |
| P018 | 1 | 是 | chest/C14 |
| P019 | 1 | 是 | chest/C15 |
| P020 | 1 | 是 | chest/C01_magnet_seat |
| P021 | 1 | 是 | chest/C01_magnet_cap |
| P022 | 1 | 是 | chest/C01_pcb_clip |
| P023 | 1 | 是 | chest/C01_sensor_cradle |
| P024 | 1 | 是 | chest/C02_magnet_seat |
| P025 | 1 | 是 | chest/C02_magnet_cap |
| P026 | 1 | 是 | chest/C02_pcb_clip |
| P027 | 1 | 是 | chest/C02_sensor_cradle |
| P028 | 1 | 按实际切片复核 | chest/P_radial_pad |
| P029 | 1 | 是 | chest/P_magnet_cap |
| P030 | 1 | 按实际切片复核 | chest/P_pcb_clip_-14 |
| P031 | 1 | 按实际切片复核 | chest/P_pcb_clip_+14 |
| P032 | 1 | 是 | chest/P_case_plus |
| P033 | 1 | 是 | head/C01 |
| P034 | 1 | 是 | head/C02 |
| P035 | 1 | 是 | head/C14 |
| P036 | 1 | 是 | head/C15 |
| P037 | 1 | 是 | head/C02_magnet_seat |
| P038 | 1 | 是 | head/C02_magnet_cap |
| P039 | 1 | 按实际切片复核 | head/P_radial_pad |
| P040 | 1 | 是 | head/P_magnet_cap |
| P041 | 1 | 按实际切片复核 | head/P_pcb_clip_-14 |
| P042 | 1 | 按实际切片复核 | head/P_pcb_clip_+14 |
| P043 | 1 | 是 | head/P_case_plus |
| P044 | 1 | 按实际切片复核 | head/D_radial_pad |
| P045 | 1 | 是 | head/D_magnet_cap |
| P046 | 1 | 按实际切片复核 | head/D_pcb_clip_-14 |
| P047 | 1 | 按实际切片复核 | head/D_pcb_clip_+14 |
| P048 | 1 | 是 | head/D_case_plus |
| P049 | 1 | 是 | upperarm_l/C01 |
| P050 | 1 | 是 | upperarm_l/C02 |
| P051 | 1 | 是 | upperarm_l/C14 |
| P052 | 1 | 是 | upperarm_l/C15 |
| P053 | 1 | 是 | upperarm_l/C01_magnet_seat |
| P054 | 1 | 是 | upperarm_l/C01_magnet_cap |
| P055 | 1 | 是 | upperarm_l/C01_pcb_clip |
| P056 | 1 | 是 | upperarm_l/C01_sensor_cradle |
| P057 | 1 | 是 | upperarm_l/C02_magnet_seat |
| P058 | 1 | 是 | upperarm_l/C02_magnet_cap |
| P059 | 1 | 是 | upperarm_l/C02_pcb_clip |
| P060 | 1 | 是 | upperarm_l/C02_sensor_cradle |
| P061 | 1 | 按实际切片复核 | upperarm_l/P_radial_pad |
| P062 | 1 | 是 | upperarm_l/P_magnet_cap |
| P063 | 1 | 按实际切片复核 | upperarm_l/P_pcb_clip_-14 |
| P064 | 1 | 按实际切片复核 | upperarm_l/P_pcb_clip_+14 |
| P065 | 1 | 是 | upperarm_l/P_case_plus |
| P066 | 1 | 按实际切片复核 | upperarm_l/D_radial_pad |
| P067 | 1 | 是 | upperarm_l/D_magnet_cap |
| P068 | 1 | 按实际切片复核 | upperarm_l/D_pcb_clip_-14 |
| P069 | 1 | 按实际切片复核 | upperarm_l/D_pcb_clip_+14 |
| P070 | 1 | 是 | upperarm_l/D_case_plus |
| P071 | 1 | 是 | upperarm_r/C01 |
| P072 | 1 | 是 | upperarm_r/C02 |
| P073 | 1 | 是 | upperarm_r/C14 |
| P074 | 1 | 是 | upperarm_r/C15 |
| P075 | 1 | 是 | upperarm_r/C01_magnet_seat |
| P076 | 1 | 是 | upperarm_r/C01_magnet_cap |
| P077 | 1 | 是 | upperarm_r/C01_pcb_clip |
| P078 | 1 | 是 | upperarm_r/C01_sensor_cradle |
| P079 | 1 | 是 | upperarm_r/C02_magnet_seat |
| P080 | 1 | 是 | upperarm_r/C02_magnet_cap |
| P081 | 1 | 是 | upperarm_r/C02_pcb_clip |
| P082 | 1 | 是 | upperarm_r/C02_sensor_cradle |
| P083 | 1 | 按实际切片复核 | upperarm_r/P_radial_pad |
| P084 | 1 | 是 | upperarm_r/P_magnet_cap |
| P085 | 1 | 按实际切片复核 | upperarm_r/P_pcb_clip_-14 |
| P086 | 1 | 按实际切片复核 | upperarm_r/P_pcb_clip_+14 |
| P087 | 1 | 是 | upperarm_r/P_case_plus |
| P088 | 1 | 按实际切片复核 | upperarm_r/D_radial_pad |
| P089 | 1 | 是 | upperarm_r/D_magnet_cap |
| P090 | 1 | 按实际切片复核 | upperarm_r/D_pcb_clip_-14 |
| P091 | 1 | 按实际切片复核 | upperarm_r/D_pcb_clip_+14 |
| P092 | 1 | 是 | upperarm_r/D_case_plus |
| P093 | 1 | 是 | thigh_l/C01 |
| P094 | 1 | 是 | thigh_l/C02 |
| P095 | 1 | 是 | thigh_l/C14 |
| P096 | 1 | 是 | thigh_l/C15 |
| P097 | 1 | 是 | thigh_l/C01_magnet_seat |
| P098 | 1 | 是 | thigh_l/C01_magnet_cap |
| P099 | 1 | 是 | thigh_l/C01_pcb_clip |
| P100 | 1 | 是 | thigh_l/C01_sensor_cradle |
| P101 | 1 | 是 | thigh_l/C02_magnet_seat |
| P102 | 1 | 是 | thigh_l/C02_magnet_cap |
| P103 | 1 | 是 | thigh_l/C02_pcb_clip |
| P104 | 1 | 是 | thigh_l/C02_sensor_cradle |
| P105 | 1 | 按实际切片复核 | thigh_l/P_radial_pad |
| P106 | 1 | 是 | thigh_l/P_magnet_cap |
| P107 | 1 | 按实际切片复核 | thigh_l/P_pcb_clip_-14 |
| P108 | 1 | 按实际切片复核 | thigh_l/P_pcb_clip_+14 |
| P109 | 1 | 是 | thigh_l/P_case_plus |
| P110 | 1 | 按实际切片复核 | thigh_l/D_radial_pad |
| P111 | 1 | 是 | thigh_l/D_magnet_cap |
| P112 | 1 | 按实际切片复核 | thigh_l/D_pcb_clip_-14 |
| P113 | 1 | 按实际切片复核 | thigh_l/D_pcb_clip_+14 |
| P114 | 1 | 是 | thigh_l/D_case_plus |
| P115 | 1 | 是 | thigh_r/C01 |
| P116 | 1 | 是 | thigh_r/C02 |
| P117 | 1 | 是 | thigh_r/C14 |
| P118 | 1 | 是 | thigh_r/C15 |
| P119 | 1 | 是 | thigh_r/C01_pcb_clip |
| P120 | 1 | 是 | thigh_r/C01_sensor_cradle |
| P121 | 1 | 是 | thigh_r/C02_magnet_seat |
| P122 | 1 | 是 | thigh_r/C02_magnet_cap |
| P123 | 1 | 是 | thigh_r/C02_pcb_clip |
| P124 | 1 | 是 | thigh_r/C02_sensor_cradle |
| P125 | 1 | 按实际切片复核 | thigh_r/D_radial_pad |
| P126 | 1 | 是 | thigh_r/D_magnet_cap |
| P127 | 1 | 按实际切片复核 | thigh_r/D_pcb_clip_-14 |
| P128 | 1 | 按实际切片复核 | thigh_r/D_pcb_clip_+14 |
| P129 | 1 | 是 | thigh_r/D_case_plus |
| P130 | 2 | 是 | foot_l/C14、foot_r/C14 |
| P131 | 2 | 是 | foot_l/C15、foot_r/C15 |
| P132 | 2 | 是 | foot_l/C01_magnet_seat、foot_r/C01_magnet_seat |
| P133 | 2 | 是 | foot_l/C01_magnet_cap、foot_r/C01_magnet_cap |
| P134 | 2 | 是 | foot_l/C01_pcb_clip、foot_r/C01_pcb_clip |
| P135 | 2 | 是 | foot_l/C01_sensor_cradle、foot_r/C01_sensor_cradle |
| P136 | 2 | 是 | foot_l/C02_magnet_seat、foot_r/C02_magnet_seat |
| P137 | 2 | 是 | foot_l/C02_magnet_cap、foot_r/C02_magnet_cap |
| P138 | 2 | 是 | foot_l/C02_pcb_clip、foot_r/C02_pcb_clip |
| P139 | 2 | 是 | foot_l/C02_sensor_cradle、foot_r/C02_sensor_cradle |
| P140 | 2 | 是 | clavicle_l.protract/pcb_clip、hand_l.deviate/pcb_clip |
| P141 | 2 | 是 | clavicle_l.protract/sensor_cradle、hand_l.deviate/sensor_cradle |
| P142 | 2 | 是 | clavicle_l.protract/base_service_half、hand_l.deviate/base_service_half |
| P143 | 2 | 是 | clavicle_l.protract/magnet_cap、hand_l.deviate/magnet_cap |
| P144 | 2 | 是 | clavicle_l.protract/magnet_seat、hand_l.deviate/magnet_seat |
| P145 | 6 | 是 | clavicle_l.elevate/pcb_clip、elbow_l.flex/pcb_clip、hand_l.flex/pcb_clip、elbow_r.flex/pcb_clip、hand_r.flex/pcb_clip、hand_r.deviate/pcb_clip |
| P146 | 6 | 是 | clavicle_l.elevate/sensor_cradle、elbow_l.flex/sensor_cradle、hand_l.flex/sensor_cradle、elbow_r.flex/sensor_cradle、hand_r.flex/sensor_cradle、hand_r.deviate/sensor_cradle |
| P147 | 6 | 是 | clavicle_l.elevate/base_service_half、elbow_l.flex/base_service_half、hand_l.flex/base_service_half、elbow_r.flex/base_service_half、hand_r.flex/base_service_half、hand_r.deviate/base_service_half |
| P148 | 6 | 是 | clavicle_l.elevate/magnet_cap、elbow_l.flex/magnet_cap、hand_l.flex/magnet_cap、elbow_r.flex/magnet_cap、hand_r.flex/magnet_cap、hand_r.deviate/magnet_cap |
| P149 | 6 | 是 | clavicle_l.elevate/magnet_seat、elbow_l.flex/magnet_seat、hand_l.flex/magnet_seat、elbow_r.flex/magnet_seat、hand_r.flex/magnet_seat、hand_r.deviate/magnet_seat |
| P150 | 1 | 是 | forearm_l.twist/pcb_clip |
| P151 | 1 | 是 | forearm_l.twist/sensor_cradle |
| P152 | 1 | 是 | forearm_l.twist/base_service_half |
| P153 | 1 | 是 | forearm_l.twist/magnet_cap |
| P154 | 1 | 是 | forearm_l.twist/magnet_seat |
| P155 | 2 | 是 | calf_l.flex/pcb_clip、calf_r.flex/pcb_clip |
| P156 | 2 | 是 | calf_l.flex/sensor_cradle、calf_r.flex/sensor_cradle |
| P157 | 2 | 是 | calf_l.flex/base_service_half、calf_r.flex/base_service_half |
| P158 | 2 | 是 | calf_l.flex/magnet_cap、calf_r.flex/magnet_cap |
| P159 | 2 | 是 | calf_l.flex/magnet_seat、calf_r.flex/magnet_seat |
| P160 | 2 | 是 | ball_l.flex/pcb_clip、ball_r.flex/pcb_clip |
| P161 | 1 | 是 | ball_l.flex/sensor_cradle |
| P162 | 1 | 是 | ball_l.flex/base_service_half |
| P163 | 1 | 是 | ball_l.flex/magnet_cap |
| P164 | 1 | 是 | ball_l.flex/magnet_seat |
| P165 | 1 | 是 | clavicle_r.protract/pcb_clip |
| P166 | 1 | 是 | clavicle_r.protract/sensor_cradle |
| P167 | 1 | 是 | clavicle_r.protract/base_service_half |
| P168 | 1 | 是 | clavicle_r.protract/magnet_cap |
| P169 | 1 | 是 | clavicle_r.protract/magnet_seat |
| P170 | 1 | 是 | clavicle_r.elevate/pcb_clip |
| P171 | 1 | 是 | clavicle_r.elevate/sensor_cradle |
| P172 | 1 | 是 | clavicle_r.elevate/base_service_half |
| P173 | 1 | 是 | clavicle_r.elevate/magnet_cap |
| P174 | 1 | 是 | clavicle_r.elevate/magnet_seat |
| P175 | 1 | 是 | forearm_r.twist/pcb_clip |
| P176 | 1 | 是 | forearm_r.twist/sensor_cradle |
| P177 | 1 | 是 | forearm_r.twist/base_service_half |
| P178 | 1 | 是 | forearm_r.twist/magnet_cap |
| P179 | 1 | 是 | forearm_r.twist/magnet_seat |
| P180 | 1 | 是 | ball_r.flex/sensor_cradle |
| P181 | 1 | 是 | ball_r.flex/base_service_half |
| P182 | 1 | 是 | ball_r.flex/magnet_cap |
| P183 | 1 | 是 | ball_r.flex/magnet_seat |
| P212 | 1 | 是 | frame/ball_r |
| P213 | 1 | 是 | frame/hand_r |
| P214 | 1 | 是 | frame/hand_r.flex_frame |
| P215 | 1 | 是 | frame/forearm_r |
| P216 | 1 | 是 | frame/elbow_r |
| P217 | 1 | 是 | frame/clavicle_r.protract_frame |
| P218 | 1 | 是 | frame/ball_l |
| P219 | 1 | 是 | frame/hand_l |
| P220 | 1 | 是 | frame/hand_l.flex_frame |
| P221 | 1 | 是 | frame/forearm_l |
| P222 | 1 | 是 | frame/elbow_l |
| P223 | 1 | 是 | frame/clavicle_l.protract_frame |
| P224 | 1 | 是 | frame/foot_r |
| P225 | 1 | 是 | frame/calf_r |
| P226 | 1 | 是 | frame/foot_l |
| P227 | 1 | 是 | frame/calf_l |
| P228 | 1 | 是 | frame/thigh_r |
| P229 | 1 | 是 | frame/thigh_l |
| P230 | 1 | 是 | frame/upperarm_r |
| P231 | 1 | 是 | frame/clavicle_r |
| P232 | 1 | 是 | frame/upperarm_l |
| P233 | 1 | 是 | frame/clavicle_l |
| P234 | 1 | 是 | frame/head |
| P235 | 1 | 是 | frame/chest |
| P236 | 1 | 是 | frame/waist |
| P237 | 1 | 是 | frame/pelvis |
| P238 | 1 | 是 | accessory/chest/controller_lid |
| P239 | 1 | 是 | accessory/pelvis/battery_cap |
| P240 | 1 | 是 | fixture/gateway_base |
| P241 | 1 | 按实际切片复核 | fixture/gateway_lid |
| P242 | 1 | 按实际切片复核 | fixture/xiao_spacing_gauge |
