fukukawa89/PoseDollLab_Design/Hardware/PoseDoll44/bench/revO22/manufacturing/RFQ.zh-CN.md

# O22 询价与首件加工要求

请按**一套**报价：已有打印机，用户自行打印和机械总装；电子SMT、所有板端焊接、端子压接、标号与导通检测均由供应方完成。不要要求用户自己焊48根尾线。此包用于询价和首件，尚未放行整机批量生产。

## 文件与数量

- `electronic_bom.json/tsv`、两块板的Gerber/钻孔/坐标及`../electronics/`原理图和原生PCB为配套数据。最终原生板散列在BOM内，禁止把旧两层载板当本版加工。
- 传感裸板按50张订单核价，装48张：46张使用、2张完整备件。MT6701CT-STD-R采购50颗，余2颗用于贴片损耗或留料；不要重复计费。
- 中央板80×94mm、四层、1.6mm；按5张裸板最小订单核价，仅装1张。外层35µm，内层17.5µm；先报该层叠和最小0.15mm线宽间距是否可做。
- MCU为XIAO ESP32S3普通版1块，不需摄像头。两排针中心距15.24mm，PCB间距4.0mm，定位焊接后再装入背盒。
- 46个BM05B-SRSS-TB插座；48套SHR-05V-S插头，压接SSH-003T-P0.2-H。原厂整卷包装量不能自动按最低购买量收费；明确零切/代采MOQ和余料归属。
- 线束按`../harness/routing_plan.json`逐路标号，46路每色22.75m，另有2套750mm备件；报价再计10%下料损耗，即每色约26.68m、五色约133.38m。末端确认后才锁定生产长度。单根AWG30铜线，外径0.4–0.7mm，测试温度下导体电阻≤0.4Ω/m；5根分立柔线，不用厚硬整排排线。
- 传感PCB尺寸12×10×1mm；所有器件朝磁铁一面。SOP8本体/焊脚尺寸和极性按原理图及贴片图；器件加焊料最大高度1.85mm。板上旧网络名`+3V3`表示VDD脚，本版实际受控电源为SENSOR_3V45，不能另接外部3.3/5V。

## 不可省略的加工细节

传感板五个焊盘按GND、VDD、CLK、DO、CSN顺序。厂内完成焊线、套管/柔性胶应力释放与导通测试；胶不得爬到PCB导轨、封装顶面或磁铁间隙。线材离板后沿+Y出口出线；保留自由弯曲段，运动骨段处做U环。用可返修的电子级中性柔性固线材料，不用硬环氧锁死弯折点。首件先完成2N、10秒的线束轻拉筛选，焊点不得受剥离力；最终工艺按端子厂规范和实测结果确认。

R50=Vishay TNPW0603316KBEEA，R51=TNPW060366K5BEEA。C7/C8/C9候选Murata GRM21BR61A226ME51L；必须返回偏压曲线并证明C7在4.1V有效容量≥10µF，C8+C9在3.45V合计≥20µF；若该料号不满足，退回等封装候选供核对，不得仅以标称22µF代换。其他被动元件返回制造商完整AVL、容差、额定电压和介质。输出保险丝0467001.NR不可任意改成PTC；其≤0.15Ω热态要求需在实装首件上验证。

外部5V适配器额定2A，满载到适配器出口仍≥4.9V，输入线压降≤0.08V；U7引脚满载≥4.05V。外部5V与USB VBUS分开，XIAO的5V引脚不焊接到传感5V网。不得依靠电脑USB口给所有传感器供电。上电检测只做受控首件流程，不宣称由ERC/DRC保证电气性能。

## 回价格式和1500元判定

填`quote_response_EMPTY.json`，提供供应商、日期、有效期、税额、运费、PCB最小订单、损耗、钢网/工程费、SMT、手焊、压接、标号与电测。报价不足最小订单时按实际支付金额入账；余下4张中央裸板也计成本。芯片/贴片、中央板/电源、线束/板端焊接不得重复计费。

目标分配：芯片362.50；传感PCB与SMT180；中央四层板及信号元件150；XIAO55；电源35；五金215；磁铁45；线束180；打印材料80；适配器/数据线/杂件/运费100；预留80。合计1482.50元。以上是预算分配，没有供应商承诺。计量夹具的借用或购置费用若发生，纳入实际到手成本，不隐去必要支出。

`python ../source/check_quotes.py quote_response_EMPTY.json`只核算已填实际金额；空项不会按0元通过。当前高价情景2220元。最敏感项为肩轴标准件、传感板小批工程费、46路原厂端子与人工线束；超预算时优先合单加工、减少最低收费和重复运费，不能删测量轴、去掉有效校验或偷偷换未验证器件。
