fukukawa89/PoseDollLab_Design/Hardware/PoseDoll44/tutorials/tut-prototype/assets/o8-fit-handoff/START_HERE.zh-CN.md

# 首批只做 A_first_fit

A_first_fit 中 4 类文件：hole_gauge_Z 1 件、hole_gauge_Y 1 件、pin_D4 3 件、fastener_gauge 1 件，共 6 件。STL 与 STEP 是同一零件的两种格式，不要重复计数。单位 mm。

候选为同批未填充 PA12、SLS，不涂装、不润滑。先让打印方确认材料、孔径与方向要求并报价。B_core_reference 不计入首批订单。

另配 M1.6×6 / 0.35 螺距内六角圆柱头螺钉与 M1.6 六角螺母各 6 件、1.5 mm 内六角工具。实际规格要核对。它们是金属标准件，不是 3D 打印。

先拍照、记录批次与打印方向。从缺口端开始编号，用三根轴逐一轻试五个孔，记录进不去、卡、轻转、明显晃动。螺母既要能放入，也不能跟着螺钉空转。不要敲入、先打磨、先润滑或把试片结果当成整关节合格。

详细说明在 TEST_INSTRUCTIONS.zh-CN.md；有些来源链接指向设计仓库。measurement_template.json 为空白记录，不懂 JSON 时可直接用照片与文字回传。dimensions.svg 是按 CAD 参数绘制的识别图，不能打印后当量尺。

B_core_reference 是 O8 局部研究改型，包含两个各加长 2 mm 的叉架和上下半环；等待配合结果后再推进其制作。没有完整外接机构、PCB、线束或测矩夹具，没有实测承载与制造放行。
