fukukawa89/PoseDollLab_Design/Hardware/PoseDoll44/tutorials/tut-prototype/assets/o8-fit-handoff/B_core_reference/SOURCE.md

Derived research geometry from https://github.com/oliglauser/atamid/tree/9a152b1d82374d1960ebd2216563fb30b1b6875b/Hardware/Mechanics . Original jointTUT.stl SHA256: 05bc819a65068a68afdb275a639b267ba840d8e2f574fd21368b655a3bf570e0 . Source license / production redistribution terms not verified. Four central parts only; fork stems extended 2 mm each. No physical performance or full assembly qualification.
