fukukawa89/PoseDollLab_Design/Hardware/PoseDoll44/bench/revO14/verification/o14-guide-mobile.png

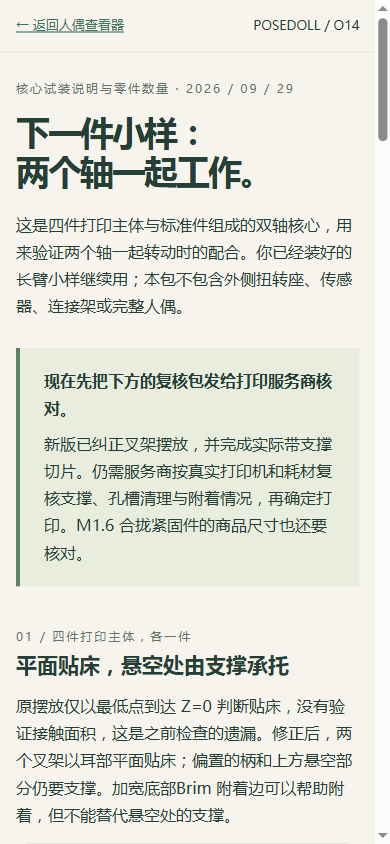
Hardware/PoseDoll44/bench/revO14/verification/o14-guide-mobile.png
