fukukawa89/PoseDollLab_Design/Hardware/PoseDoll44/bench/revO14/verification/o14-print-supports.png

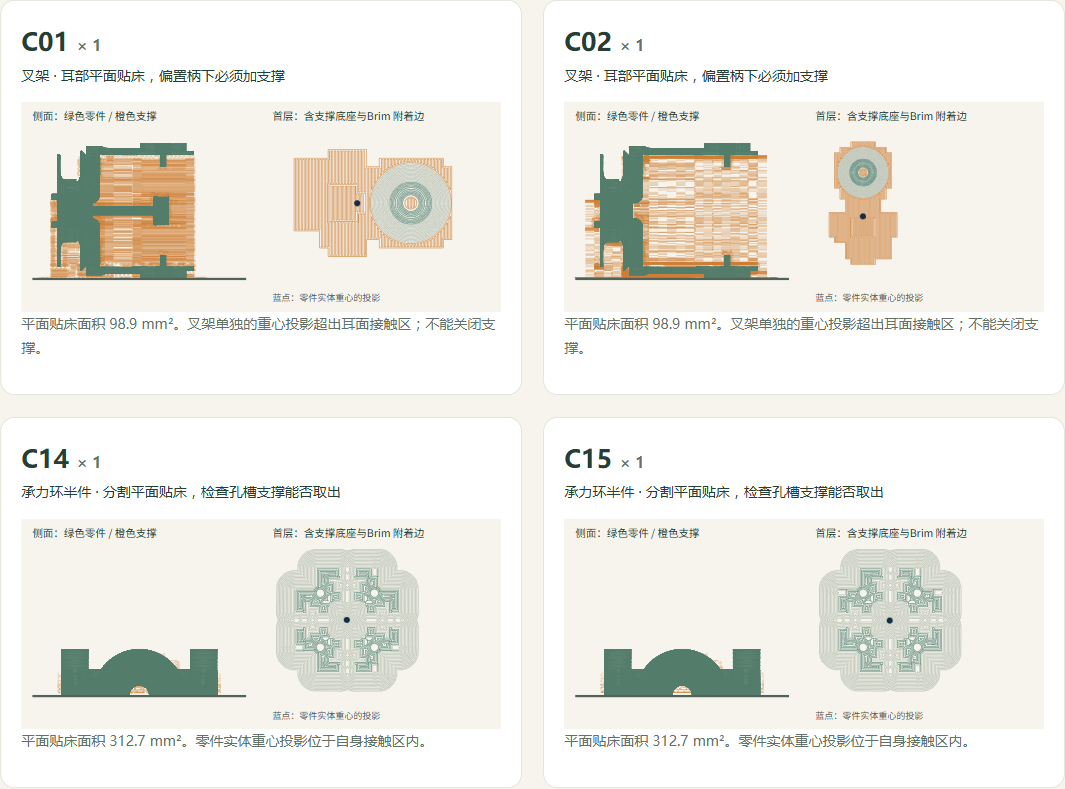
Hardware/PoseDoll44/bench/revO14/verification/o14-print-supports.png
