fukukawa89/PoseDollLab_Design/Hardware/PoseDoll44/tutorials/design-lab/verification/bench-assembled.png

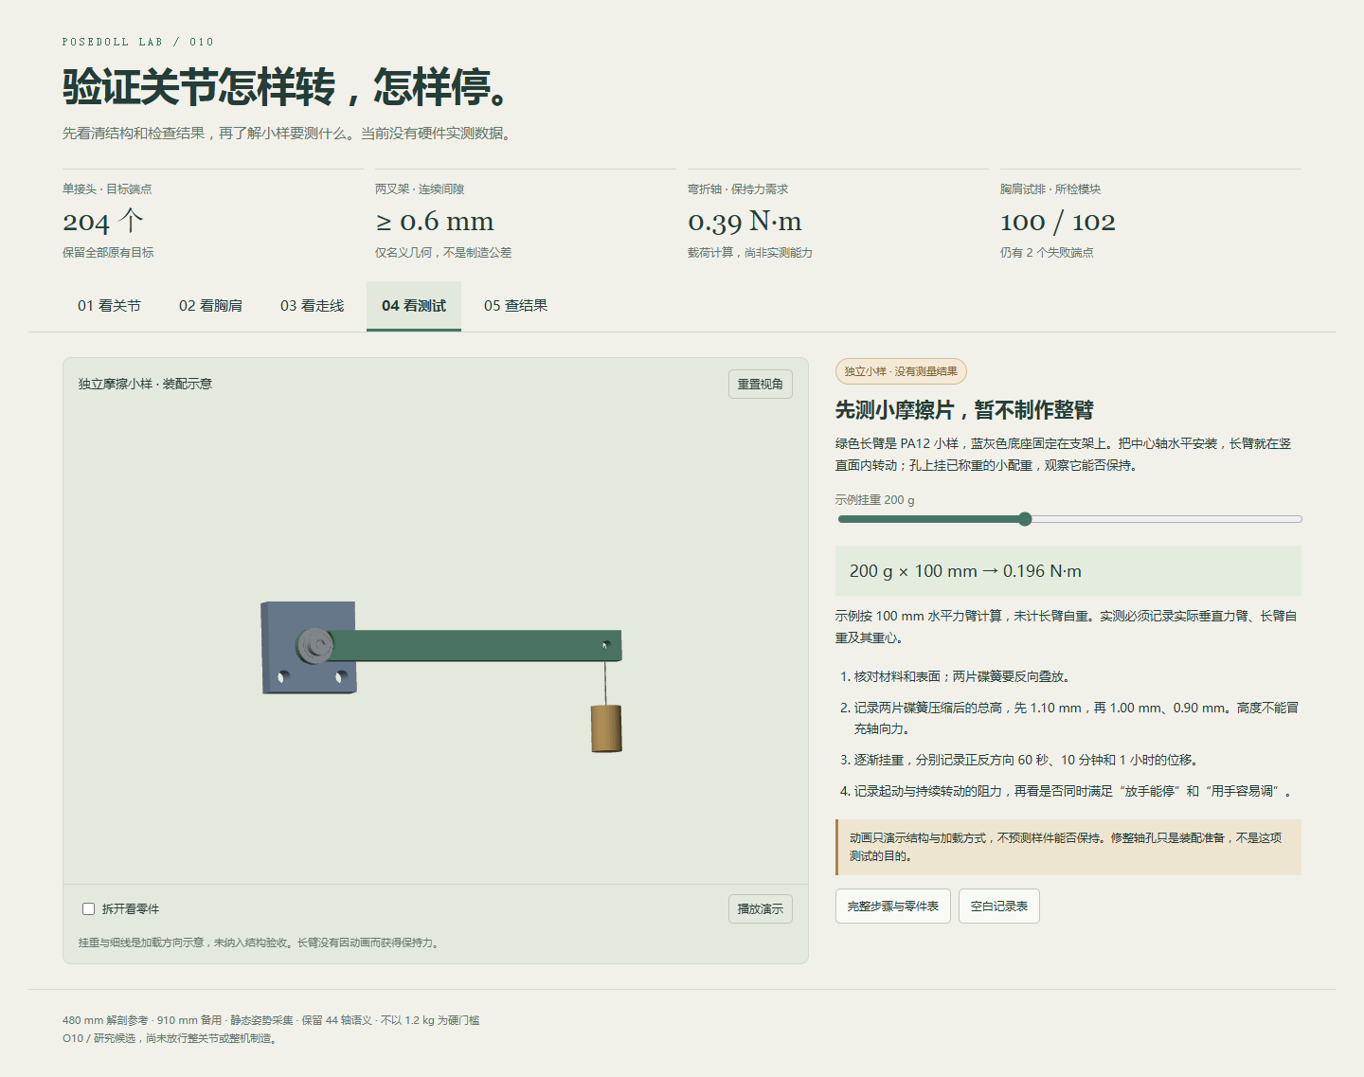
Hardware/PoseDoll44/tutorials/design-lab/verification/bench-assembled.png
