fukukawa89/PoseDollLab_Design/Hardware/PoseDoll44/tutorials/first-bench/verification/print-preview.png

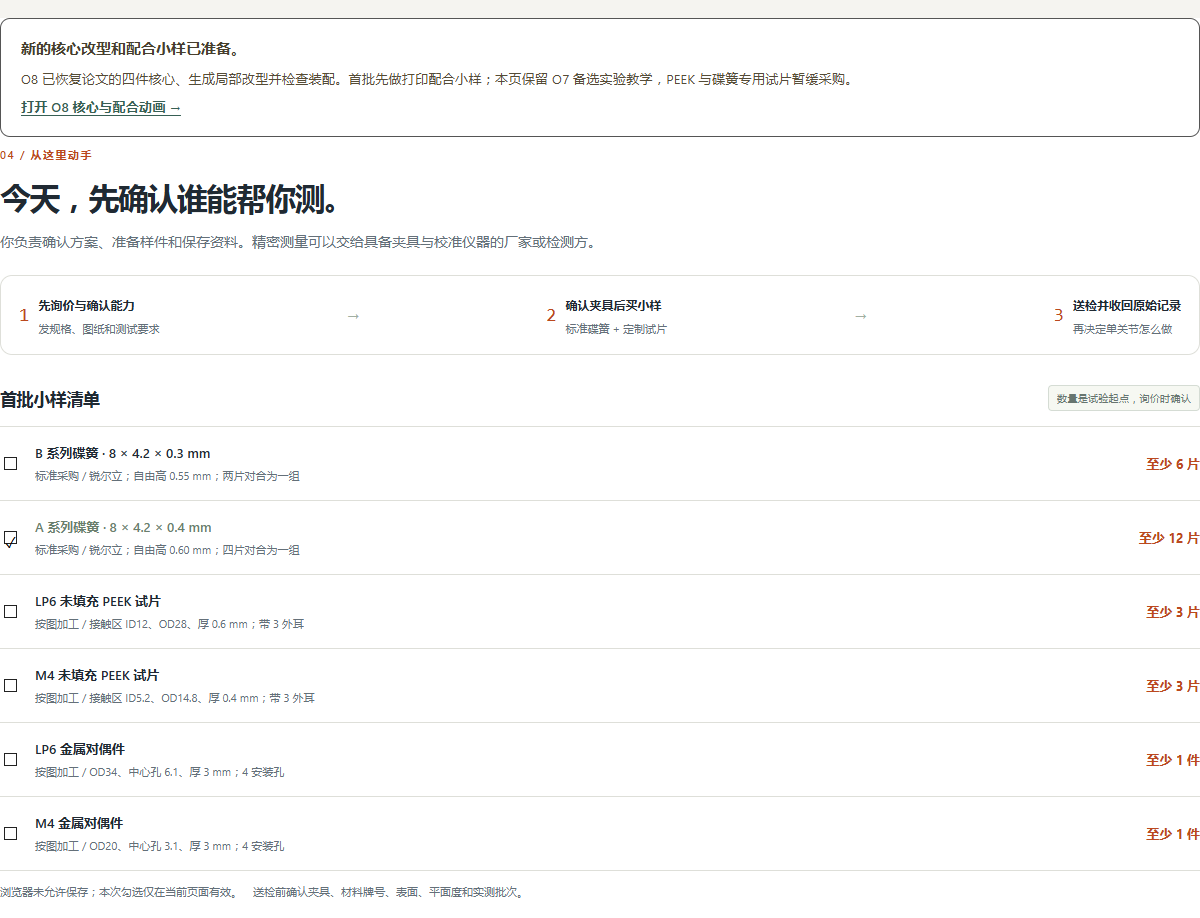
Hardware/PoseDoll44/tutorials/first-bench/verification/print-preview.png
