fukukawa89/PoseDollLab_Design/Hardware/PoseDoll44/tutorials/tut-prototype/verification/desktop-assembly.png

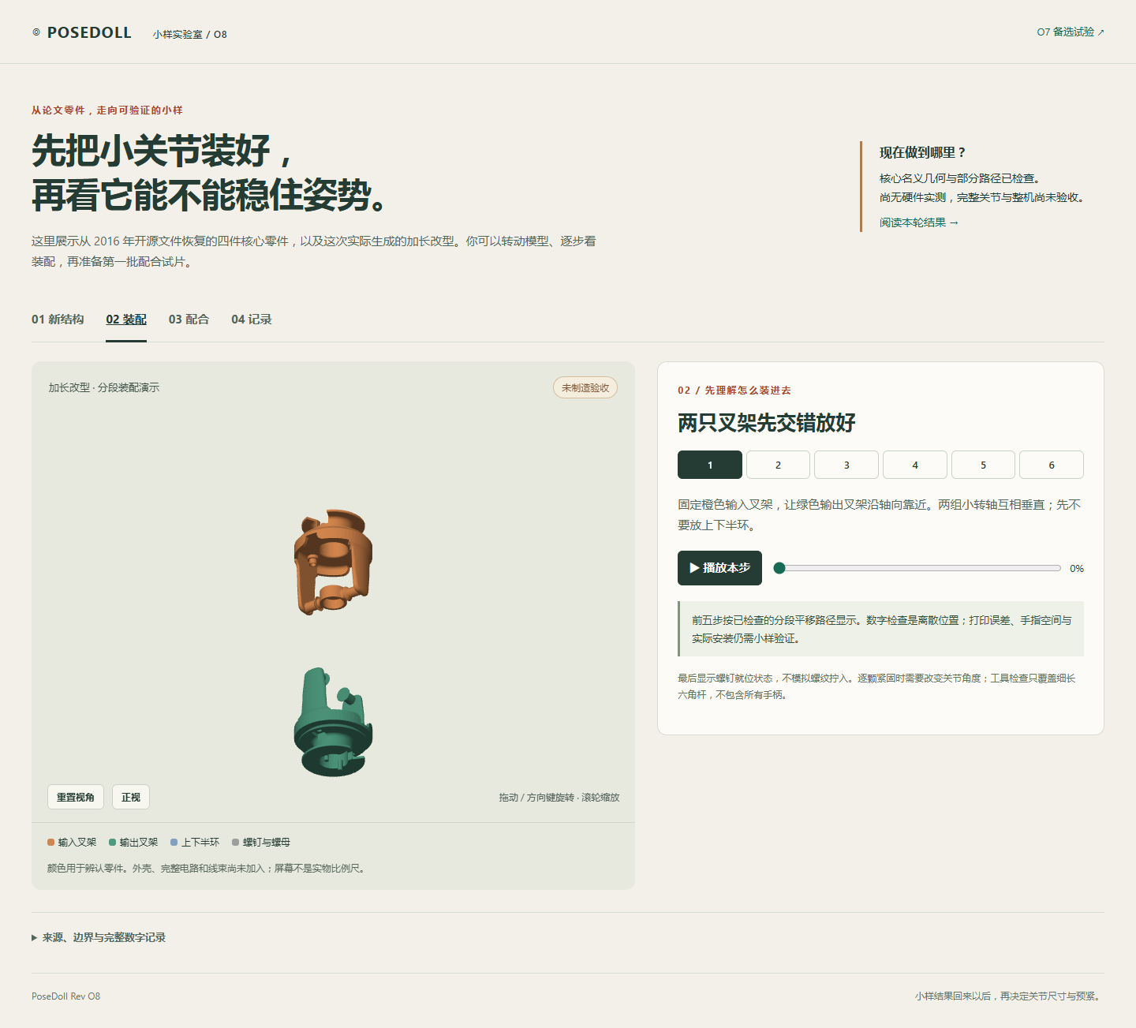
Hardware/PoseDoll44/tutorials/tut-prototype/verification/desktop-assembly.png
