fukukawa89/PoseDollLab_Design/Hardware/PoseDoll44/tutorials/tut-prototype/verification/mobile-assembly.png

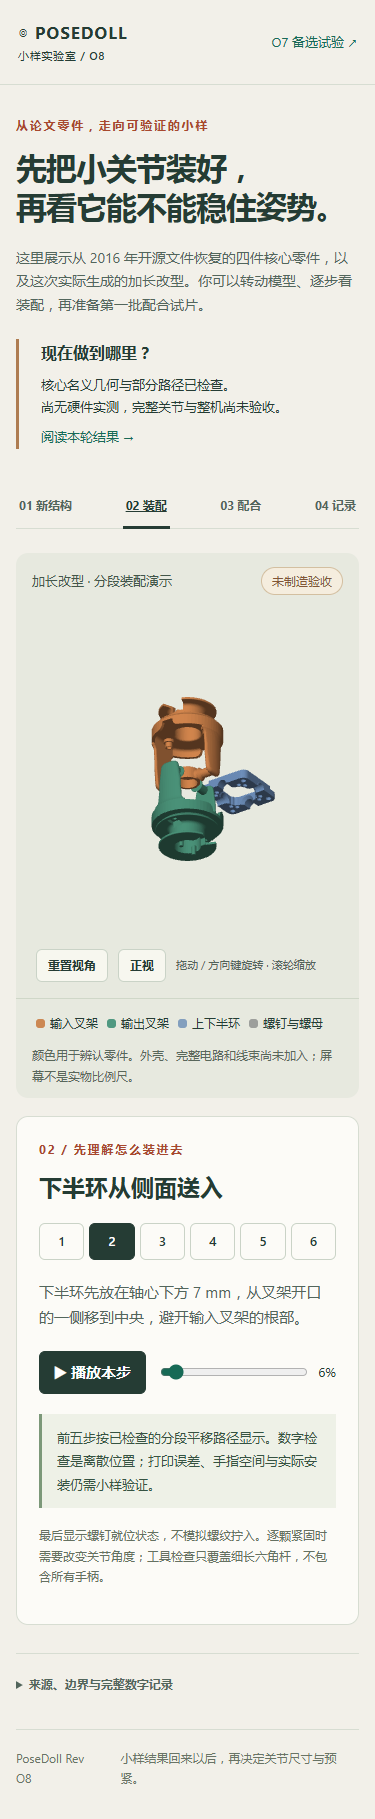
Hardware/PoseDoll44/tutorials/tut-prototype/verification/mobile-assembly.png
