fukukawa89/PoseDollLab_Design/Hardware/PoseDoll44/bench/revO22/verification/host_tests.txt

test_bounded_fit_and_independent_validation_both_directions (test_calibration_export.CalibrationExport.test_bounded_fit_and_independent_validation_both_directions) ... ok
test_export_default_refuses_synthetic_and_preserves_rotations (test_calibration_export.CalibrationExport.test_export_default_refuses_synthetic_and_preserves_rotations) ... ok
test_fit_rejects_false_precision_incomplete_and_unstable_fixture (test_calibration_export.CalibrationExport.test_fit_rejects_false_precision_incomplete_and_unstable_fixture) ... ok
test_packet_tamper_scan_tamper_angle_tamper_rejected (test_calibration_export.CalibrationExport.test_packet_tamper_scan_tamper_angle_tamper_rejected) ... ok
test_validation_is_not_fit_resubstitution (test_calibration_export.CalibrationExport.test_validation_is_not_fit_resubstitution) ... ok
test_180_degree_quaternion (test_device.DeviceTests.test_180_degree_quaternion) ... ok
test_all46_channel_faults_rejected (test_device.DeviceTests.test_all46_channel_faults_rejected) ... ok
test_analytic_noncommuting_rotations (test_device.DeviceTests.test_analytic_noncommuting_rotations) ... ok
test_cad_pose_regression (test_device.DeviceTests.test_cad_pose_regression) ... ok
test_calibration_rejected (test_device.DeviceTests.test_calibration_rejected) ... ok
test_identity_and_replay (test_device.DeviceTests.test_identity_and_replay) ... ok
test_missing_raw_never_defaults_to_zero (test_device.DeviceTests.test_missing_raw_never_defaults_to_zero) ... ok
test_motion_window_and_scan_skew (test_device.DeviceTests.test_motion_window_and_scan_skew) ... ok
test_random_raw_combinations_proper_rotations (test_device.DeviceTests.test_random_raw_combinations_proper_rotations) ... ok
test_short_window_and_gap (test_device.DeviceTests.test_short_window_and_gap) ... ok
test_single_hardware_and_no_missing_axis (test_device.DeviceTests.test_single_hardware_and_no_missing_axis) ... ok
test_stable_capture_keeps_raw_and_calibration (test_device.DeviceTests.test_stable_capture_keeps_raw_and_calibration) ... ok
test_stale_window_and_wrong_request (test_device.DeviceTests.test_stale_window_and_wrong_request) ... ok
test_synthetic_never_qualifies_as_hardware (test_device.DeviceTests.test_synthetic_never_qualifies_as_hardware) ... ok
test_wrap_and_calibrated_sign (test_device.DeviceTests.test_wrap_and_calibrated_sign) ... ok
test_empty_prices_are_not_zero_and_overrun_is_reported (test_evidence_workflow.EvidenceWorkflow.test_empty_prices_are_not_zero_and_overrun_is_reported) ... ok
test_incomplete_physical_tests_cannot_become_qualified (test_evidence_workflow.EvidenceWorkflow.test_incomplete_physical_tests_cannot_become_qualified) ... ok
test_missing_axis_or_synthetic_calibration_rejected (test_evidence_workflow.EvidenceWorkflow.test_missing_axis_or_synthetic_calibration_rejected) ... ok
test_binding_46_no_duplicates (test_o21.O21.test_binding_46_no_duplicates) ... ok
test_budget_allocation_is_not_a_quote (test_o21.O21.test_budget_allocation_is_not_a_quote) ... ok
test_c_fixture_and_all_packet_bits (test_o21.O21.test_c_fixture_and_all_packet_bits) ... ok
test_capture_does_not_qualify_unmeasured_hardware (test_o21.O21.test_capture_does_not_qualify_unmeasured_hardware) ... ok
test_lut_circle_and_reject_fold_nan (test_o21.O21.test_lut_circle_and_reject_fold_nan) ... ok
test_replay_boot_and_all46_faults (test_o21.O21.test_replay_boot_and_all46_faults) ... ok
test_unchanged_geometric_mapping (test_o21.O21.test_unchanged_geometric_mapping) ... ok
test_valid_zero_not_confused_with_stuck_low (test_o21.O21.test_valid_zero_not_confused_with_stuck_low) ... ok
test_a_pose_margin_and_unchanged_reference (test_o22.O22.test_a_pose_margin_and_unchanged_reference) ... ok
test_ambiguous_turn_not_accepted_by_tolerance (test_o22.O22.test_ambiguous_turn_not_accepted_by_tolerance) ... ok
test_bounded_lut_wrap_no_extrapolation_and_zero_corrected (test_o22.O22.test_bounded_lut_wrap_no_extrapolation_and_zero_corrected) ... ok
test_final_age_is_total_not_two_independent_intervals (test_o22.O22.test_final_age_is_total_not_two_independent_intervals) ... ok
test_measured_calibration_cannot_borrow_synthetic_bound (test_o22.O22.test_measured_calibration_cannot_borrow_synthetic_bound) ... ok
test_most_recent_scan_uses_earliest_channel (test_o22.O22.test_most_recent_scan_uses_earliest_channel) ... ok
test_one_and_multiple_counts_at_each_limit_preserved (test_o22.O22.test_one_and_multiple_counts_at_each_limit_preserved) ... ok
test_real_overrun_and_uncertainty_cap_rejected (test_o22.O22.test_real_overrun_and_uncertainty_cap_rejected) ... ok

----------------------------------------------------------------------
Ran 39 tests in 3.109s

OK
