fukukawa89/PoseDollLab_Design/Hardware/PoseDoll44/generated/revO12/runs/o12_20260926_r1/page_verification/o12-browser-result.txt

{"status":"PASS","errors":[],"partOptions":16,"nonBackgroundPixels":16748,"mobile":{"width":390,"scrollWidth":390},"downloadFilename":"O12_taobao_bench.3mf","responses":[{"url":"http://127.0.0.1:8769/tutorials/design-lab/index.html","status":200},{"url":"http://127.0.0.1:8769/bench/revO12/print_beds/O12_taobao_bench.3mf","status":200},{"url":"http://127.0.0.1:8769/bench/revO12/README.zh-CN.md","status":200},{"url":"http://127.0.0.1:8769/docs/O12_TAOBAO_ADAPTATION.zh-CN.md","status":200},{"url":"http://127.0.0.1:8769/bench/revO12/measurement_template.json","status":200}],"checks":["15 part meshes","6 mm screw and 3 mm key label","native explosion slider","animation advance and pause","nonblank WebGL","3MF download","local links","mobile layout"],"physical_tested":false}
