fukukawa89/PoseDollLab_Design/Hardware/PoseDoll44/tutorials/first-bench/verification/README.zh-CN.md

# 页面验收记录

日期：2026-09-25。对象：本目录的前端教学指南，不是硬件实测。

- Chrome 实际渲染 6 个不同的零件模型；其中 4 个网格来自 O7 STEP，2 个碟簧按目录尺寸建模。
- 20 种「实验类型 / 尺寸组合 / 步骤」视图检查；实际播放会改变动画，暂停保持进度，滑块可定位。
- 390 / 768 / 1024 / 1440 px 下 5 个章节无页面横向溢出；手机俯视、侧视图上下排列。
- 可编辑询价说明在切换联系人时保留本次修改；采购清单在同一浏览器来源下刷新后保留。
- 自动复制成功与权限受限时的手动复制弹窗均检查；实际 ZIP 下载与本地链接通过。
- file:// 离线直接打开通过；禁用存储时有降级提示；默认暂停，减少动态效果设置下不自动播放。
- 打印样式已通过浏览器截图检查。
- 页面资产 9 个原始输入哈希与 ZIP 12 个文件逐一核对一致。
- 原 O7 已封存交付物的 548 项哈希核验通过，没有修改旧设计与实测模板。

详细结果见 browser-checks.json；截图包含桌面零件、两套动画、送检、结果页和手机布局。图像人工复核后调整了手机图解布局、中心导向文字与卸载箭头。

当前不具备实测数据；动画不包含真实力学求解，图中台架是原理示意。UI 验收不改变单关节、整机或制造放行状态。
