fukukawa89/PoseDollLab_Design/Hardware/PoseDoll44/bench/revO15/BATCH_VALIDATION_PLAN.zh-CN.md

# O15：最后一批实物验证顺序（准备稿）

目前不据此下单。整机几何、统一打印包与带线检查完成后，这份顺序会与最终零件编号和数量一起交付。现有长臂小样保留，不要求再做一批相同的小样。

设计输入：用户已经确认 O12 小样的打印配合和初步手感可用；整机新关节的效果暂按可用推进。这里的“待测”项目不会阻止继续完成数字设计，也不会被登记成已经实测通过。

| 顺序 | 使用最终批次中的哪些零件 | 怎么做 | 记录什么 | 结果用来决定什么 |
|---|---|---|---|---|
| 1 | 标准螺钉、螺母、垫圈、碟簧 | 对照最终图纸量直径和厚度；用手检查垫圈能否穿过相应光杆/螺纹 | 实际尺寸、商品型号、批次 | 核实供应件与数字模型一致 |
| 2 | 打印件 | 对照编号清点，去掉支撑，检查孔口、承压面和捕获螺母的槽 | 实际材料、机型、喷嘴、层高、照片 | 定位服务商工艺导致的装配问题 |
| 3 | 一个单轴关节和一个双轴核心 | 先不装传感板，按动画装好标准件；小幅调整预紧；分别转动两个轴 | 最松/最紧位置的手感、是否卡住、调整一轴是否影响另一轴 | 验证金属堆叠、打印承压和双轴配合；不只是量孔径 |
| 4 | 一个端部扭转模块 | 检查分体外壳合拢、轴向保持和径向摩擦块；在规定范围内来回转动 | 松动、卡滞、摩擦是否可调、外壳是否张开 | 验证新增的扭转与止退结构 |
| 5 | 传感小板、磁铁、压条 | 对照方向图装板、装磁铁、再拆下一次 | 板是否滑动、是否能拆出、磁铁是否被盖子挡住 | 验证保持与维护；不靠胶水掩盖缺少固定 |
| 6 | 各传感器与采集系统 | 一次只转一个物理轴，核对原始通道、方向、零位和磁场诊断；逐项断开一条连接 | 原始数据、缺失/故障状态、轴与端口的对应关系 | 完成物理绑定与标定；数字角度合成不能替代这一步 |
| 7 | 完整左/右臂及腿 | 接好线束，沿图示顺序完成相邻关节动作；检查线缆余量和插头 | 实际可达角度、线被拉紧/夹住的位置、与模型不同的接触点 | 复核相邻结构和带线运动 |
| 8 | 完整躯干、颈部、四肢 | 按最终说明总装；先手托骨盆或指定握持处，再依次放到示范姿势 | 碰撞、松脱、维护工具是否能到达 | 复核整机组合，不把局部试装等同于整机通过 |
| 9 | 整机 | 在短时间观察后逐渐延长保持时间；同一姿势可分别自保持和手托 | 起始/结束角度、持续时间、是否发生持续滑移或结构变形 | 自保持不足可以手托；结构损坏、卡滞和传感错误仍须改进 |
| 10 | 整机与 UE 插件 | 完成标定后，摆稳、采集、检查结果；再故意动一下人偶或断开一个传感器 | 一次采集是否只提交一次，故障时是否拒绝错误姿势 | 验证真正的静态采集闭环 |

## 统一记录方式

每次记录零件编号、实际材料、螺钉/碟簧规格、姿势、预紧位置、持续时间及观察。若测力，必须同时记录力的方向与离转轴的距离；只说“挂了多少克”不能确定关节承受的扭矩。

## 已有证据与这批待测的边界

- 已有：用户报告的 O12 单轴小样配合与初步手感。
- 数字工作：关节与骨架几何、通道映射、状态传播等由各自报告记录，不合并成“整机通过”。
- 这批待测：新打印承力结构、实际摩擦/磨损/长期变化、传感器磁场与标定、真实线束、完整采集链路。

最后交付将把打印文件、金属件净数量和备件数量、其他电子件、装配动画、这个验证顺序放在同一入口。
