fukukawa89/PoseDollLab_Design/Hardware/PoseDoll44/verification/revO5/runs/o5_20260924_r1/hardware_bridge_tests.txt

........................                                                 [100%]
24 passed in 0.29s
