fukukawa89/PoseDollLab_Design/Hardware/PoseDoll44/verification/revO5CN/runs/cn_20260924_r1/codec_test.txt

mt6701_trial.c
test_mt6701_trial.c
正在生成代码...
PASS: 262144 angle/status payloads; 393216 single-bit mutations; invalid lengths/nulls; all-zero cannot enable capture.
