fukukawa89/PoseDollLab_Design/Hardware/PoseDoll44/bench/revO14/verification/o14-contact-view.png

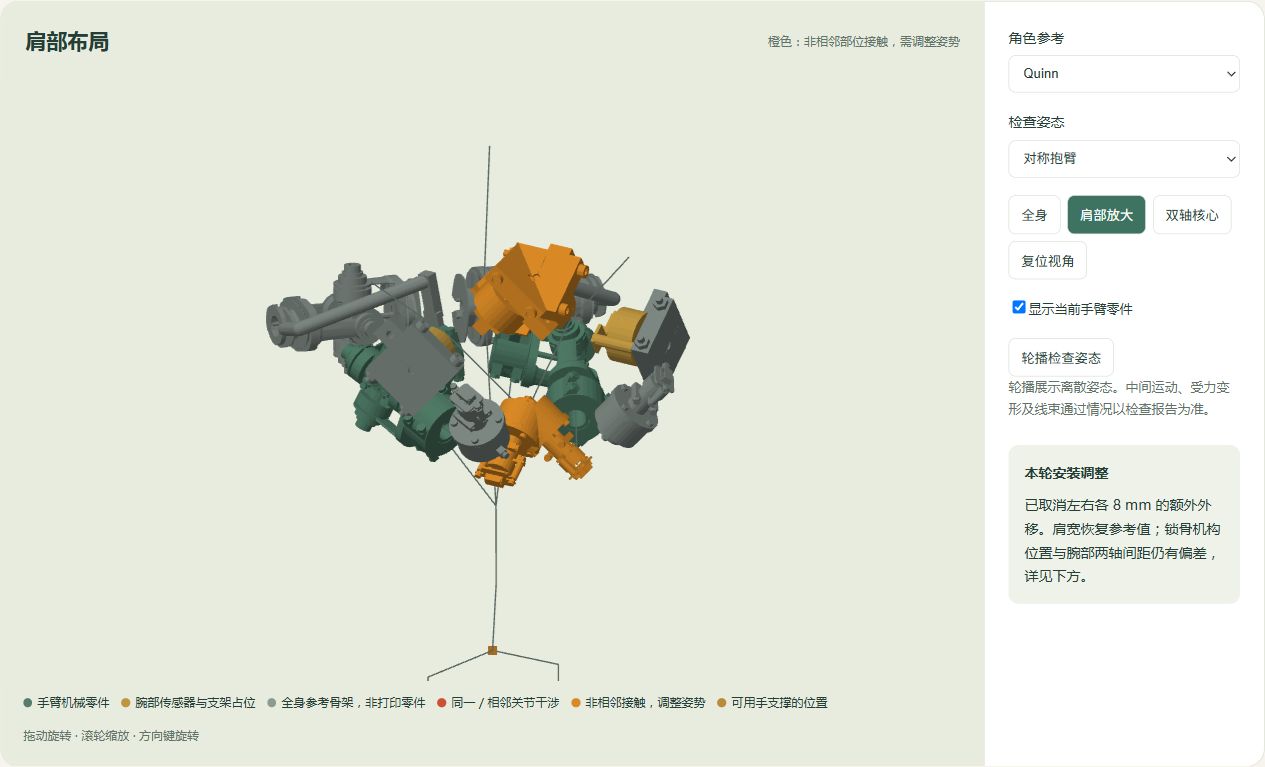
Hardware/PoseDoll44/bench/revO14/verification/o14-contact-view.png
