fukukawa89/PoseDollLab_Design/Hardware/PoseDoll44/bench/revO16/verification/arms_forward_side.png

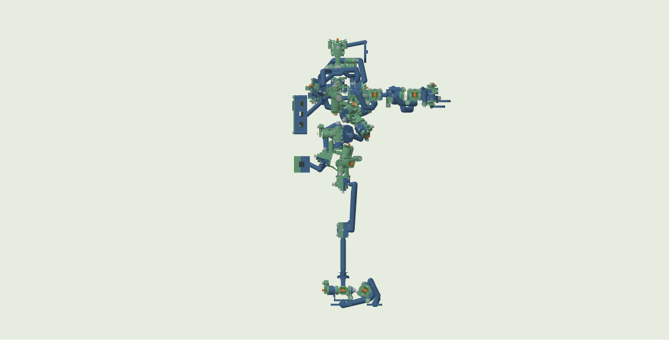
Hardware/PoseDoll44/bench/revO16/verification/arms_forward_side.png
