fukukawa89/PoseDollLab_Design/Hardware/PoseDoll44/bench/revO17/verification/magnet_cartridge.png

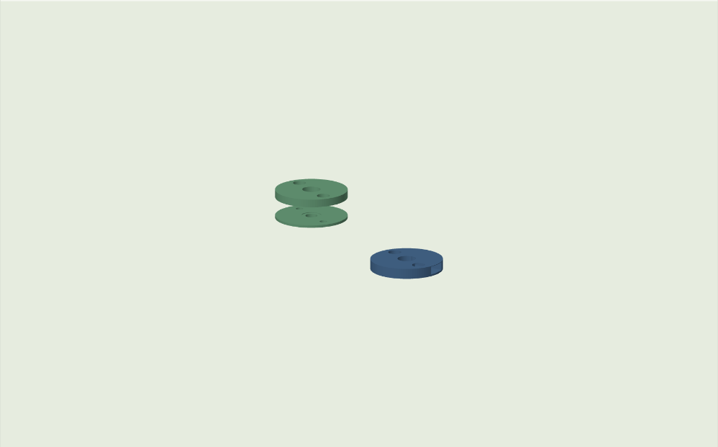
Hardware/PoseDoll44/bench/revO17/verification/magnet_cartridge.png
