fukukawa89/PoseDollLab_Design/Hardware/PoseDoll44/bench/revO18/verification/coupon.png

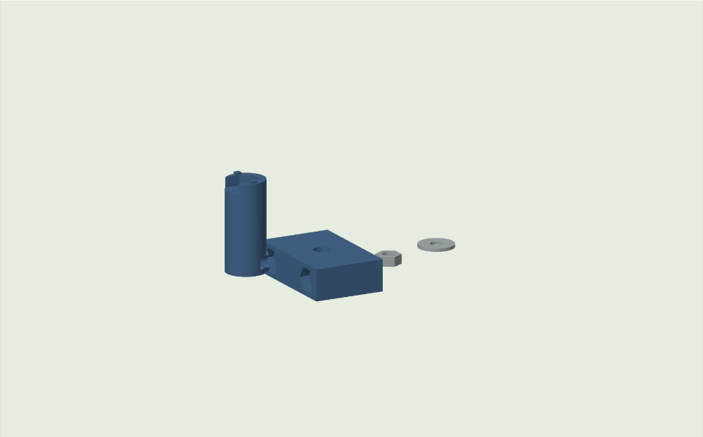
Hardware/PoseDoll44/bench/revO18/verification/coupon.png
