fukukawa89/PoseDollLab_Design/Hardware/PoseDoll44/bench/revO19/verification/interference.png

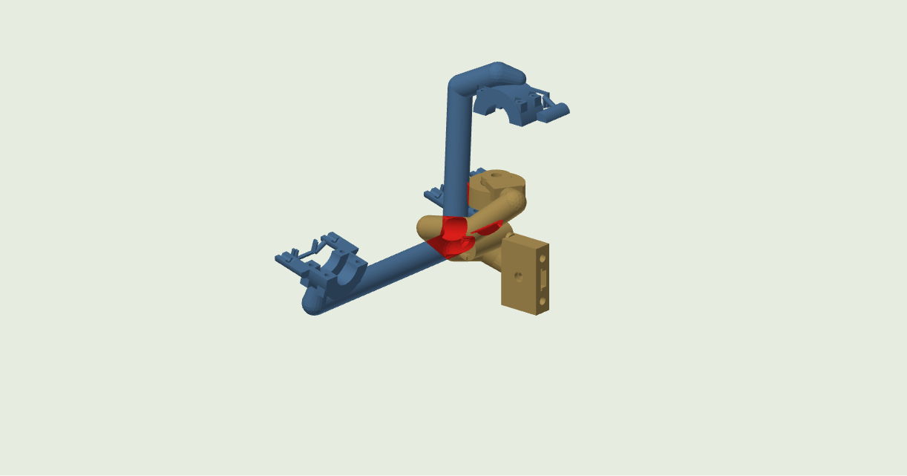
Hardware/PoseDoll44/bench/revO19/verification/interference.png
