fukukawa89/PoseDollLab_Design/Hardware/PoseDoll44/bench/revO19/verification/legs_front.png

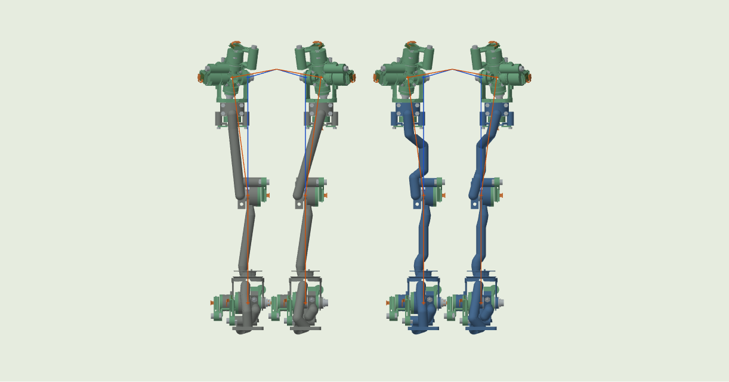
Hardware/PoseDoll44/bench/revO19/verification/legs_front.png
