fukukawa89/PoseDollLab_Design/Hardware/PoseDoll44/bench/revO19/verification/legs_side.png

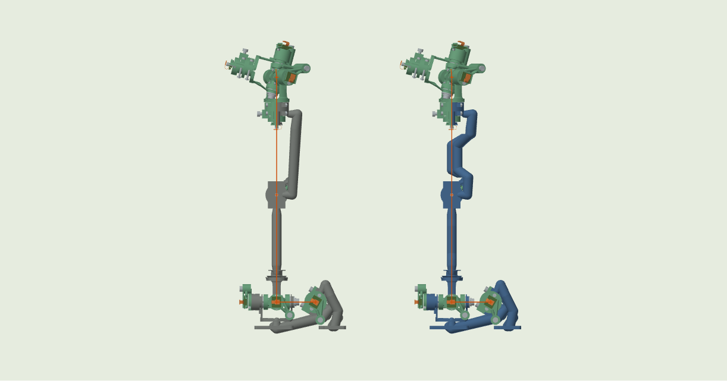
Hardware/PoseDoll44/bench/revO19/verification/legs_side.png
