fukukawa89/PoseDollLab_Design/Hardware/PoseDoll44/bench/revO20/verification/core_section.png

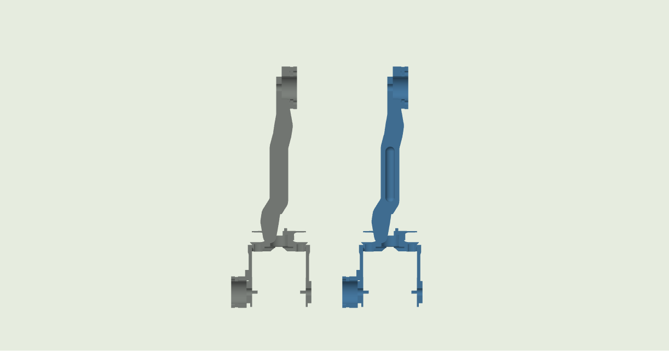
Hardware/PoseDoll44/bench/revO20/verification/core_section.png
