fukukawa89/PoseDollLab_Design/Hardware/PoseDoll44/bench/revO20/verification/lid_comparison.png

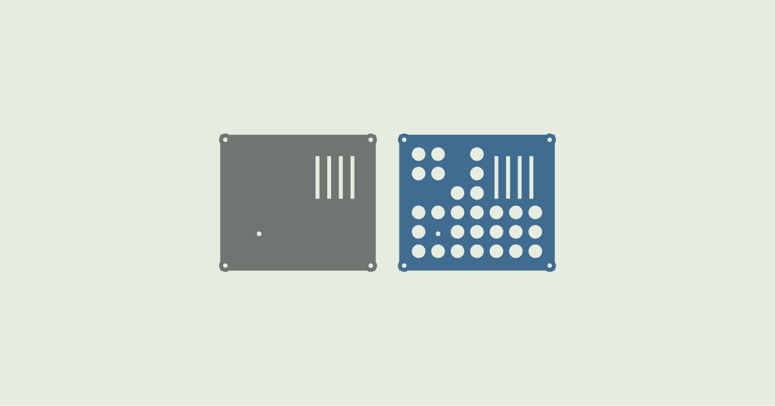
Hardware/PoseDoll44/bench/revO20/verification/lid_comparison.png
