fukukawa89/PoseDollLab_Design/Hardware/PoseDoll44/bench/revO20/verification/toe_housing.png

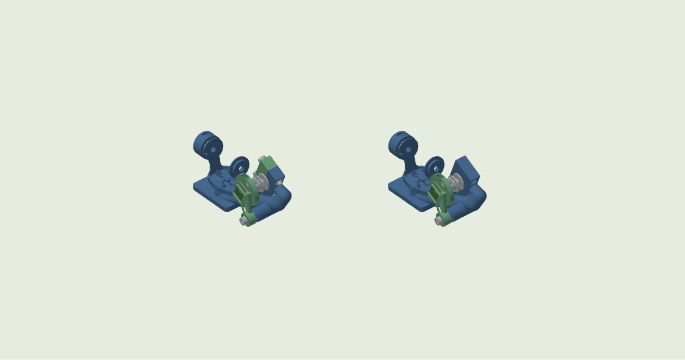
Hardware/PoseDoll44/bench/revO20/verification/toe_housing.png
