fukukawa89/PoseDollLab_Design/Hardware/PoseDoll44/bench/revO21/verification/desktop.png

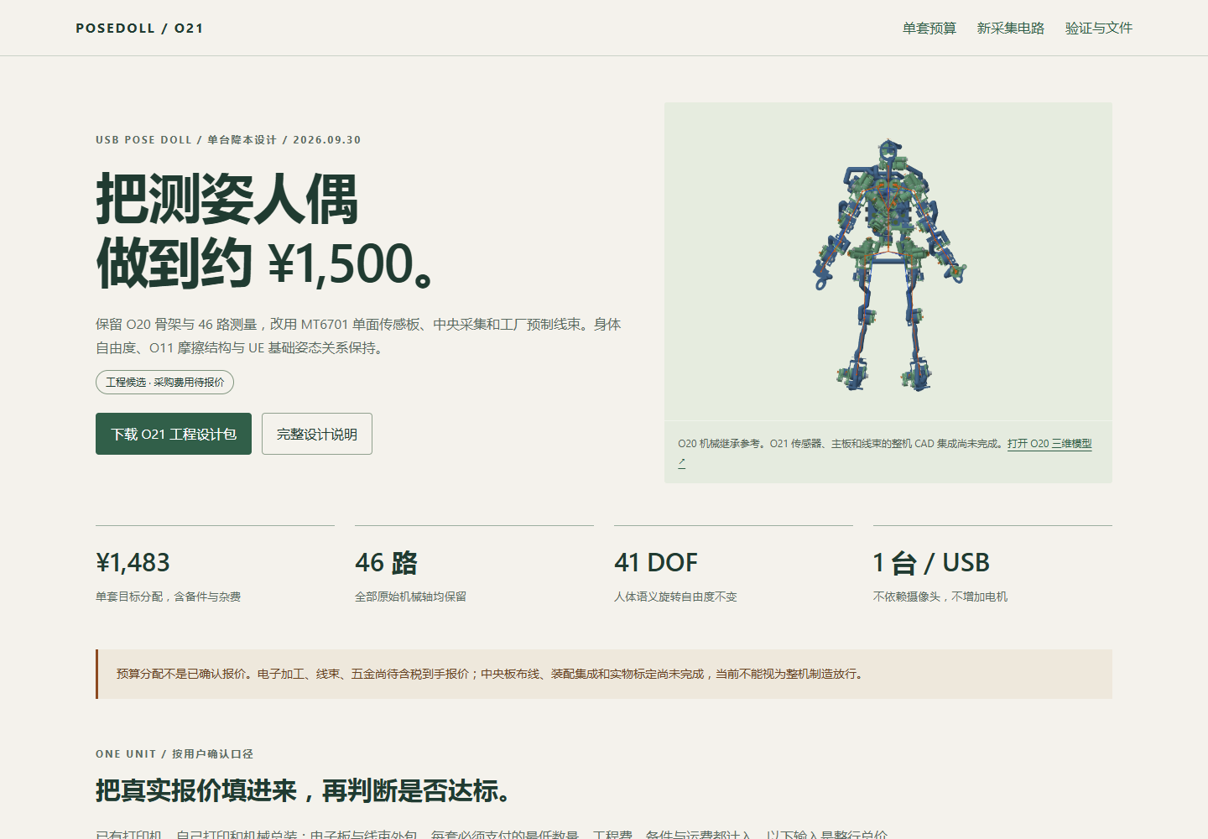
Hardware/PoseDoll44/bench/revO21/verification/desktop.png
