fukukawa89/PoseDollLab_Design/Hardware/PoseDoll44/bench/revO21/verification/mobile.png

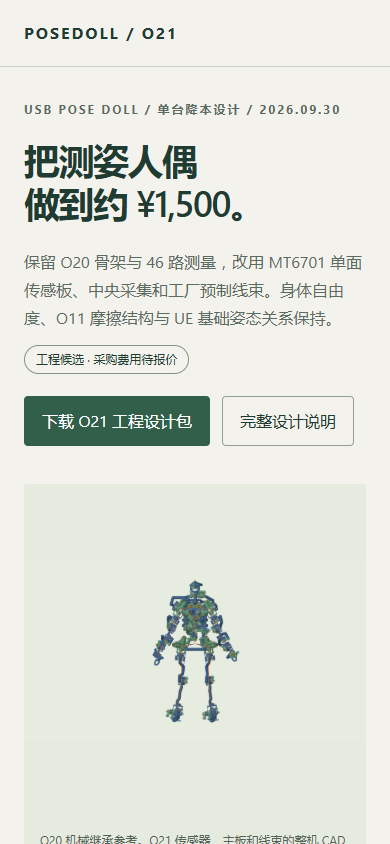
Hardware/PoseDoll44/bench/revO21/verification/mobile.png
