fukukawa89/PoseDollLab_Design/Hardware/PoseDoll44/bench/revO22/verification/viewer_carrier.png

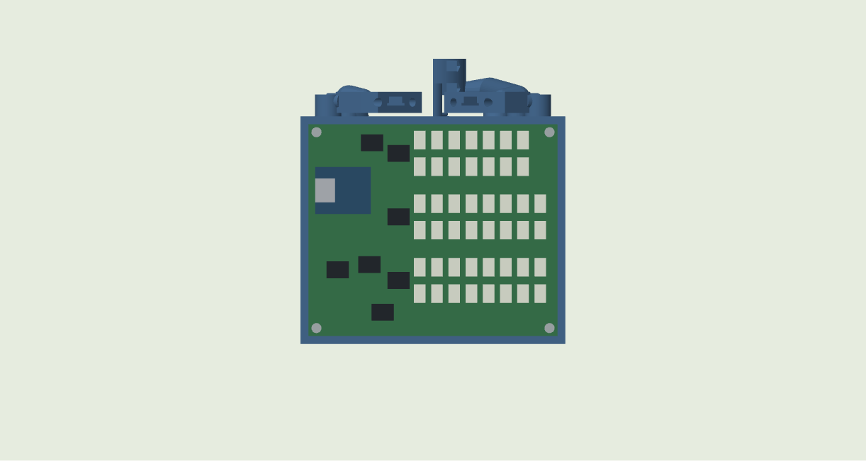
Hardware/PoseDoll44/bench/revO22/verification/viewer_carrier.png
