fukukawa89/PoseDollLab_Design/Hardware/PoseDoll44/generated/revO12/runs/o12_20260926_r1/page_verification/o12-exploded.png

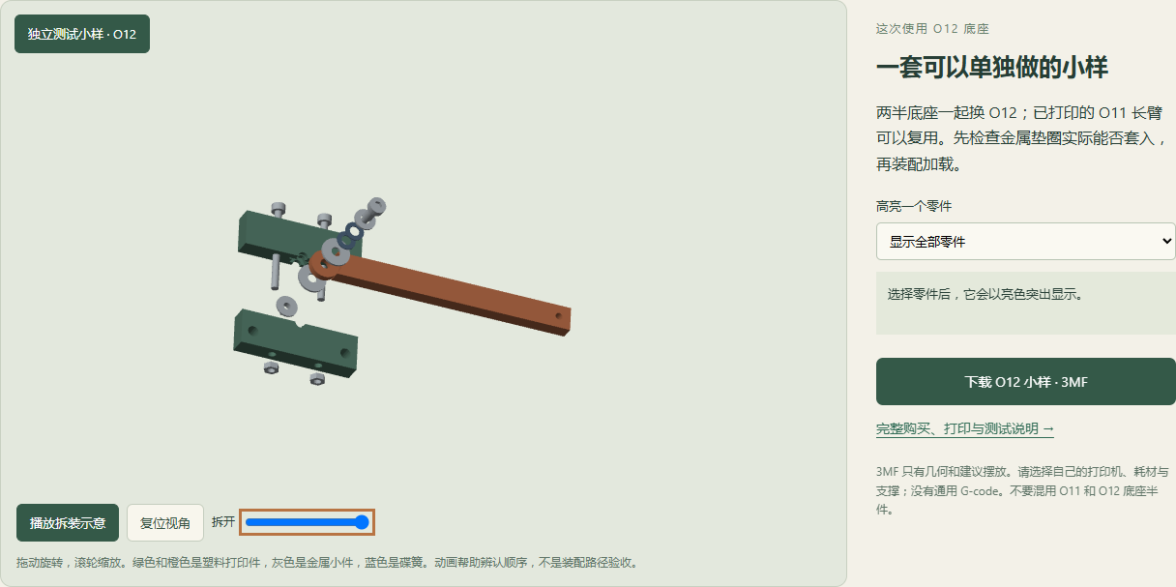
Hardware/PoseDoll44/generated/revO12/runs/o12_20260926_r1/page_verification/o12-exploded.png
