fukukawa89/PoseDollLab_Design/Hardware/PoseDoll44/generated/revO13/runs/o13_20260929_r1/page_verification/o13_core.png

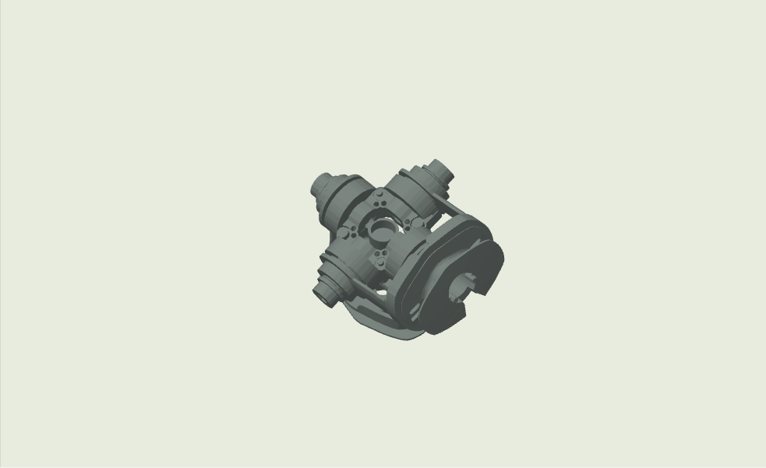
Hardware/PoseDoll44/generated/revO13/runs/o13_20260929_r1/page_verification/o13_core.png
