fukukawa89/PoseDollLab_Design/Hardware/PoseDoll44/tutorials/design-lab/verification/bench-mobile.png

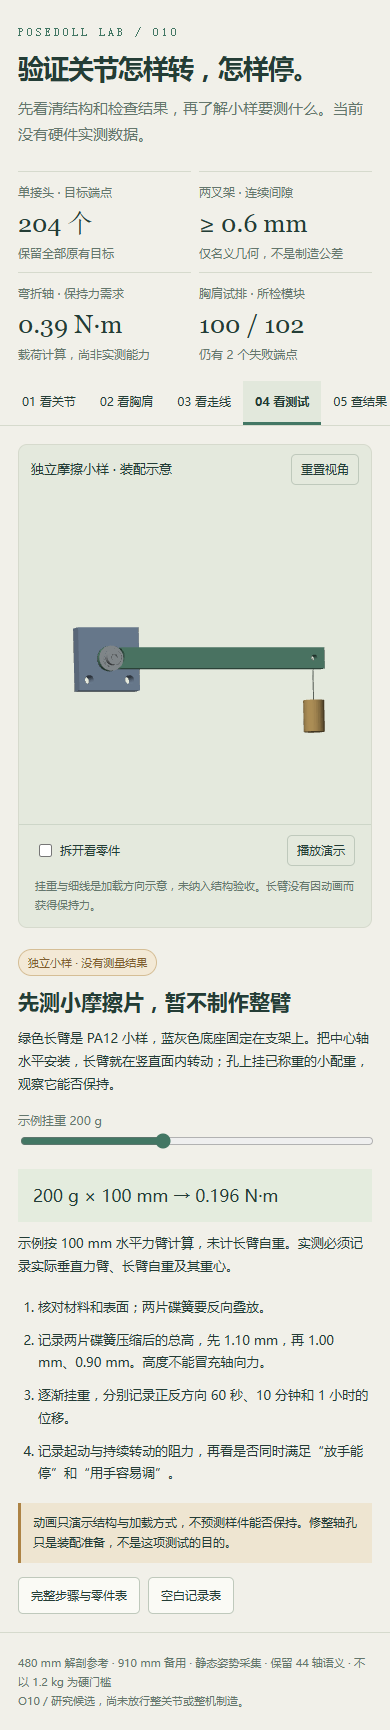
Hardware/PoseDoll44/tutorials/design-lab/verification/bench-mobile.png
