fukukawa89/PoseDollLab_Design/Hardware/PoseDoll44/tutorials/design-lab/verification/joint-desktop.png

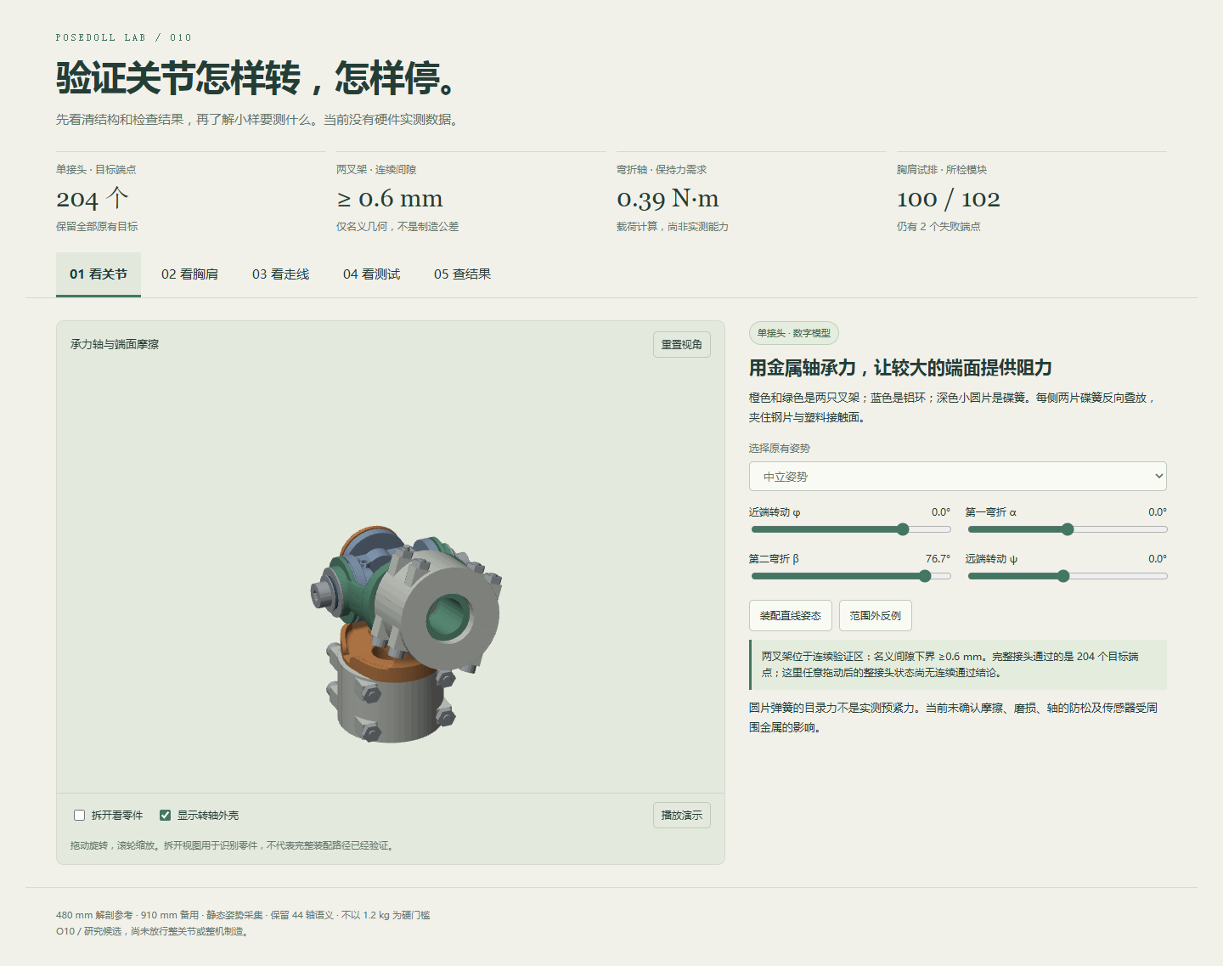
Hardware/PoseDoll44/tutorials/design-lab/verification/joint-desktop.png
