fukukawa89/PoseDollLab_Design/Hardware/PoseDoll44/tutorials/design-lab/verification/wire-candidate.png

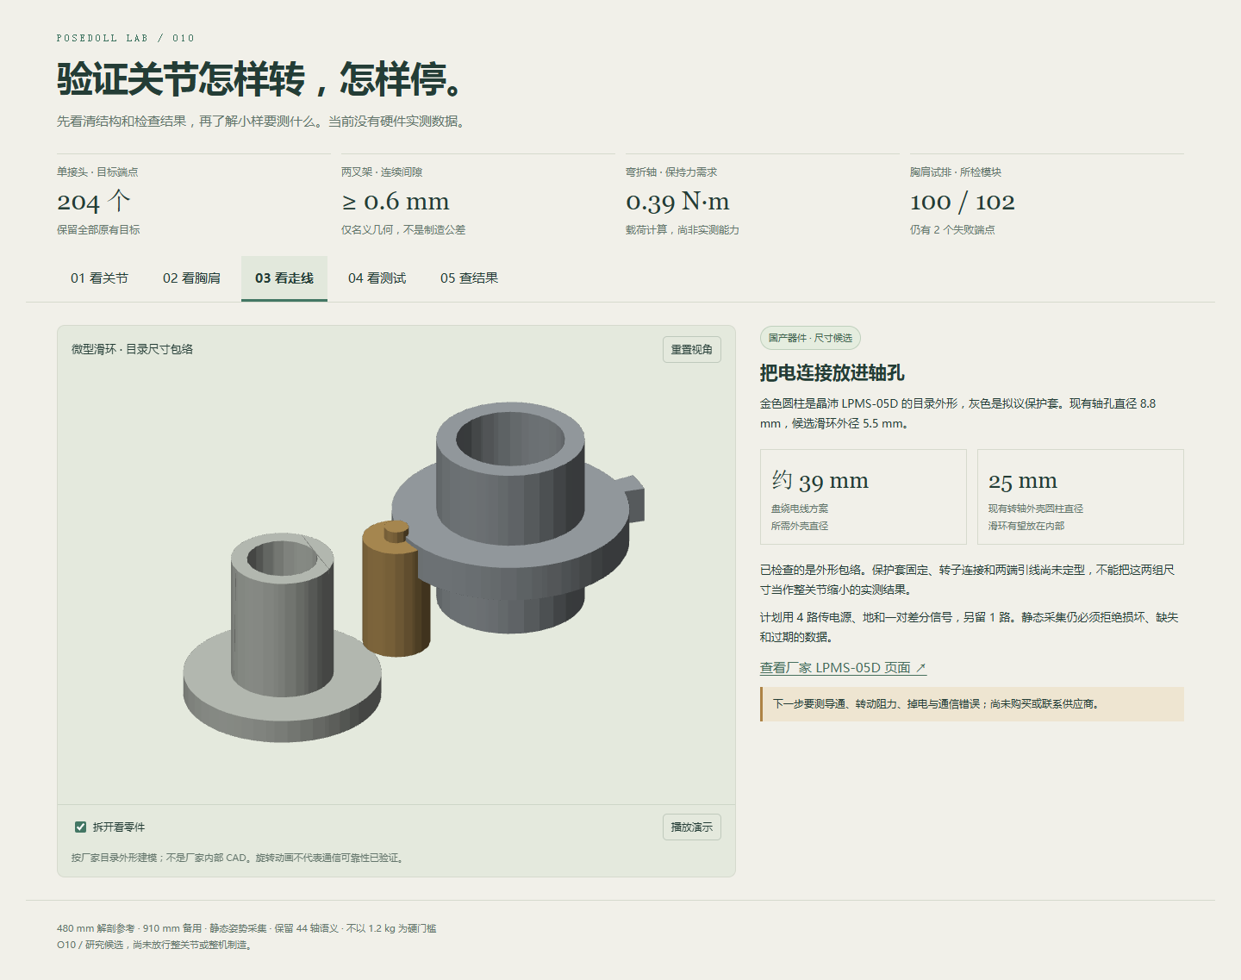
Hardware/PoseDoll44/tutorials/design-lab/verification/wire-candidate.png
