fukukawa89/PoseDollLab_Design/Hardware/PoseDoll44/tutorials/first-bench/verification/desktop-peek.png

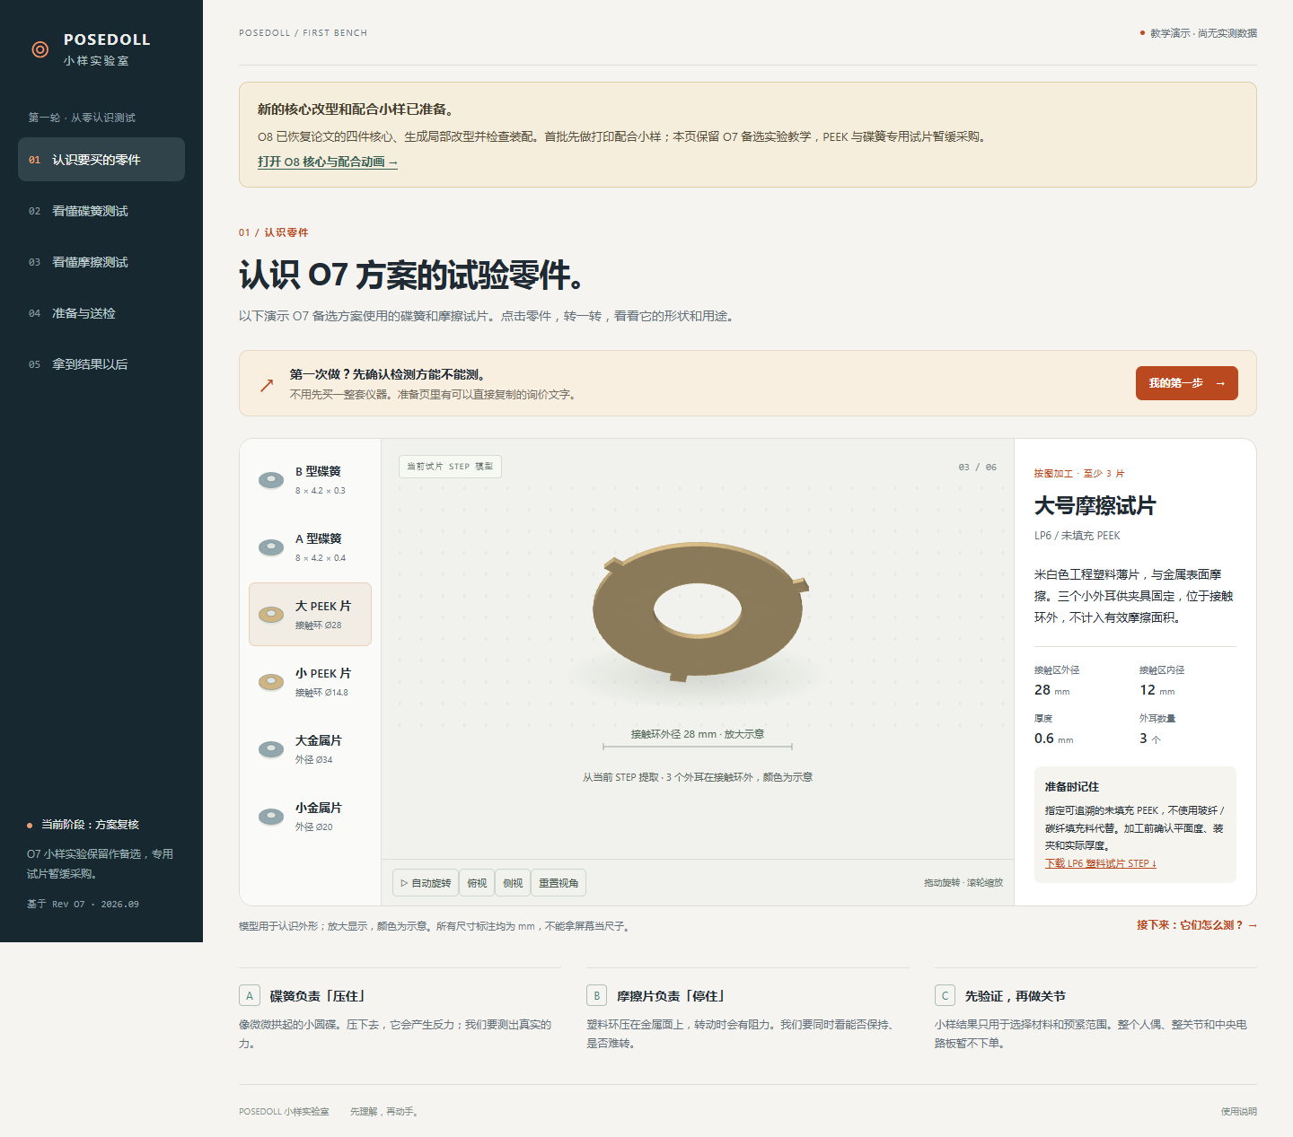
Hardware/PoseDoll44/tutorials/first-bench/verification/desktop-peek.png
