fukukawa89/PoseDollLab_Design/Hardware/PoseDoll44/tutorials/first-bench/verification/desktop-prepare.png

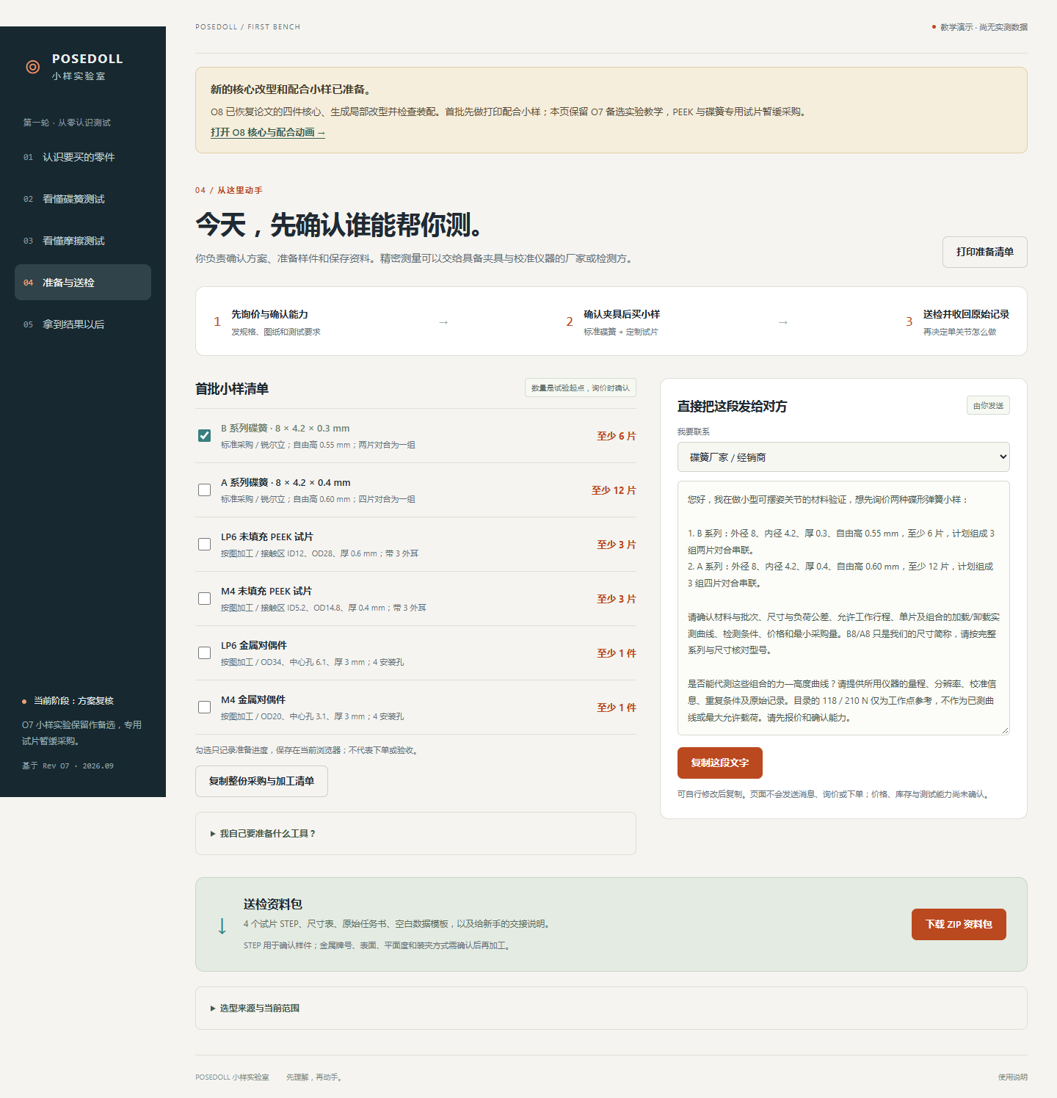
Hardware/PoseDoll44/tutorials/first-bench/verification/desktop-prepare.png
