fukukawa89/PoseDollLab_Design/Hardware/PoseDoll44/tutorials/first-bench/verification/mobile-friction.png

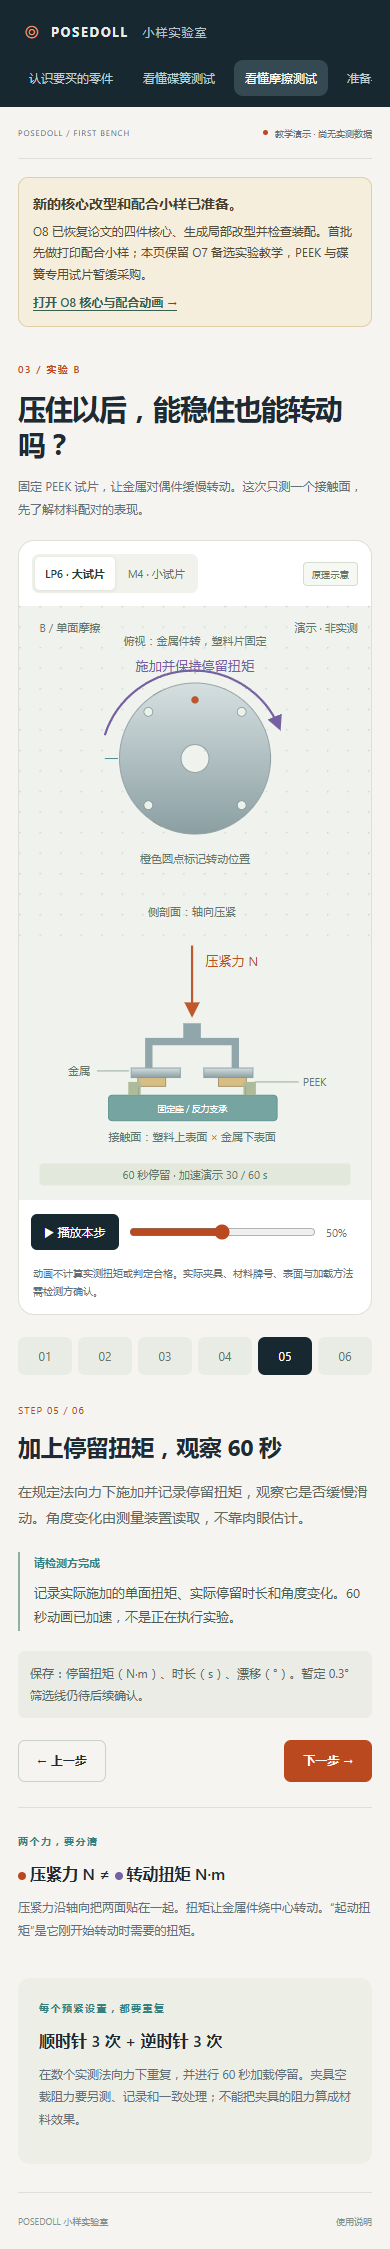
Hardware/PoseDoll44/tutorials/first-bench/verification/mobile-friction.png
