fukukawa89/PoseDollLab_Design/Hardware/PoseDoll44/tutorials/first-bench/verification/research-notice-375.png

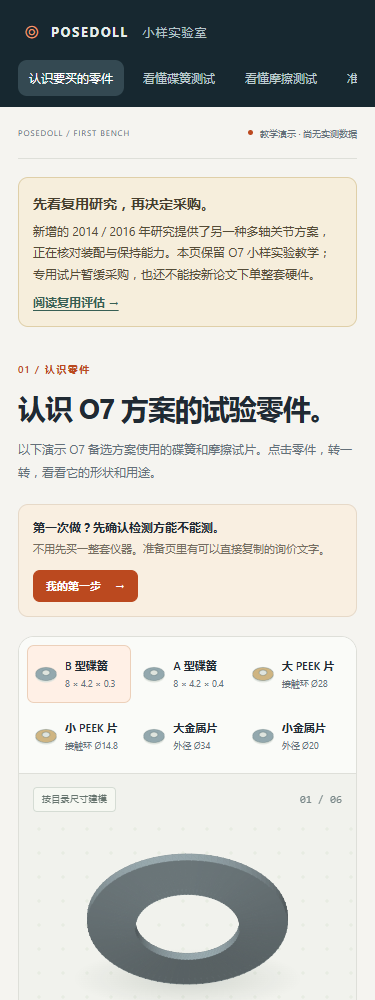
Hardware/PoseDoll44/tutorials/first-bench/verification/research-notice-375.png
