fukukawa89/PoseDollLab_Design/Hardware/PoseDoll44/tutorials/print-first/verification/bench-desktop.png

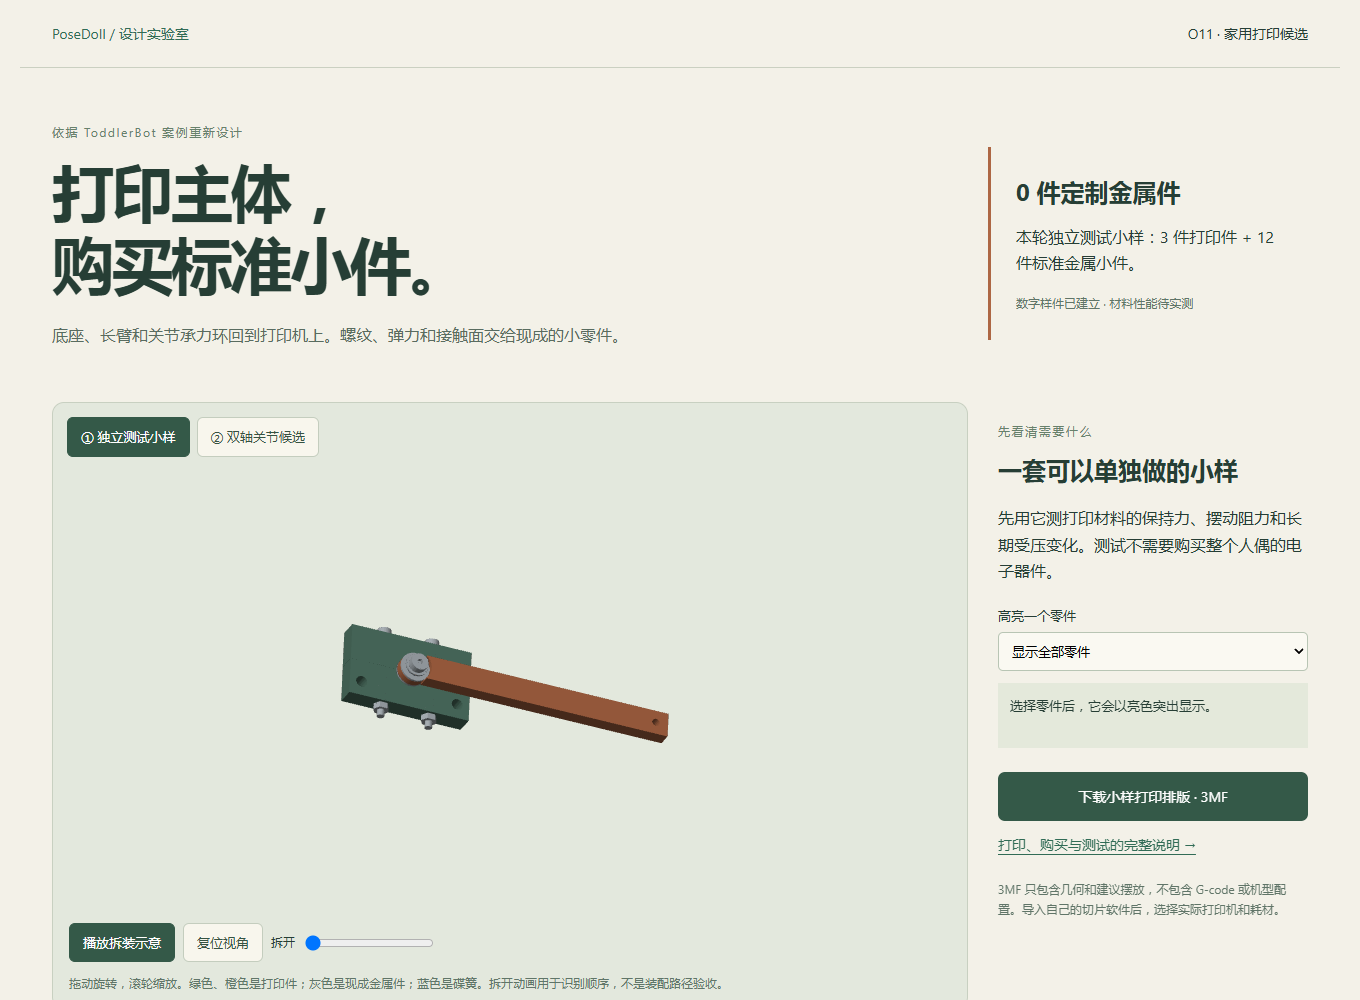
Hardware/PoseDoll44/tutorials/print-first/verification/bench-desktop.png
