fukukawa89/PoseDollLab_Design/Hardware/PoseDoll44/tutorials/print-first/verification/mobile.png

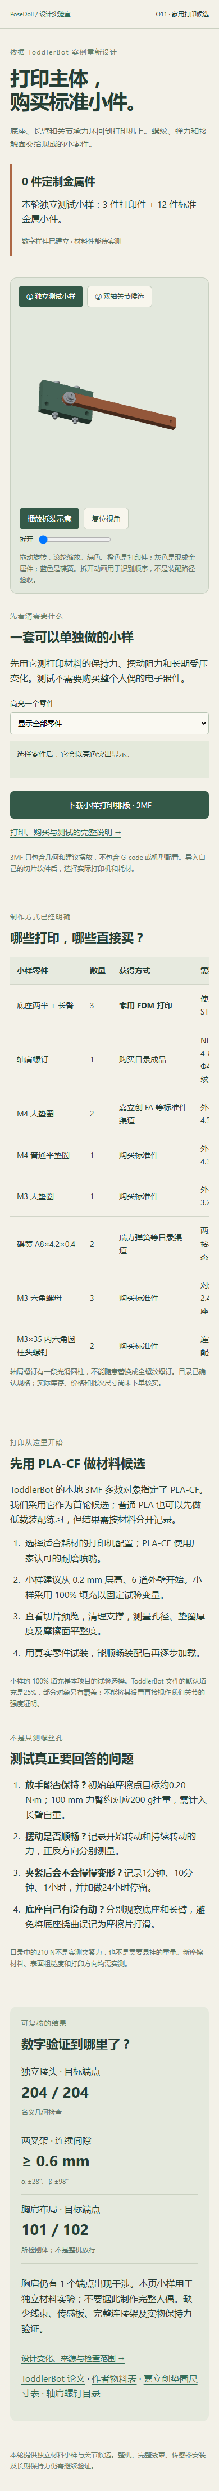
Hardware/PoseDoll44/tutorials/print-first/verification/mobile.png
