fukukawa89/PoseDollLab_Design/Hardware/PoseDoll44/tutorials/design-lab/verification/shoulder-failure.png

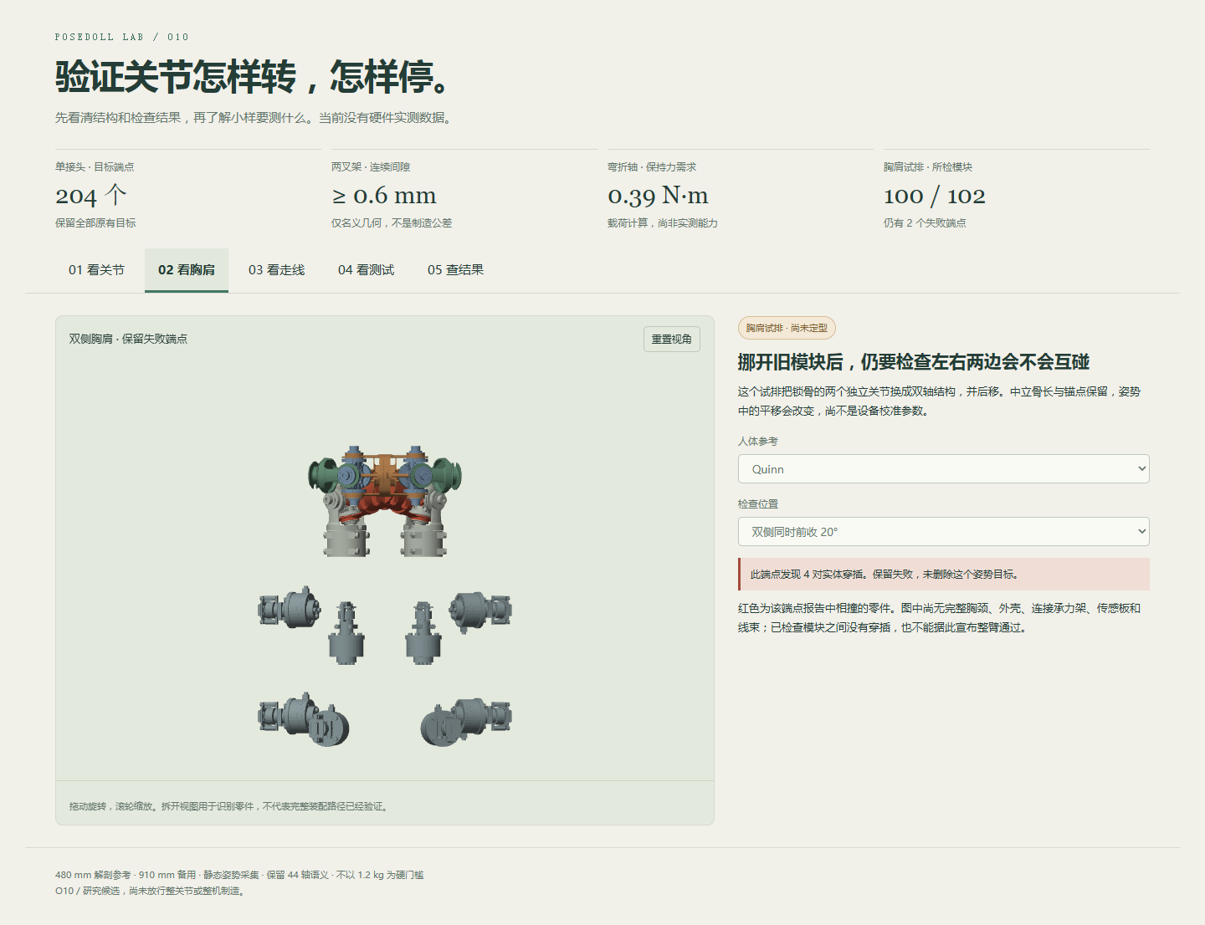
Hardware/PoseDoll44/tutorials/design-lab/verification/shoulder-failure.png
