fukukawa89/PoseDollLab_Design/scripts/seal_revo12.py

"""Seal O12 coupon evidence; physical fit, spring force and strength stay unknown."""
from pathlib import Path
import sys, json, hashlib, subprocess
R=Path(__file__).resolve().parents[1]; H=R/'Hardware/PoseDoll44'
G=H/'generated/revO12/runs/o12_20260926_r1'; B=H/'bench/revO12'; PAGE=H/'tutorials/taobao-bench'
DEST=G/'evidence_manifest.json'
def sha(p): return hashlib.sha256(p.read_bytes()).hexdigest()
def read(p): return json.loads(p.read_text(encoding='utf-8-sig'),parse_constant=lambda s:(_ for _ in ()).throw(ValueError(s)))
def upstream():
    r=subprocess.run([sys.executable,'-X','utf8',str(R/'scripts/seal_revo11.py'),'--verify'],cwd=R,capture_output=True,text=True,encoding='utf-8')
    assert r.returncode==0,r.stdout+r.stderr
    return json.loads(r.stdout)
def main():
    old=upstream()
    if '--verify' in sys.argv:
        m=read(DEST)
        bad=[n for n,d in m['repository_files_sha256'].items() if not (R/n).exists() or sha(R/n)!=d]
        print(json.dumps({'verified':not bad,'files':len(m['repository_files_sha256']),'errors':bad,'upstream_O11_verified':old['verified'],'physical_tested':False}))
        raise SystemExit(bool(bad))
    assert not DEST.exists(),'Use a new revision after sealing.'
    plan=read(B/'plan.json'); c=read(G/'digital_checks.json'); procurement=read(B/'procurement.json')
    ui=read(G/'page_checks.json')
    for report in (plan,c,ui):
        for n,d in report['inputs_sha256'].items(): assert sha(R/n)==d,('changed dependency',n)
    assert plan['physical_tested'] is False and plan['manufacturing_released'] is False
    assert plan['stock_parts_fit_confirmed'] is False and plan['spring_force_N'] is None and not plan['reuse_O11_210N_force_reference']
    assert len(plan['parts'])==15 and not plan['nominal_findings']
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
